wyolum/ClockFOUR/fabricate_bak/ClockFOUR_Chronogram_v2.1/Files to send Seeed/sides_C4_v2.1.pdf

ClockFOUR sides C4_v2.1

TOP = 276 x 20 x 3 mm

BOTTOM = 276 x 20 x 3 mm

LEFT = 270 x 20 x 3 mm

RIGHT = 270 x 20 x 3 mm
