wyolum/ClockFOUR/fabricate_bak/ClockFOUR_Chronogram_v2.1/output/english_upper Helvetica_C4_v2.1.pdf

english_upper Helvetica C4_v2.1 276x276x3mm

BACKWARDS!! DO NOT PRINT!!
