wyolum/ClockFOUR/fabricate_bak/ClockFOUR_Chronogram_v2.1/Files to send Seeed/ClockFOURChronogramInstructions.pdf

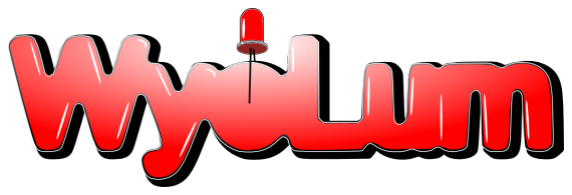
[picture p20: figure]

# ClockFOUR Chronogram Instructions

## Thank you for buying a Chronogram

Chronogram is a clock that tells the time with words. It has a 14x13 RGB pixel matrix that is powered by an external plugin 100-240V AC / 5V 3A power supply.

The clock has two main modes: Time mode and Seconds mode. You can switch between the modes by pressing the MODE button.

You can change the color palette of the clock by pressing the COLOR button. Each press will cycle the clock through the following color palettes:
- All white
- Solid color
- Slow color fade
- Rainbow color fade
- Random colors
- (all white)

Hold the color button to change the solid color. While the color button is held down you will see a circle that slowly changes color. When you see the desired color simply release the button and wait two seconds or tap the mode button.

Adjust the time by holding the MODE button for two seconds
- Adjust the hours slowly by tapping the COLOR button or quickly by holding it down. The hours will loop between 0 and 23 hours.
- When the correct hour is shown press the MODE button.
- Adjust the minutes slowly by tapping the COLOR button or quickly by holding the COLOR button down. The minutes will look between 0 and 59 minutes.
- When the correct minute is shown press the MODE button. The clock will return to time mode and also synchronize (zero) the seconds.

Pressing the RESET button will reboot the clock.

Caution:
Chronogram is designed to be enjoyed indoors only. It is not waterproof. Using a different power supply could damage the clock
