wyolum/ClockFOUR/fabricate/ClockFOUR_v1/output/baffles_v1_C4_v1.pdf

H baffle: 218x16x2mm; 14 per clock

V baffle: 216x14x2mm; 15 per clock

Localizer: Rout=4mm, Rin=1.5mm; 12 per clock

ClockFOUR_v1 Baffles 2mm BLACK Acrylic
