wyolum/ClockFOUR/fabricate/ClockFOUR_v1/output/english_C4_v1_lower Helvetica_C4_v1.pdf

english_C4_v1_lower Helvetica C4_v1

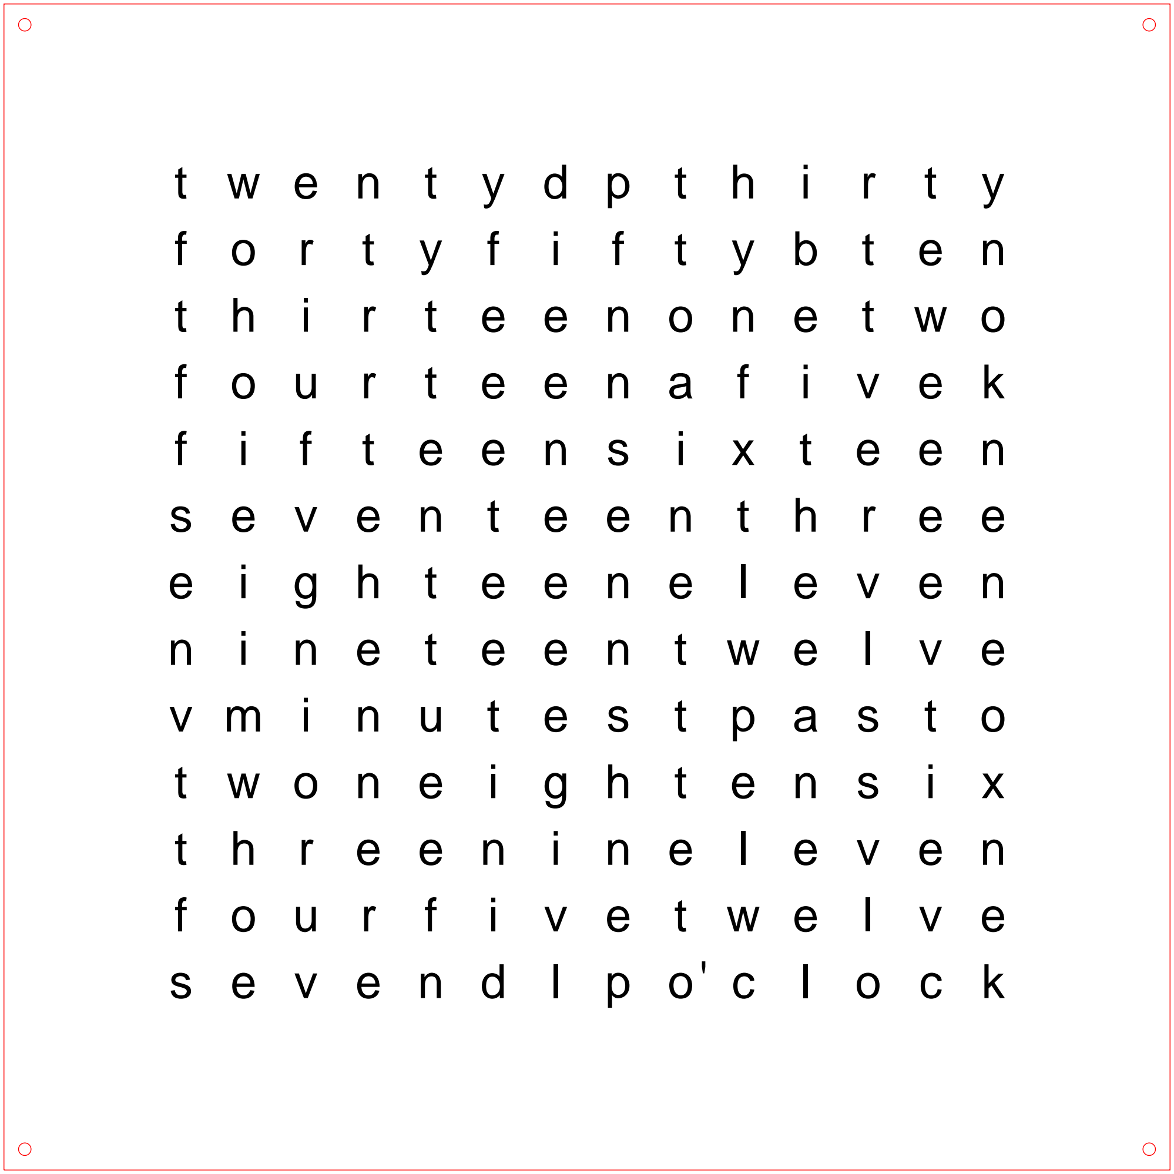
[picture p21: figure]

BACKWARDS!! DO NOT PRINT!!
