wyolum/ClockFOUR/fabricate/30x30 size/output/baffles_jr_30_1.0.pdf

H baffle: 15 per clock

V baffle: 14 per clock

Clock30_v1 Baffles 2mm BLACK Acrylic
