wyolum/ClockFOUR/fabricate/Vertical A4 10x10/output/baffles_VA4_30_1.0.pdf

H baffle: 11 per clock

V baffle: 11 per clock

ClockFOUR_VA4 Baffles 2mm BLACK Acrylic
