wyolum/ClockFOUR/fabricate/Vertical A4 10x10/output/Vertical A4.pdf

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
‘ | k

•

•

•

•
