wyolum/ClockFOUR/fabricate/30x30 size/output/english_30_UPPER Codystar-Regular_30_1.0.pdf

english_30_UPPER Codystar-Regular 30_1.0

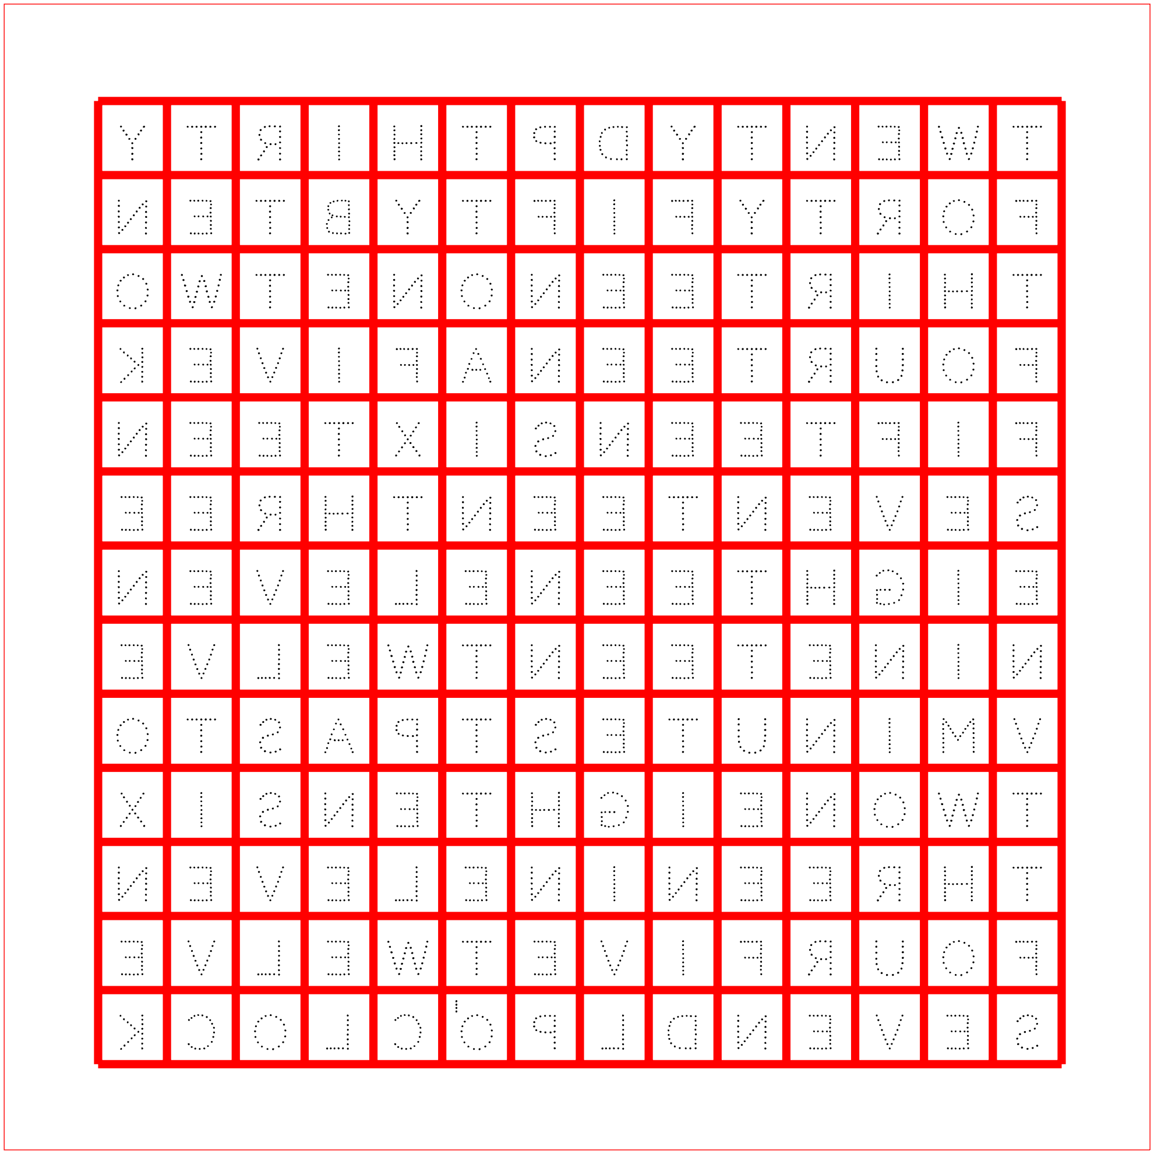
[picture p28: figure]
