wyolum/ClockFOUR/fabricate/A4 size/output/baffles_jr_TiM_1.0.pdf

H baffle: 9 per clock

V baffle: 17 per clock

localizer: 0 per clock

ClockTiM_v1 Baffles 0.06" BLACK Acrylic
