wyolum/ClockFOUR/fabricate/A4 size/output/english_TiM_lower Helvetica_TiM_1.0.pdf

english_TiM_lower Helvetica TiM_1.0

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

'
