wyolum/ClockFOUR/fabricate/Power_Socket_Bracket/C4_bracket_03.png

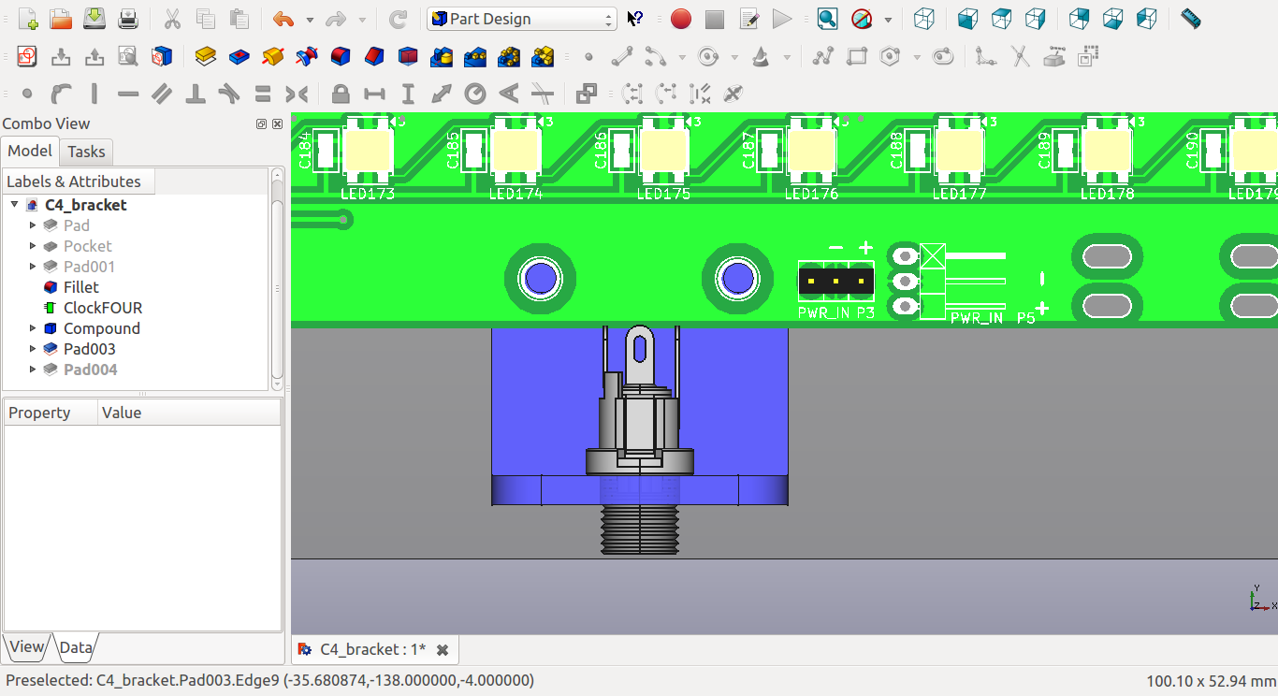
fabricate/Power_Socket_Bracket/C4_bracket_03.png
