wyolum/ClockFOUR/fabricate_bak/ClockFOUR_Chronogram_v2.1/C4 sides diagram.png

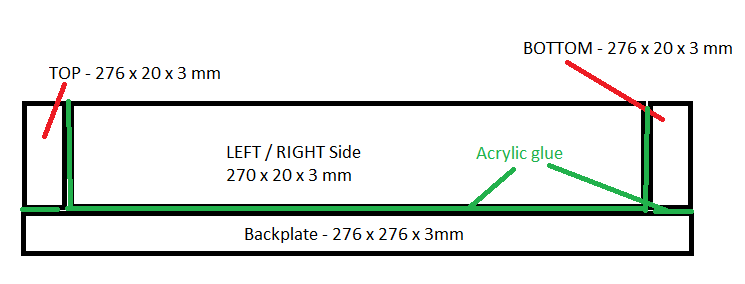
fabricate_bak/ClockFOUR_Chronogram_v2.1/C4 sides diagram.png
