wyolum/ClockFOUR/fabricate_bak/ClockFOUR_Chronogram_v2.1/Files to send Seeed/C4_v2 PCB (Same as v2.1)/ClockFOUR-B_SilkS.pdf

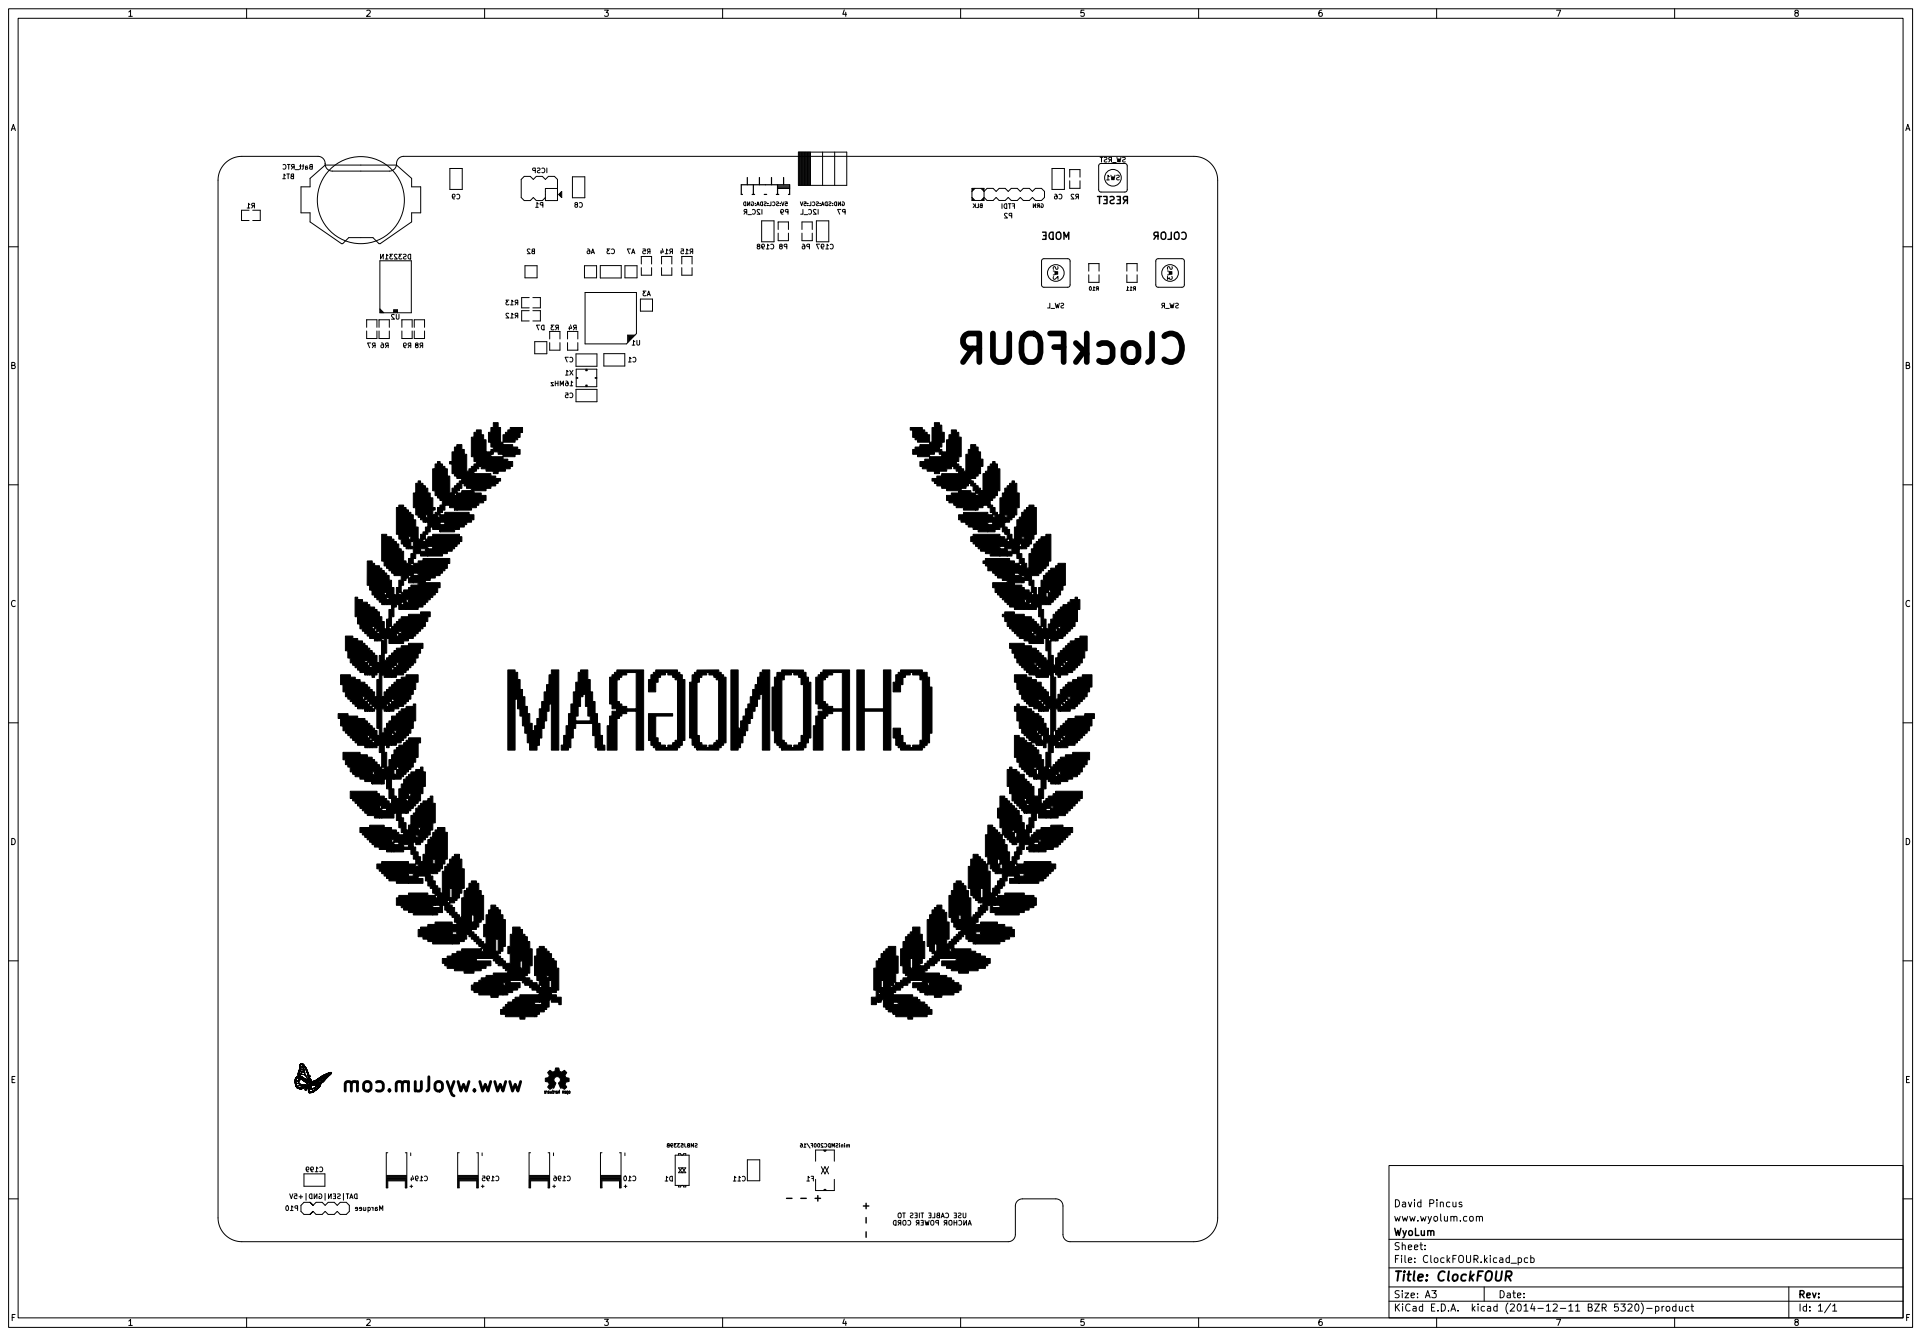
[picture p40: page 1]

David Pincus
www.wyolum.com
File: ClockFOUR.kicad_pcb Sheet: WyoLum
