wyolum/ClockFOUR/fabricate_bak/ClockFOUR_Chronogram_v2.1/Files to send Seeed/C4_v2 PCB (Same as v2.1)/ClockFOUR.pdf

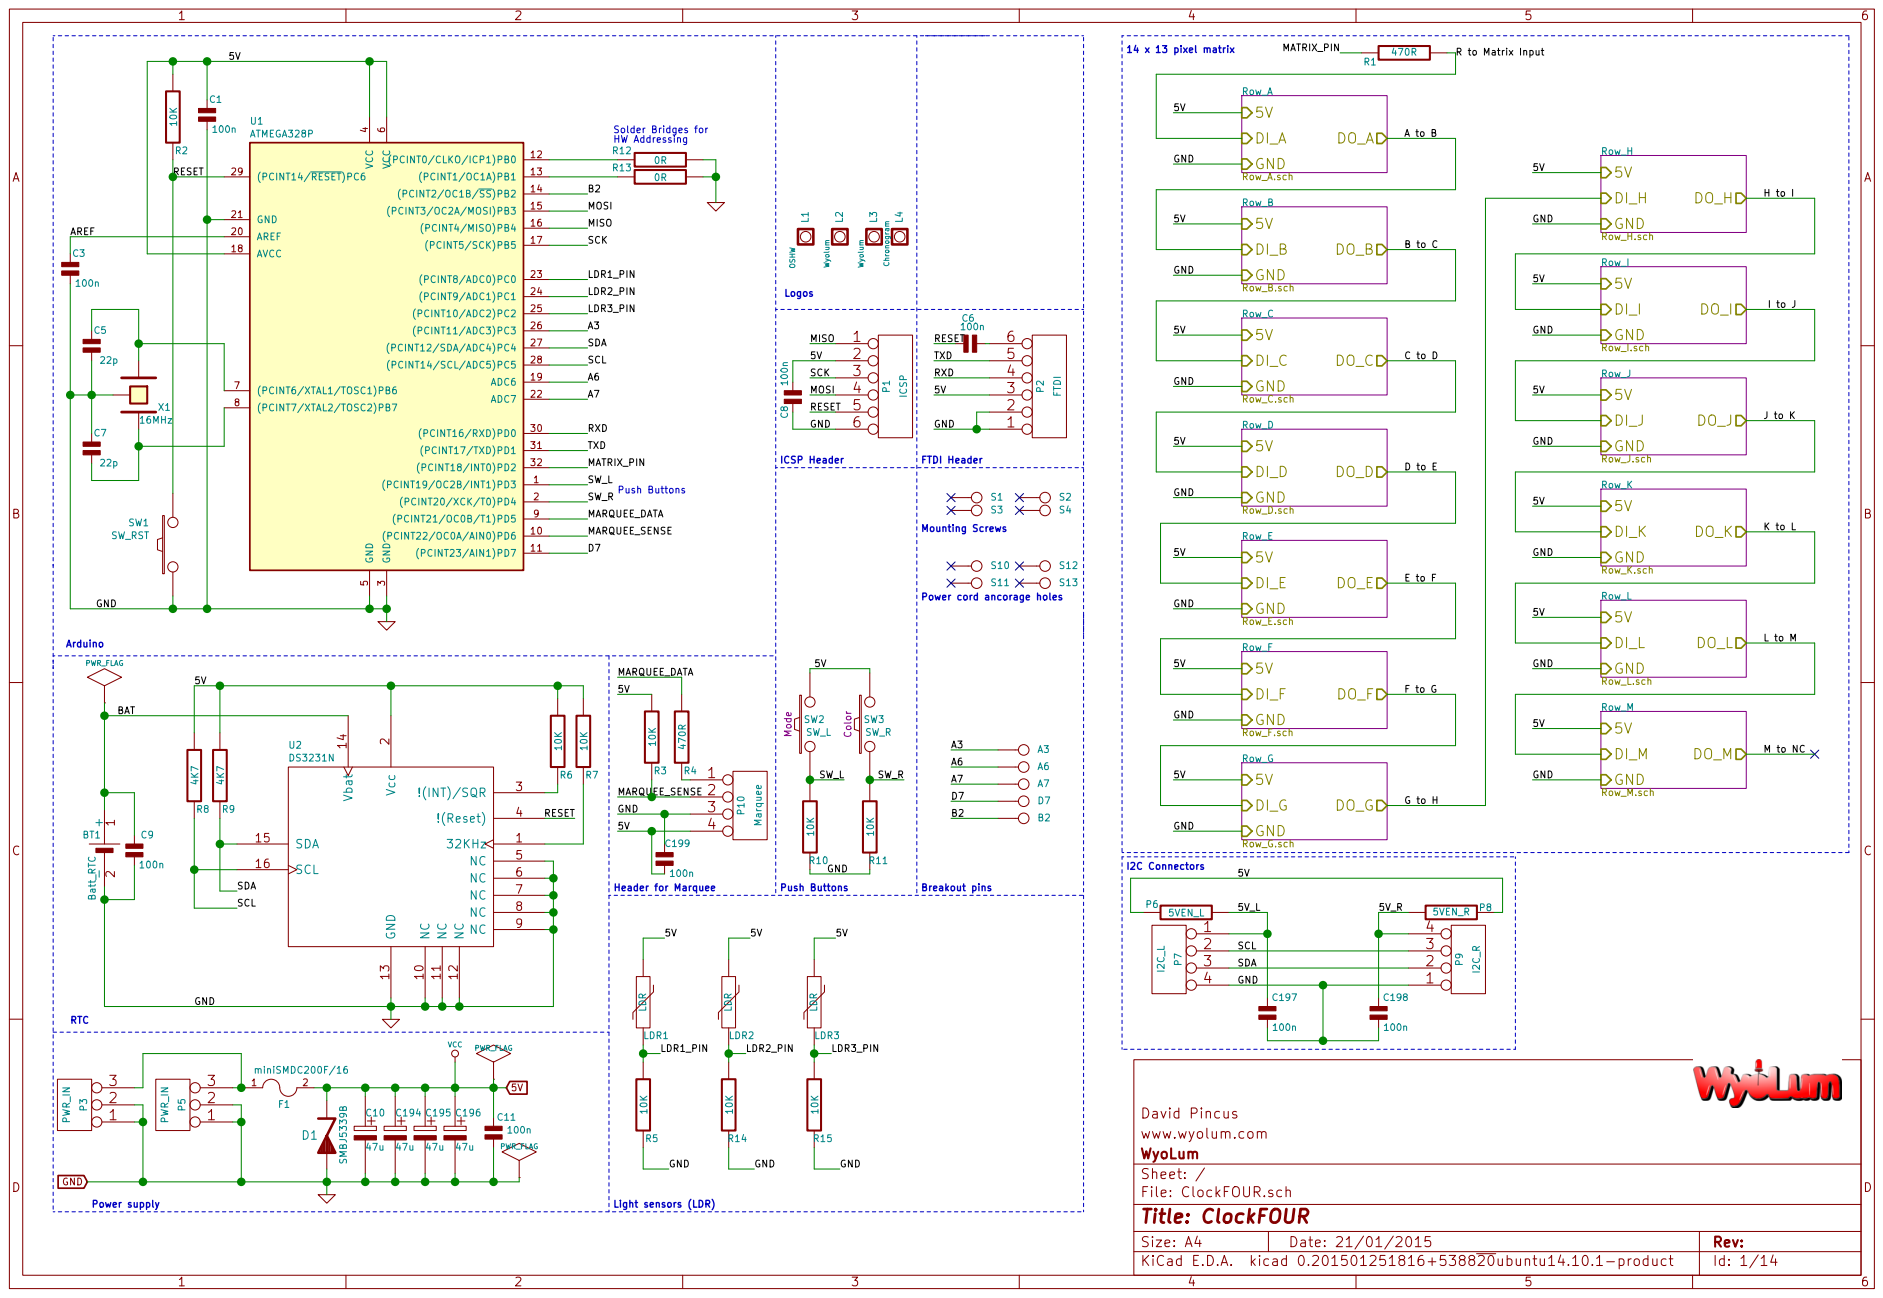
[picture p44: page 1]

100n RESET

5V Row_C.sch DI_C GND | DO_C

(PCINT6/XTAL1/TOSC1)PB6 7

5V GND

www.wyolum.com
File: ClockFOUR.sch Sheet: / WyoLum

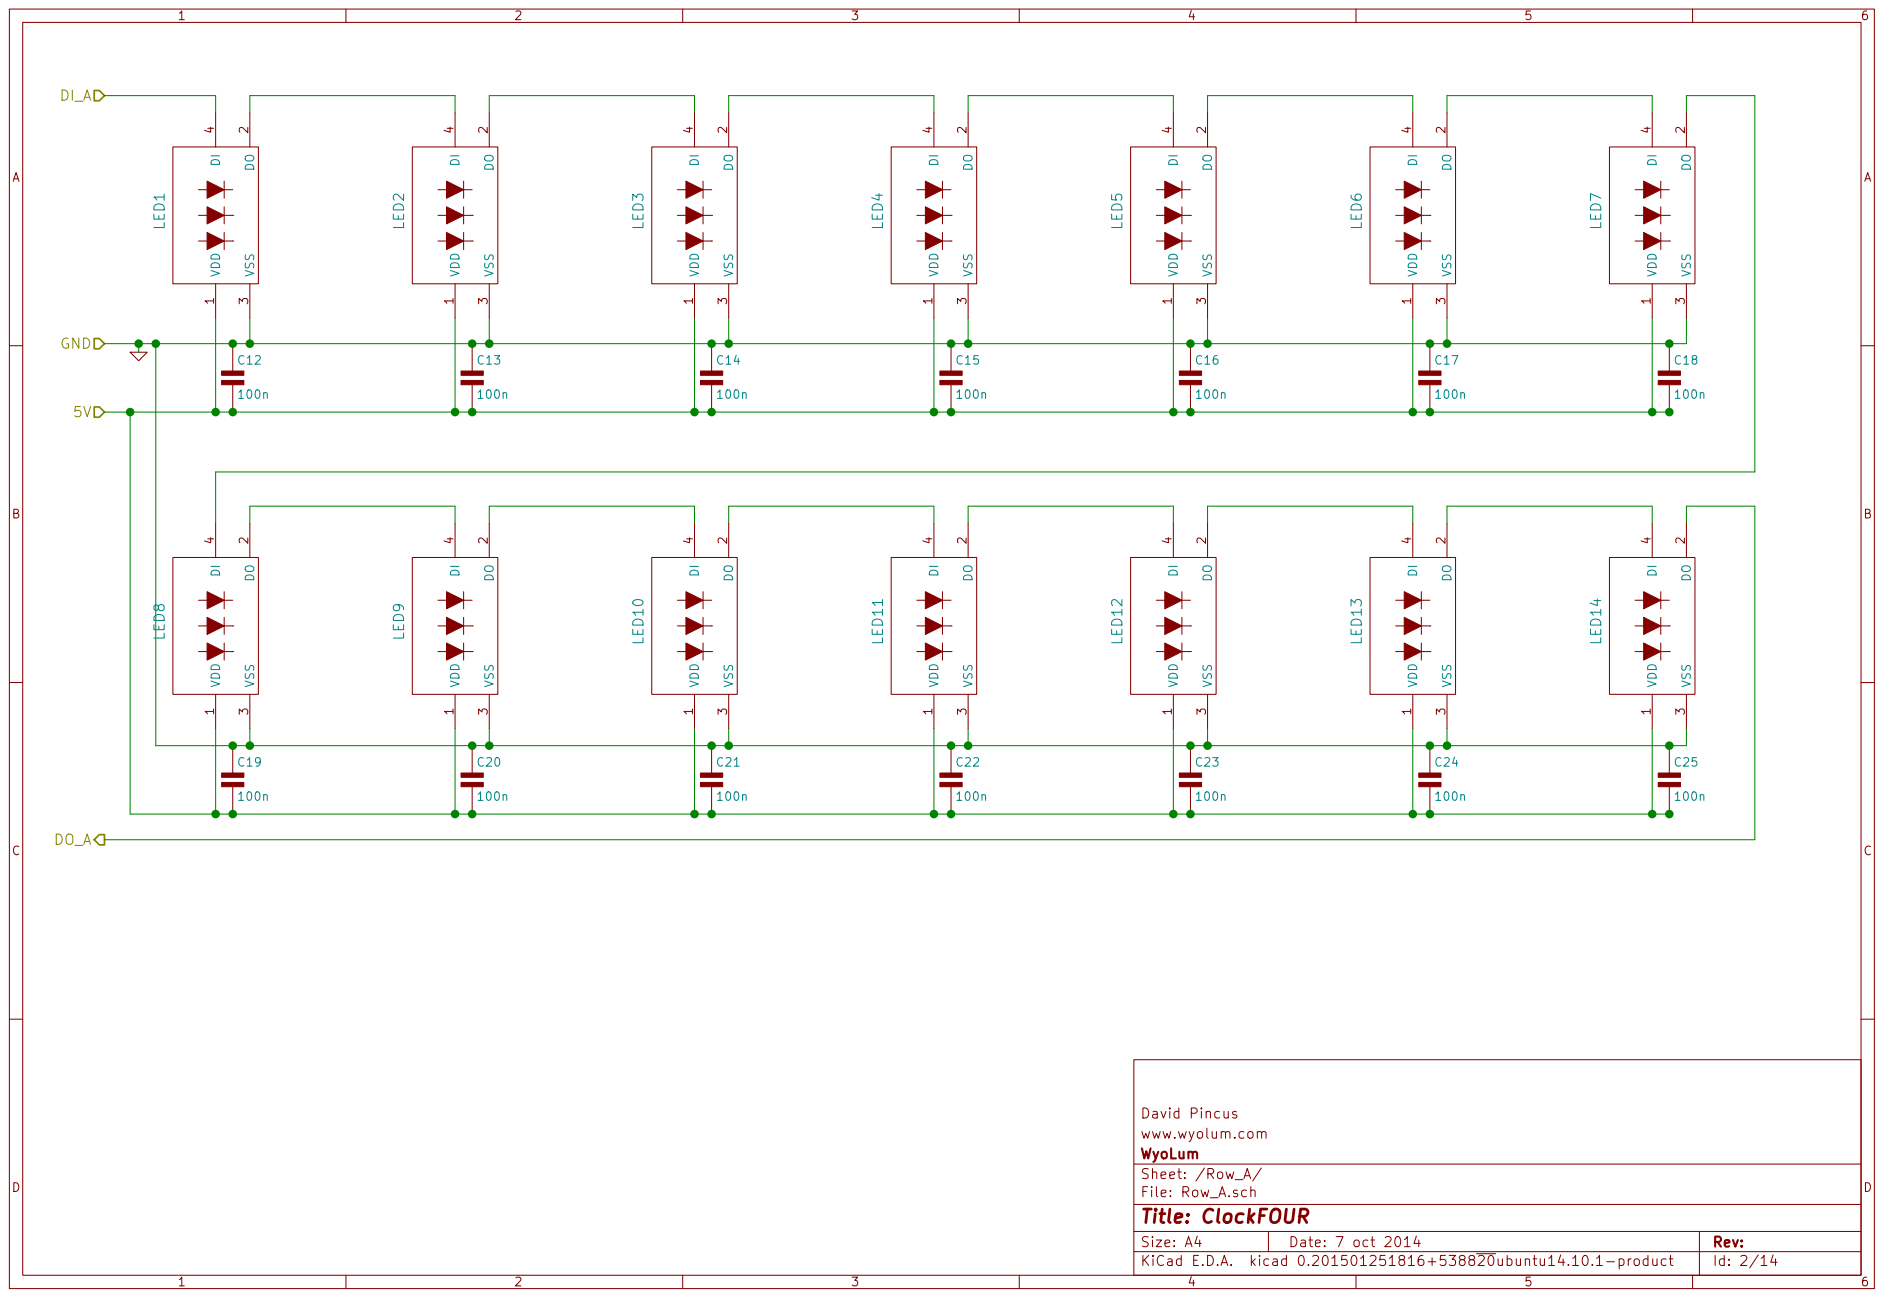
[picture p45: page 2]

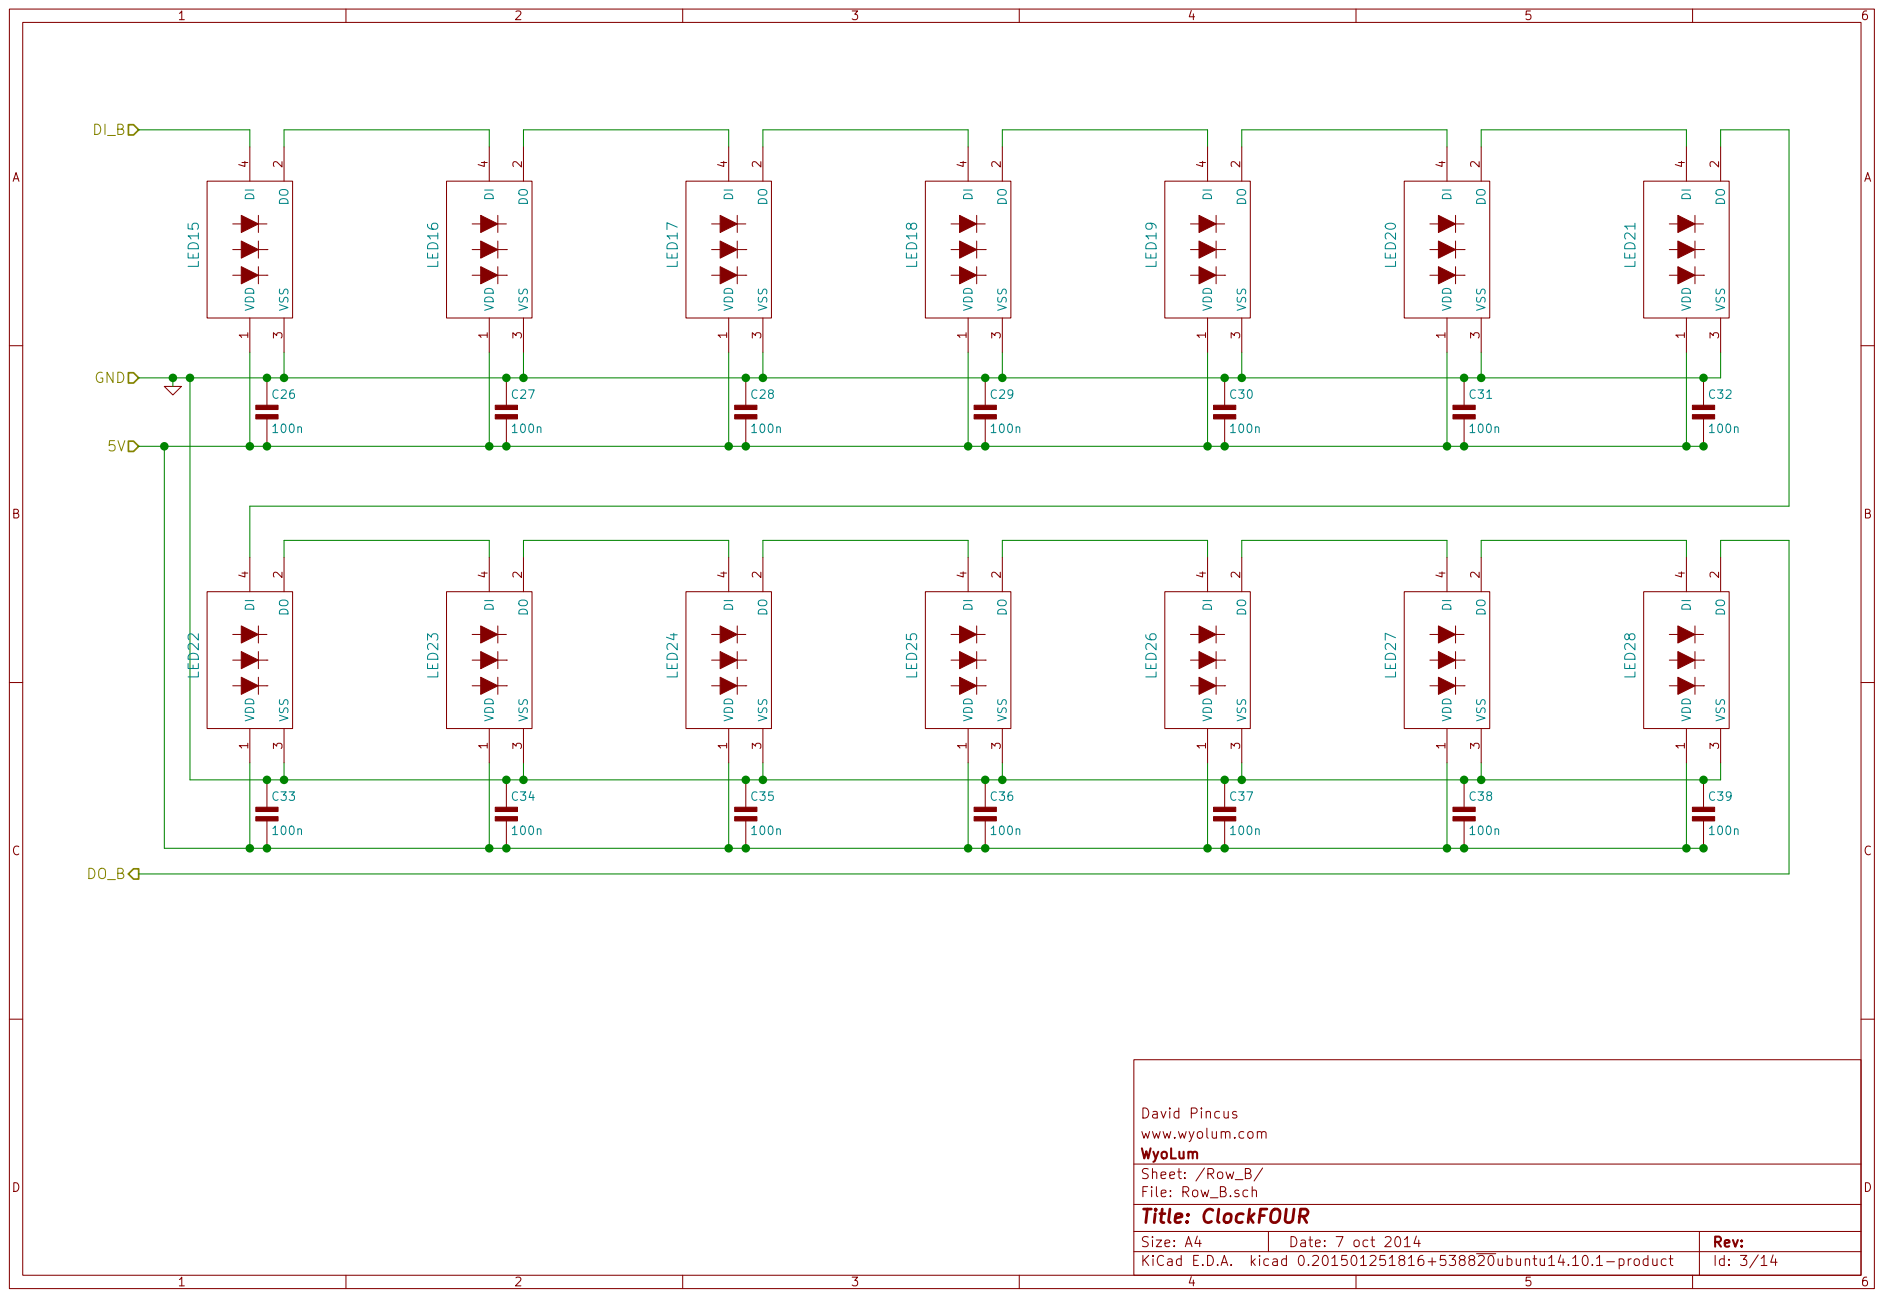
[picture p46: page 3]

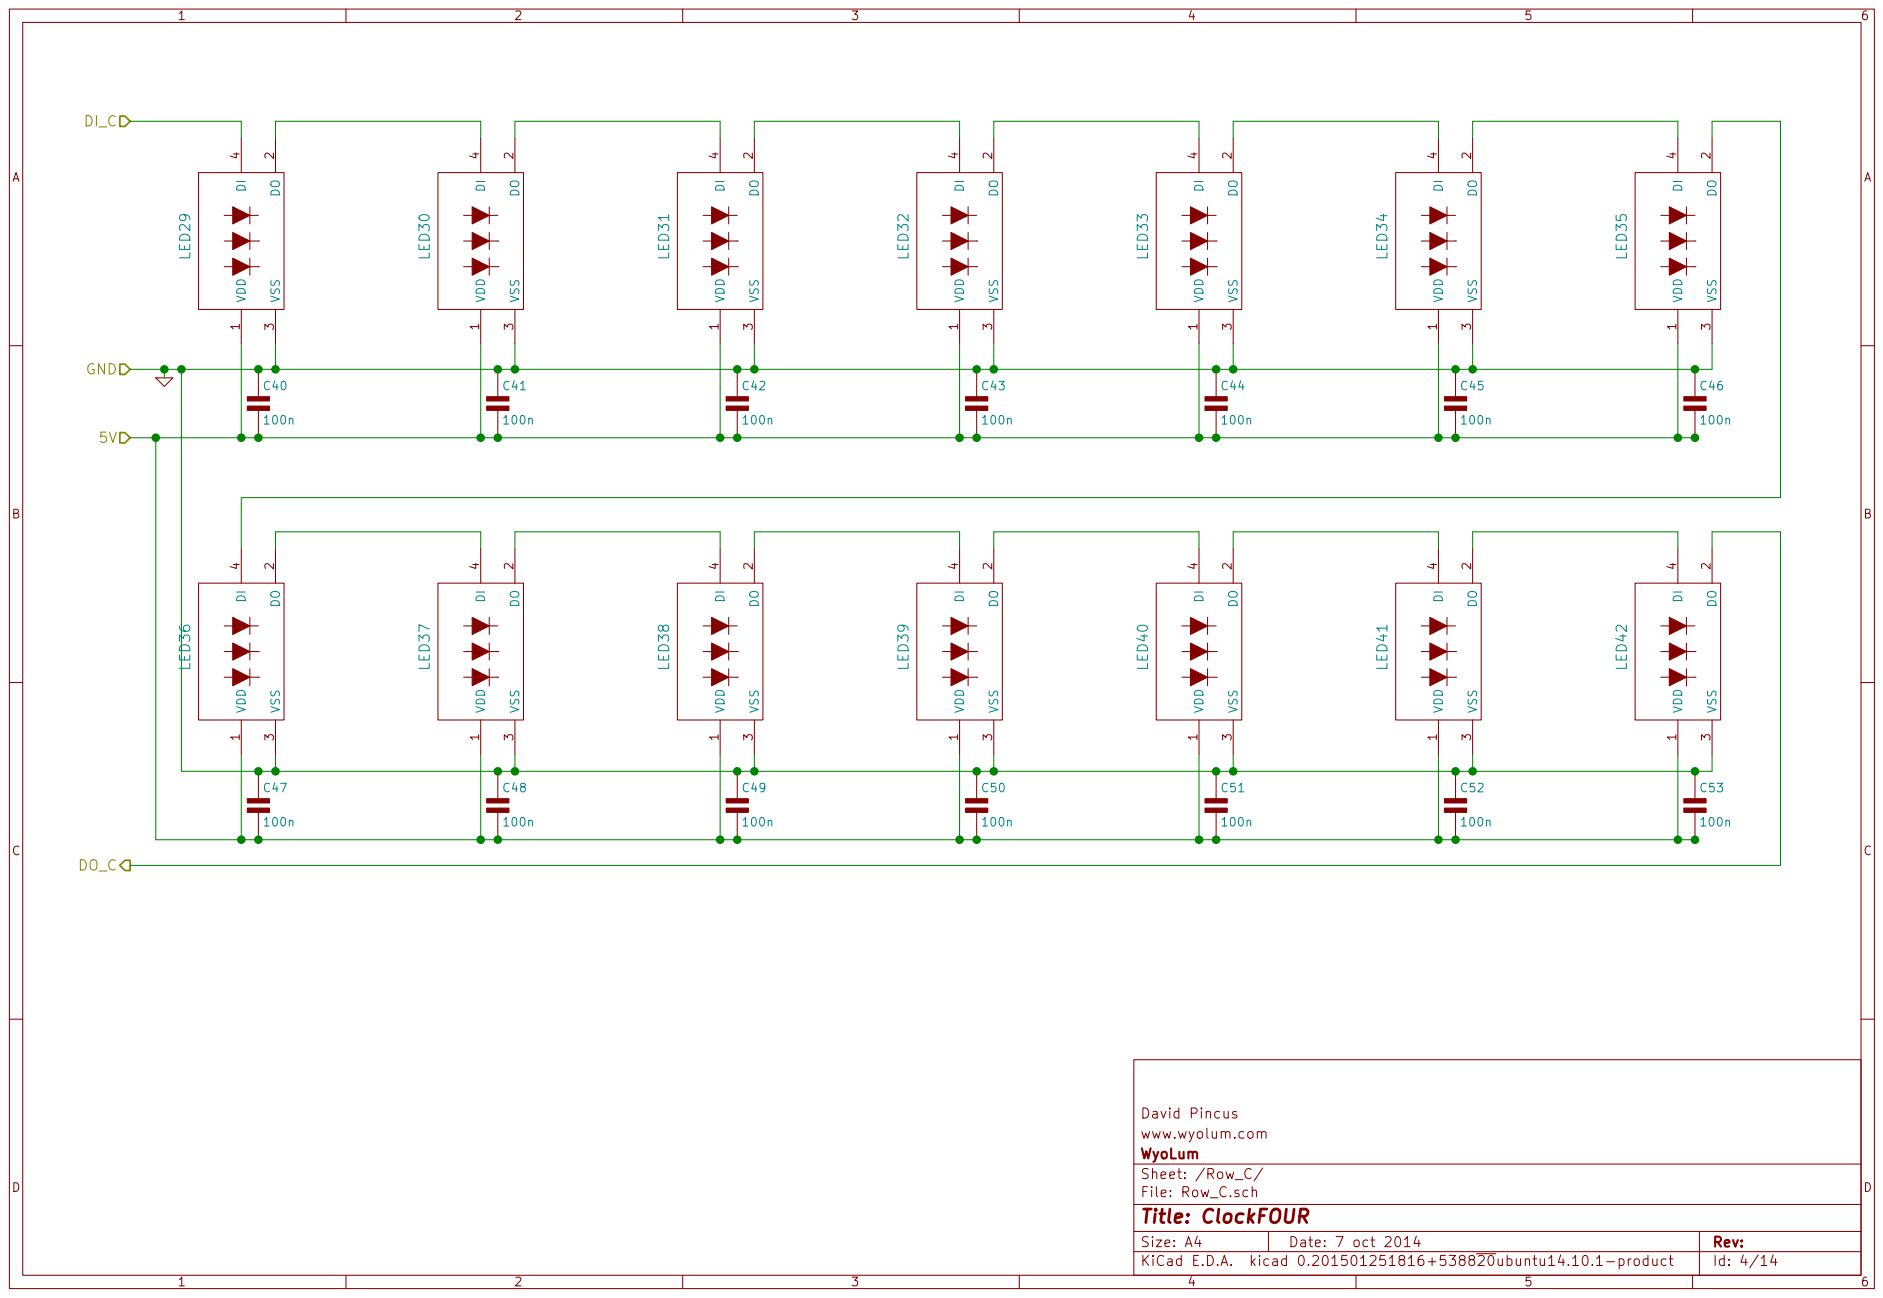
[picture p47: page 4]

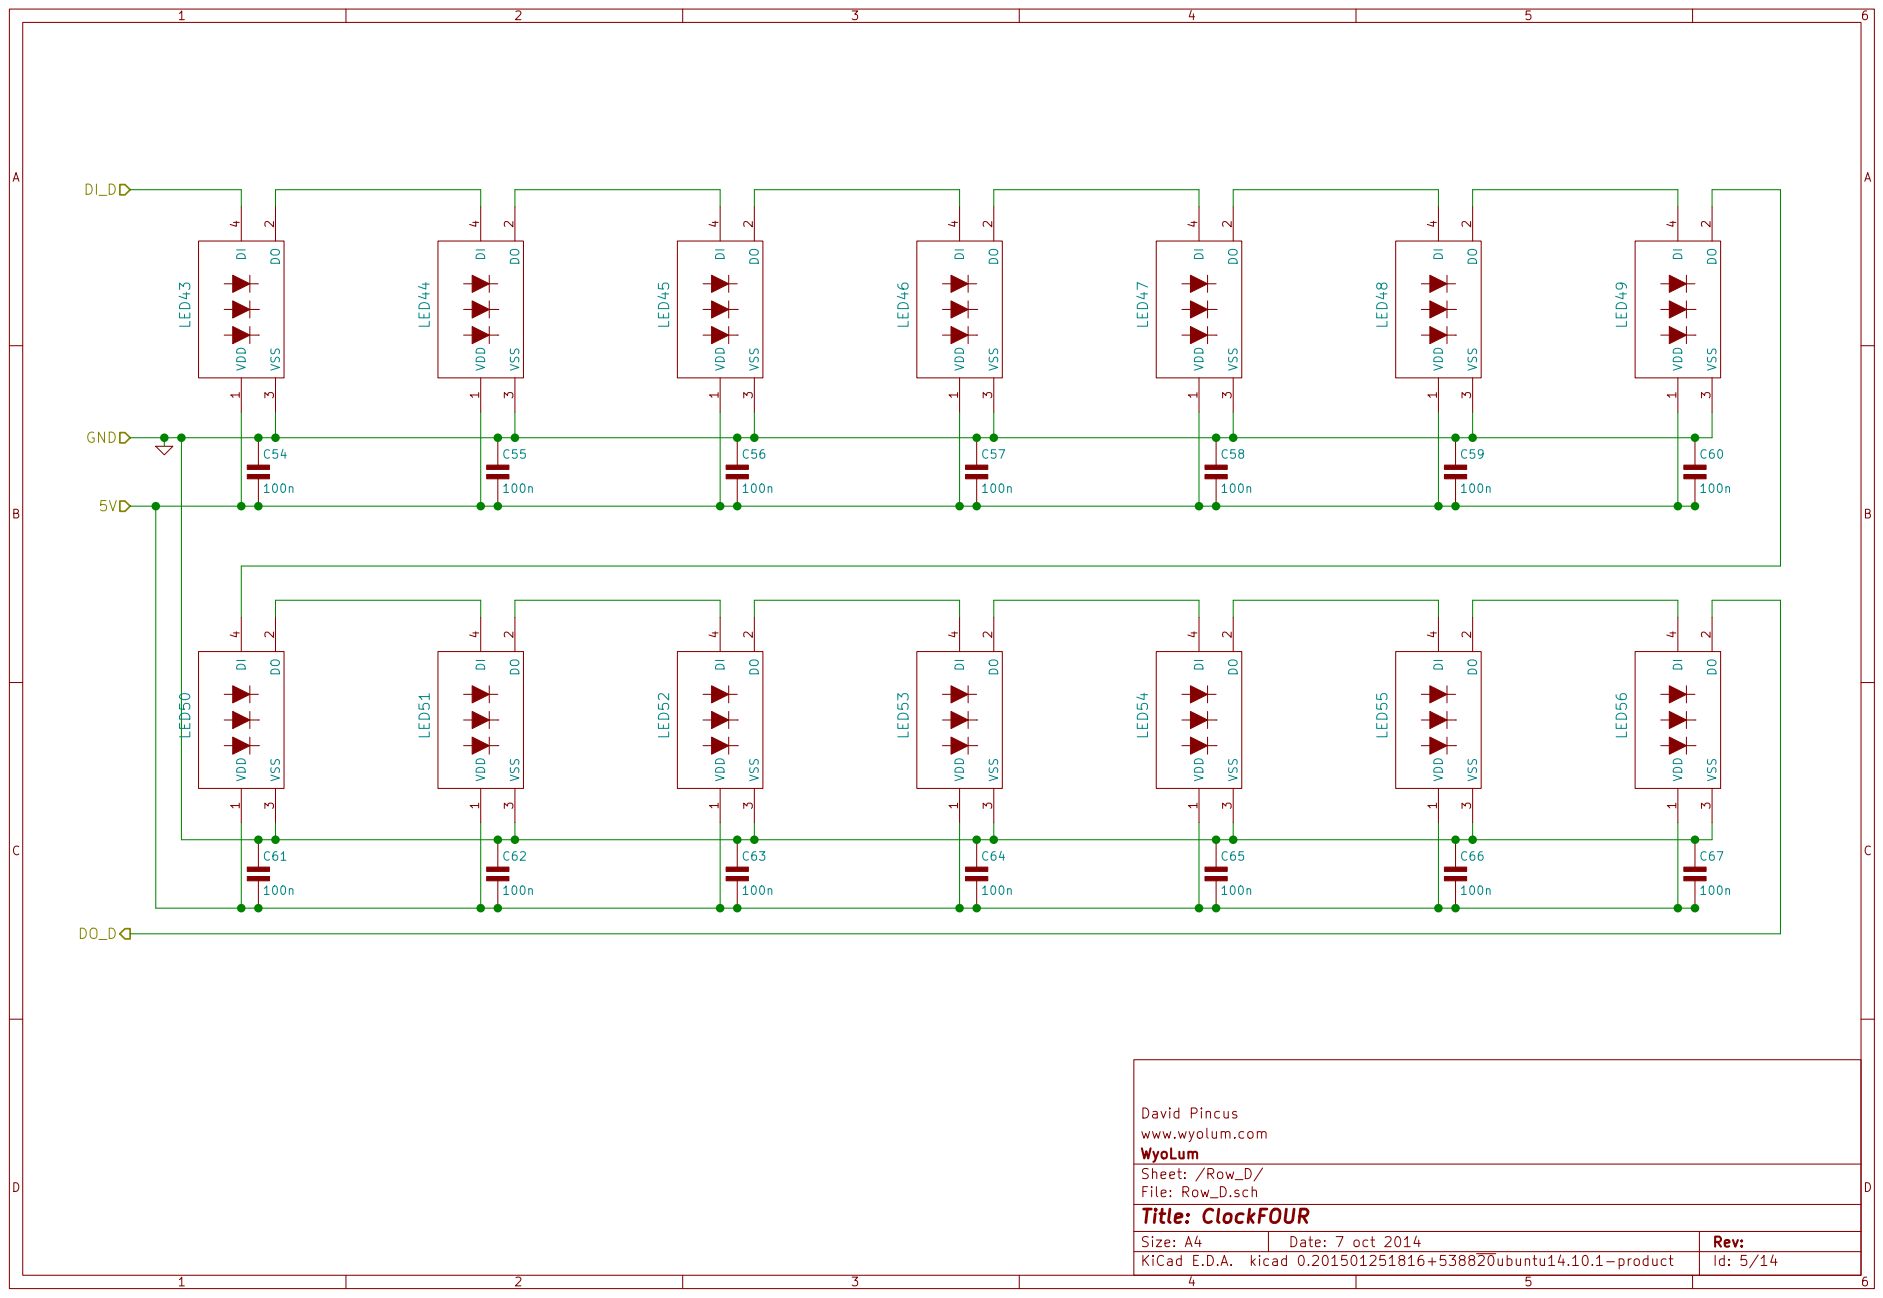
[picture p48: page 5]

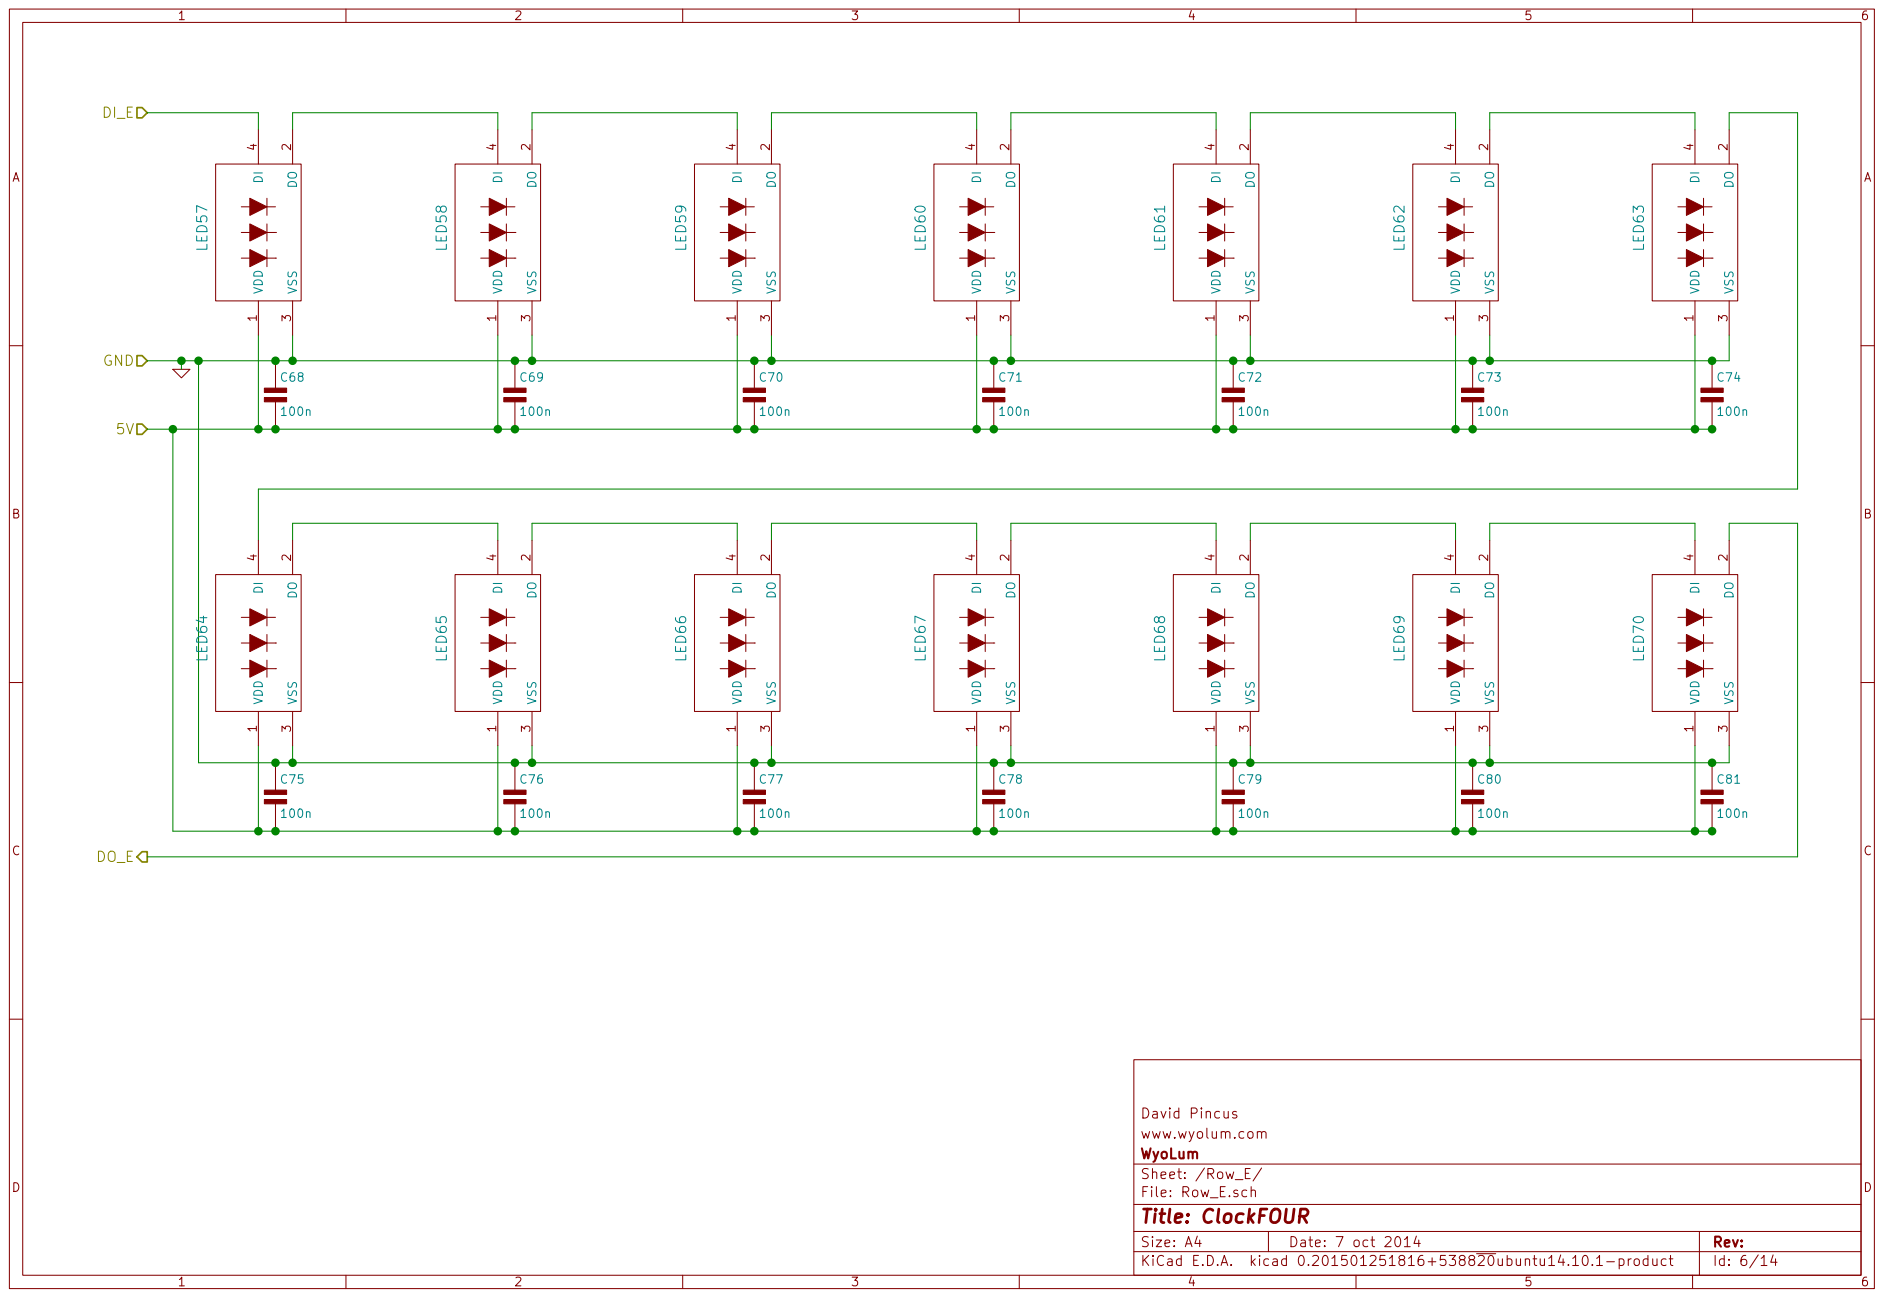
[picture p49: page 6]

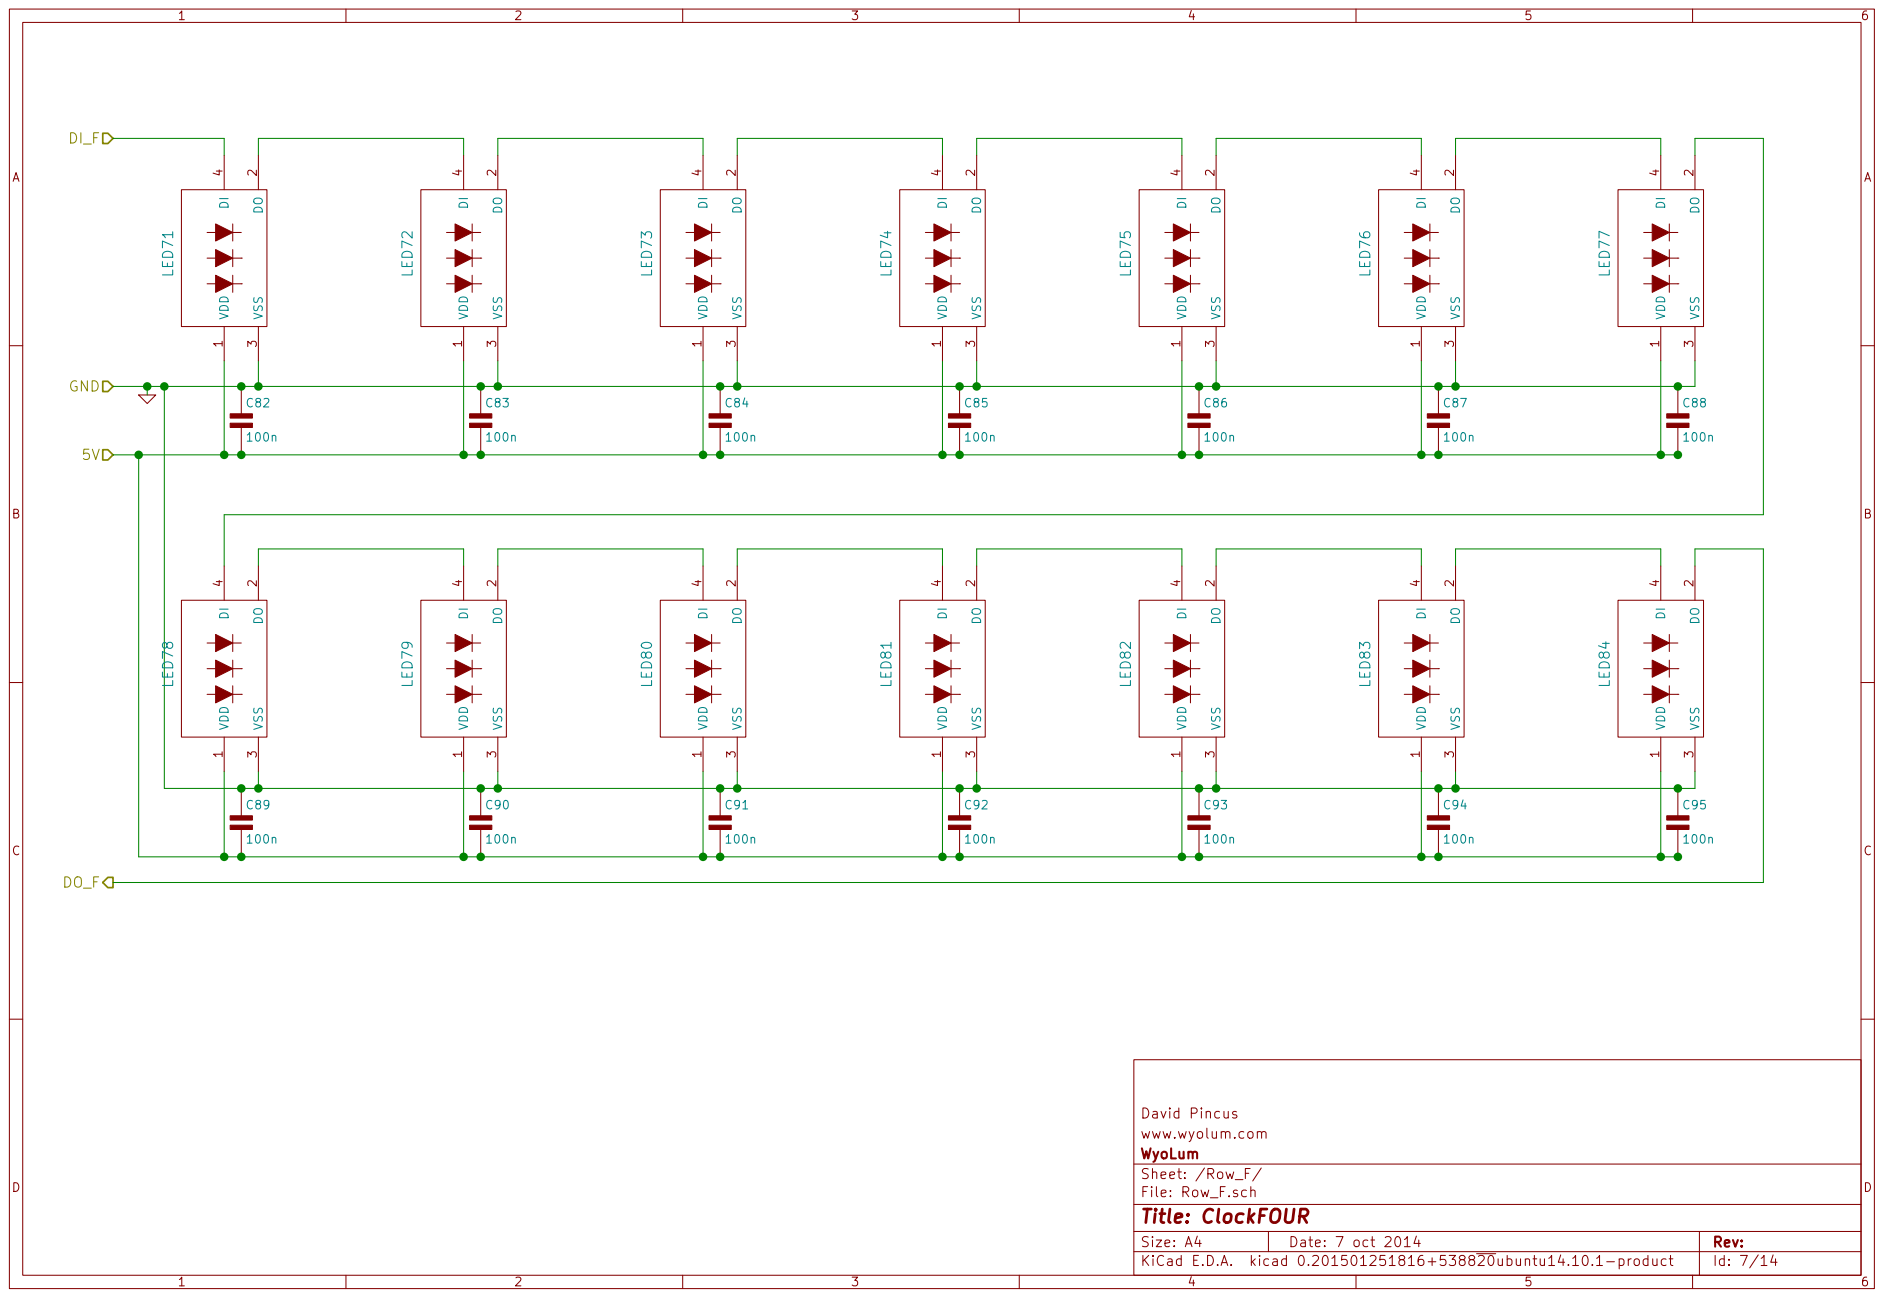
[picture p50: page 7]

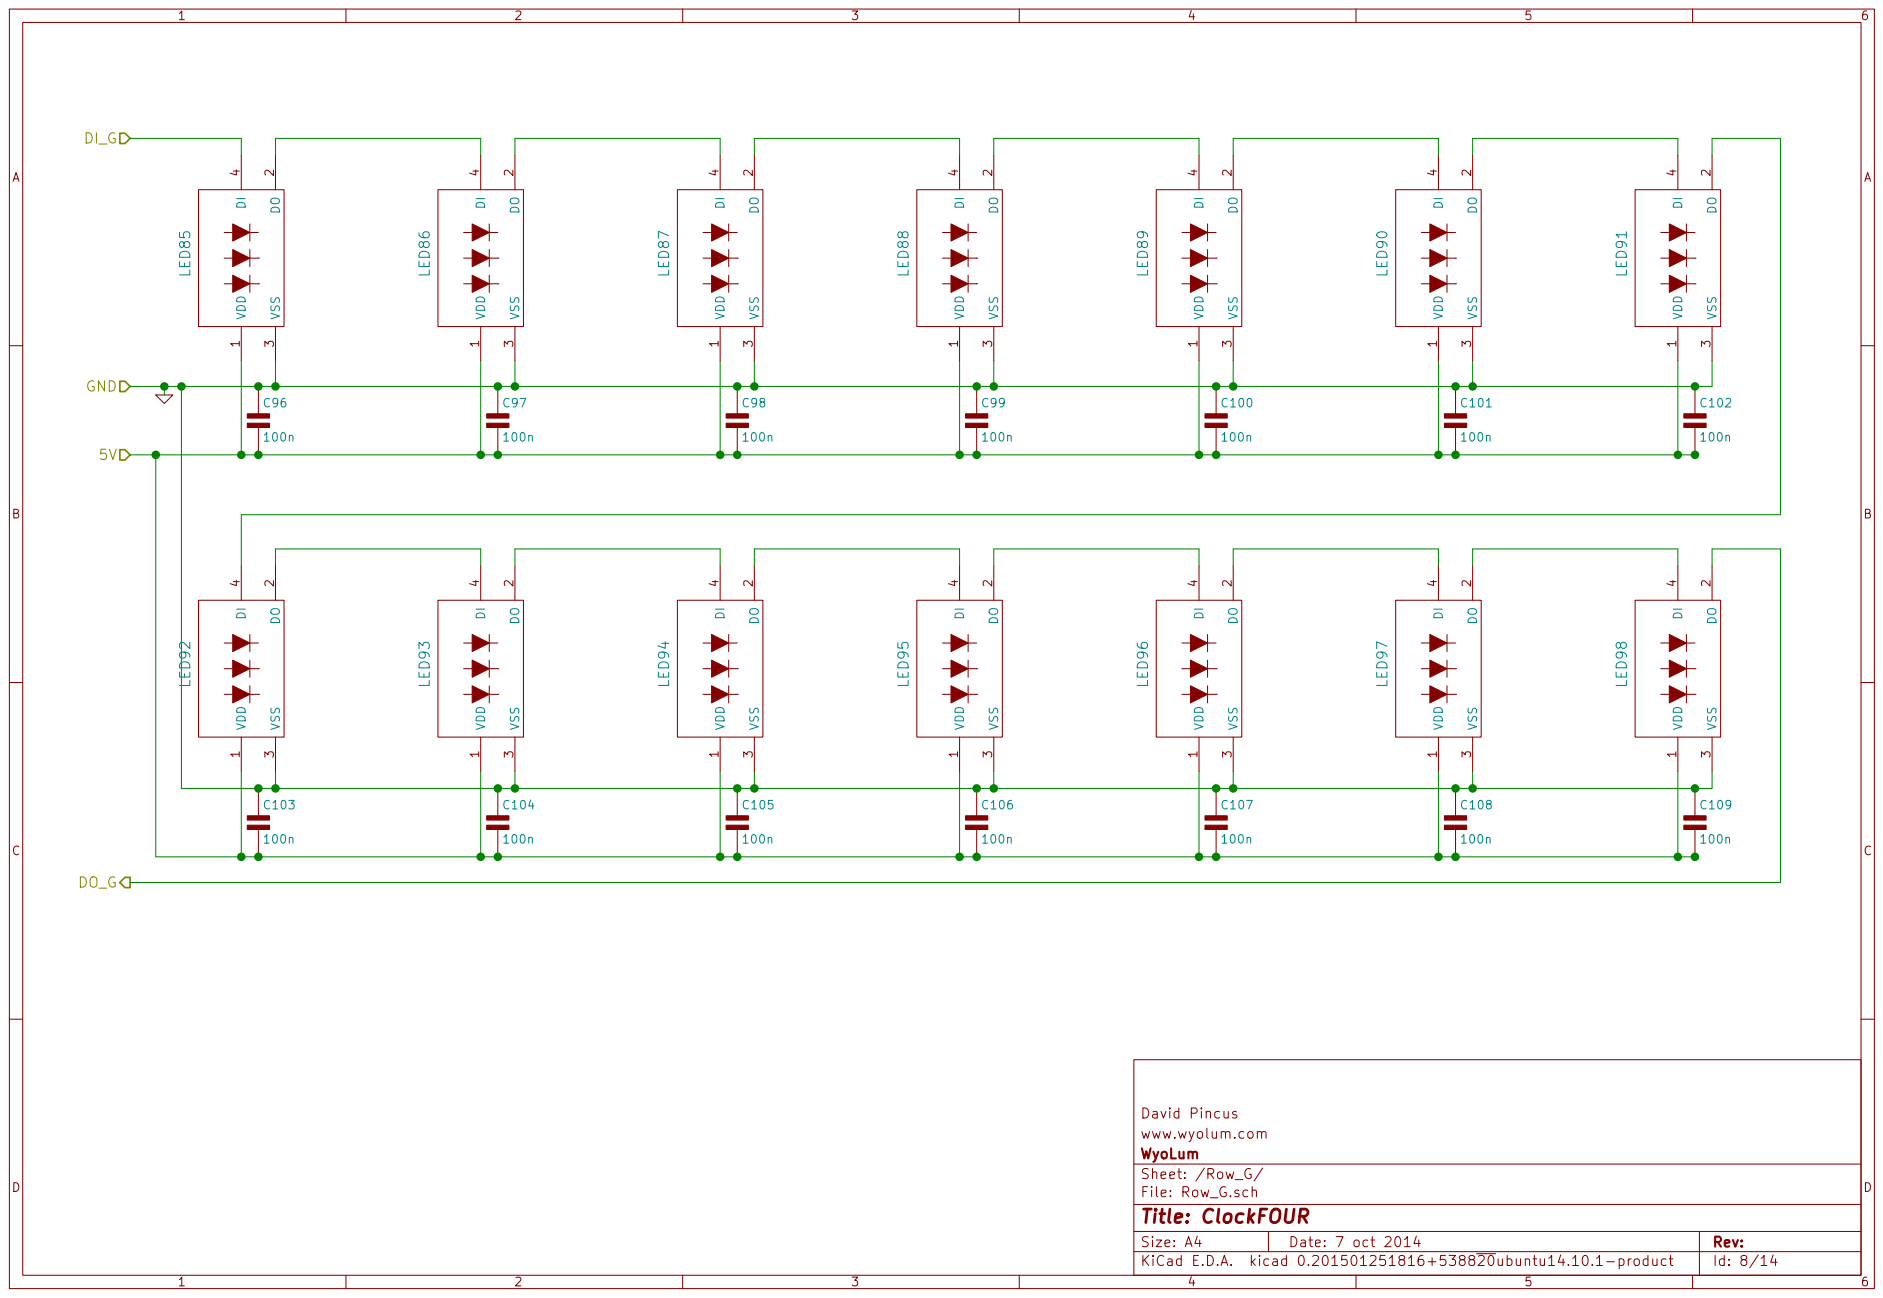
[picture p51: page 8]

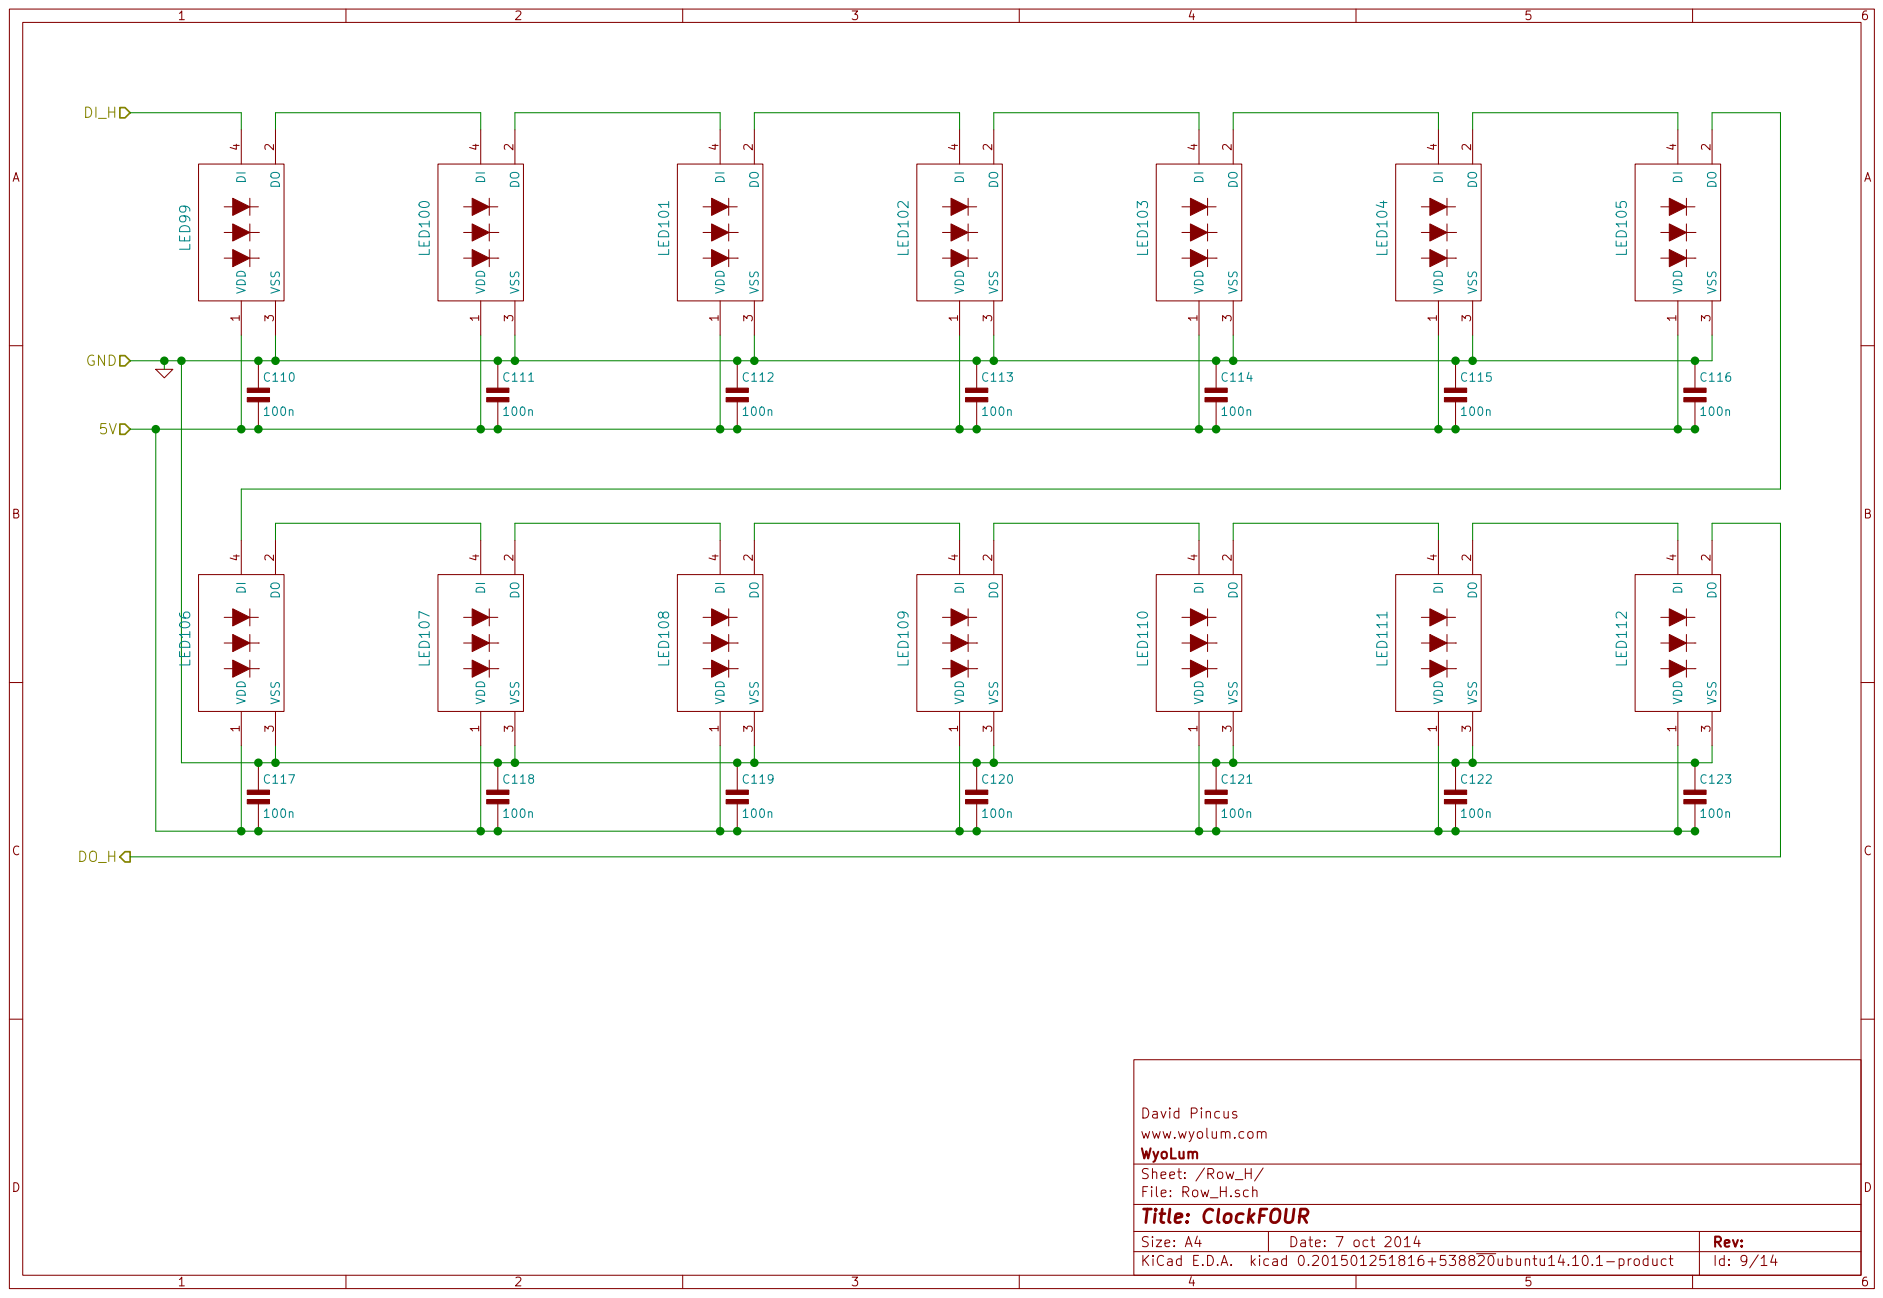
[picture p52: page 9]

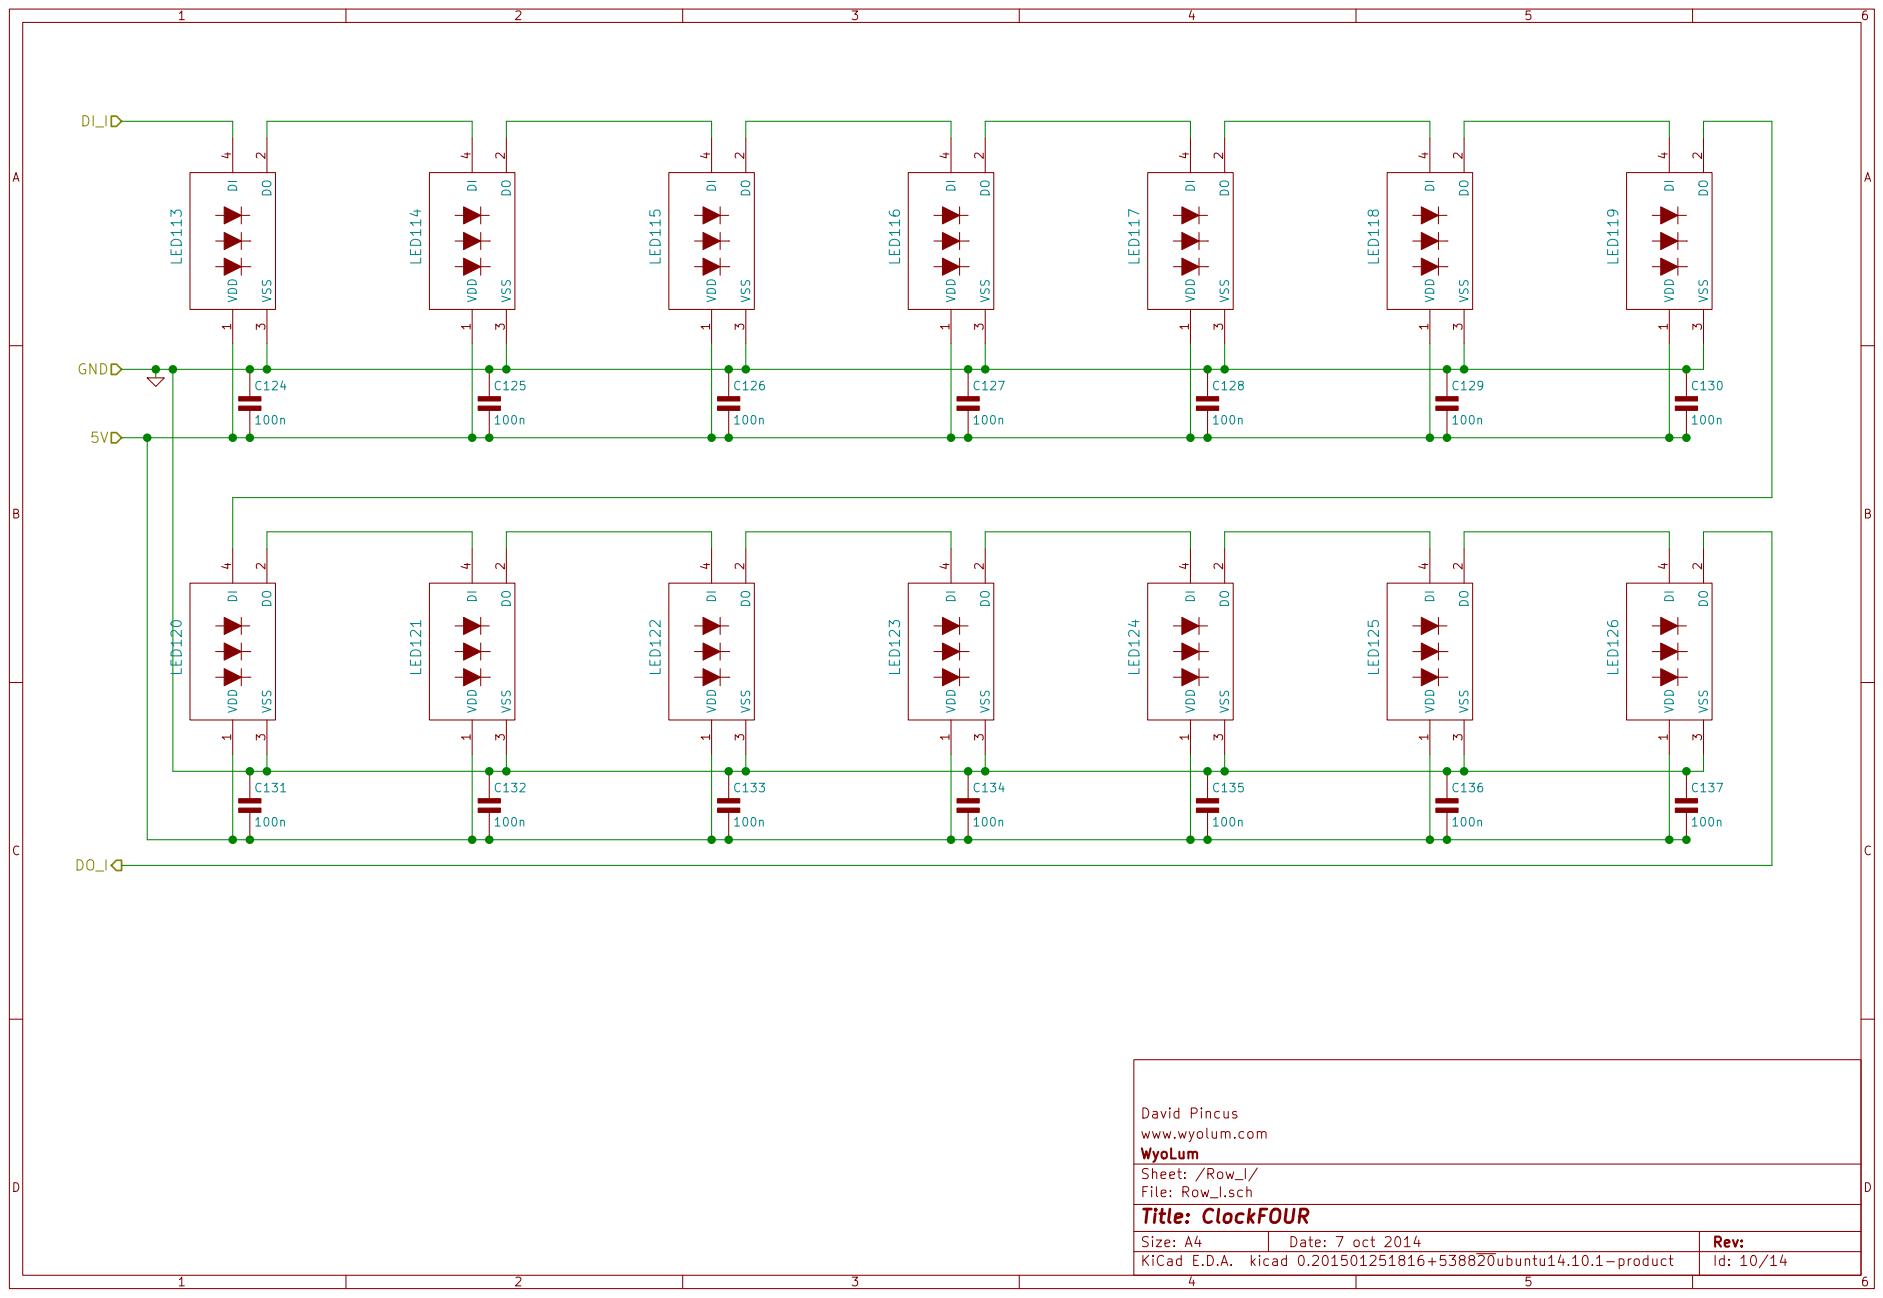
[picture p53: page 10]

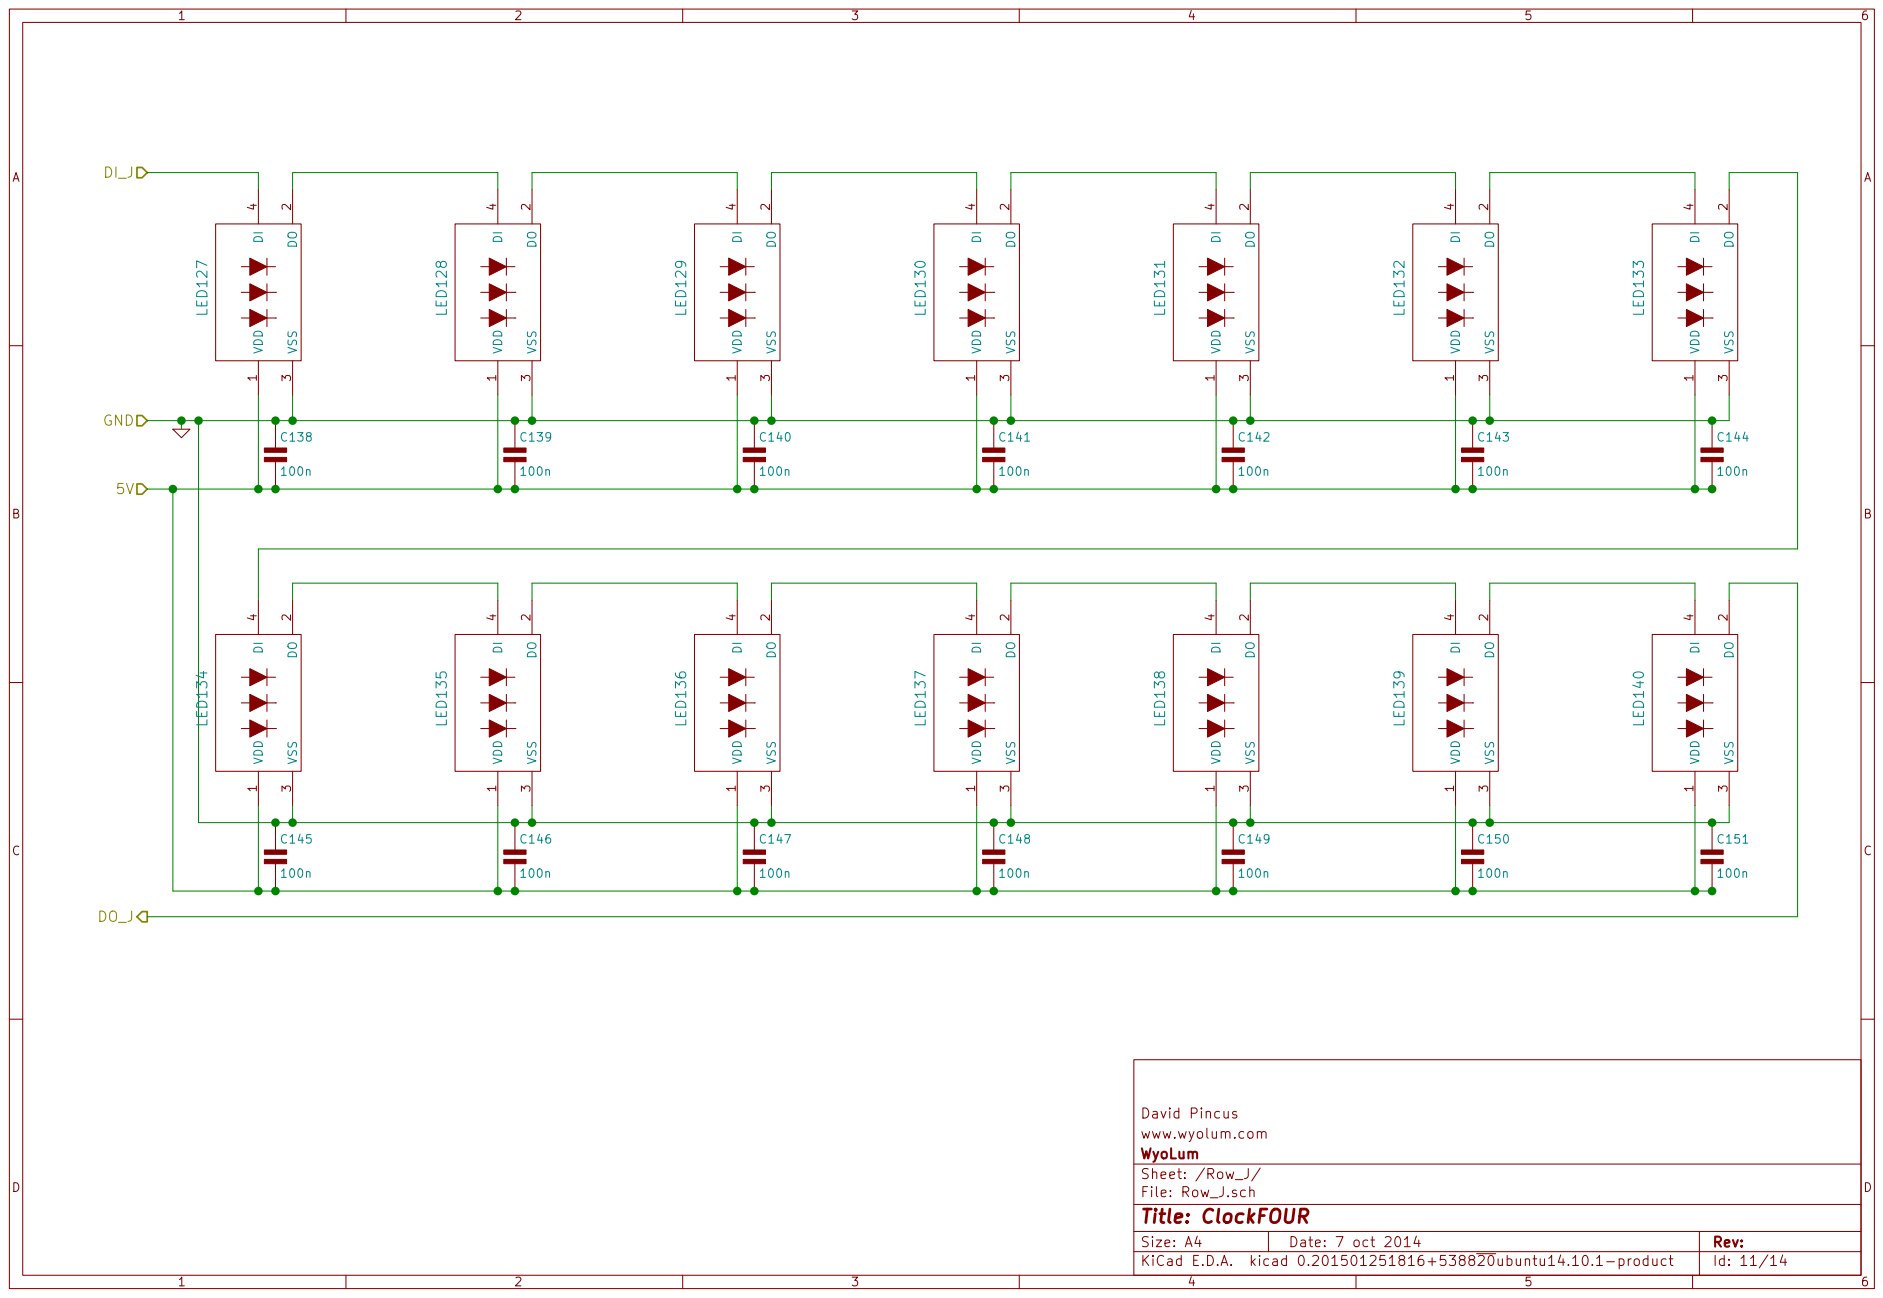
[picture p54: page 11]

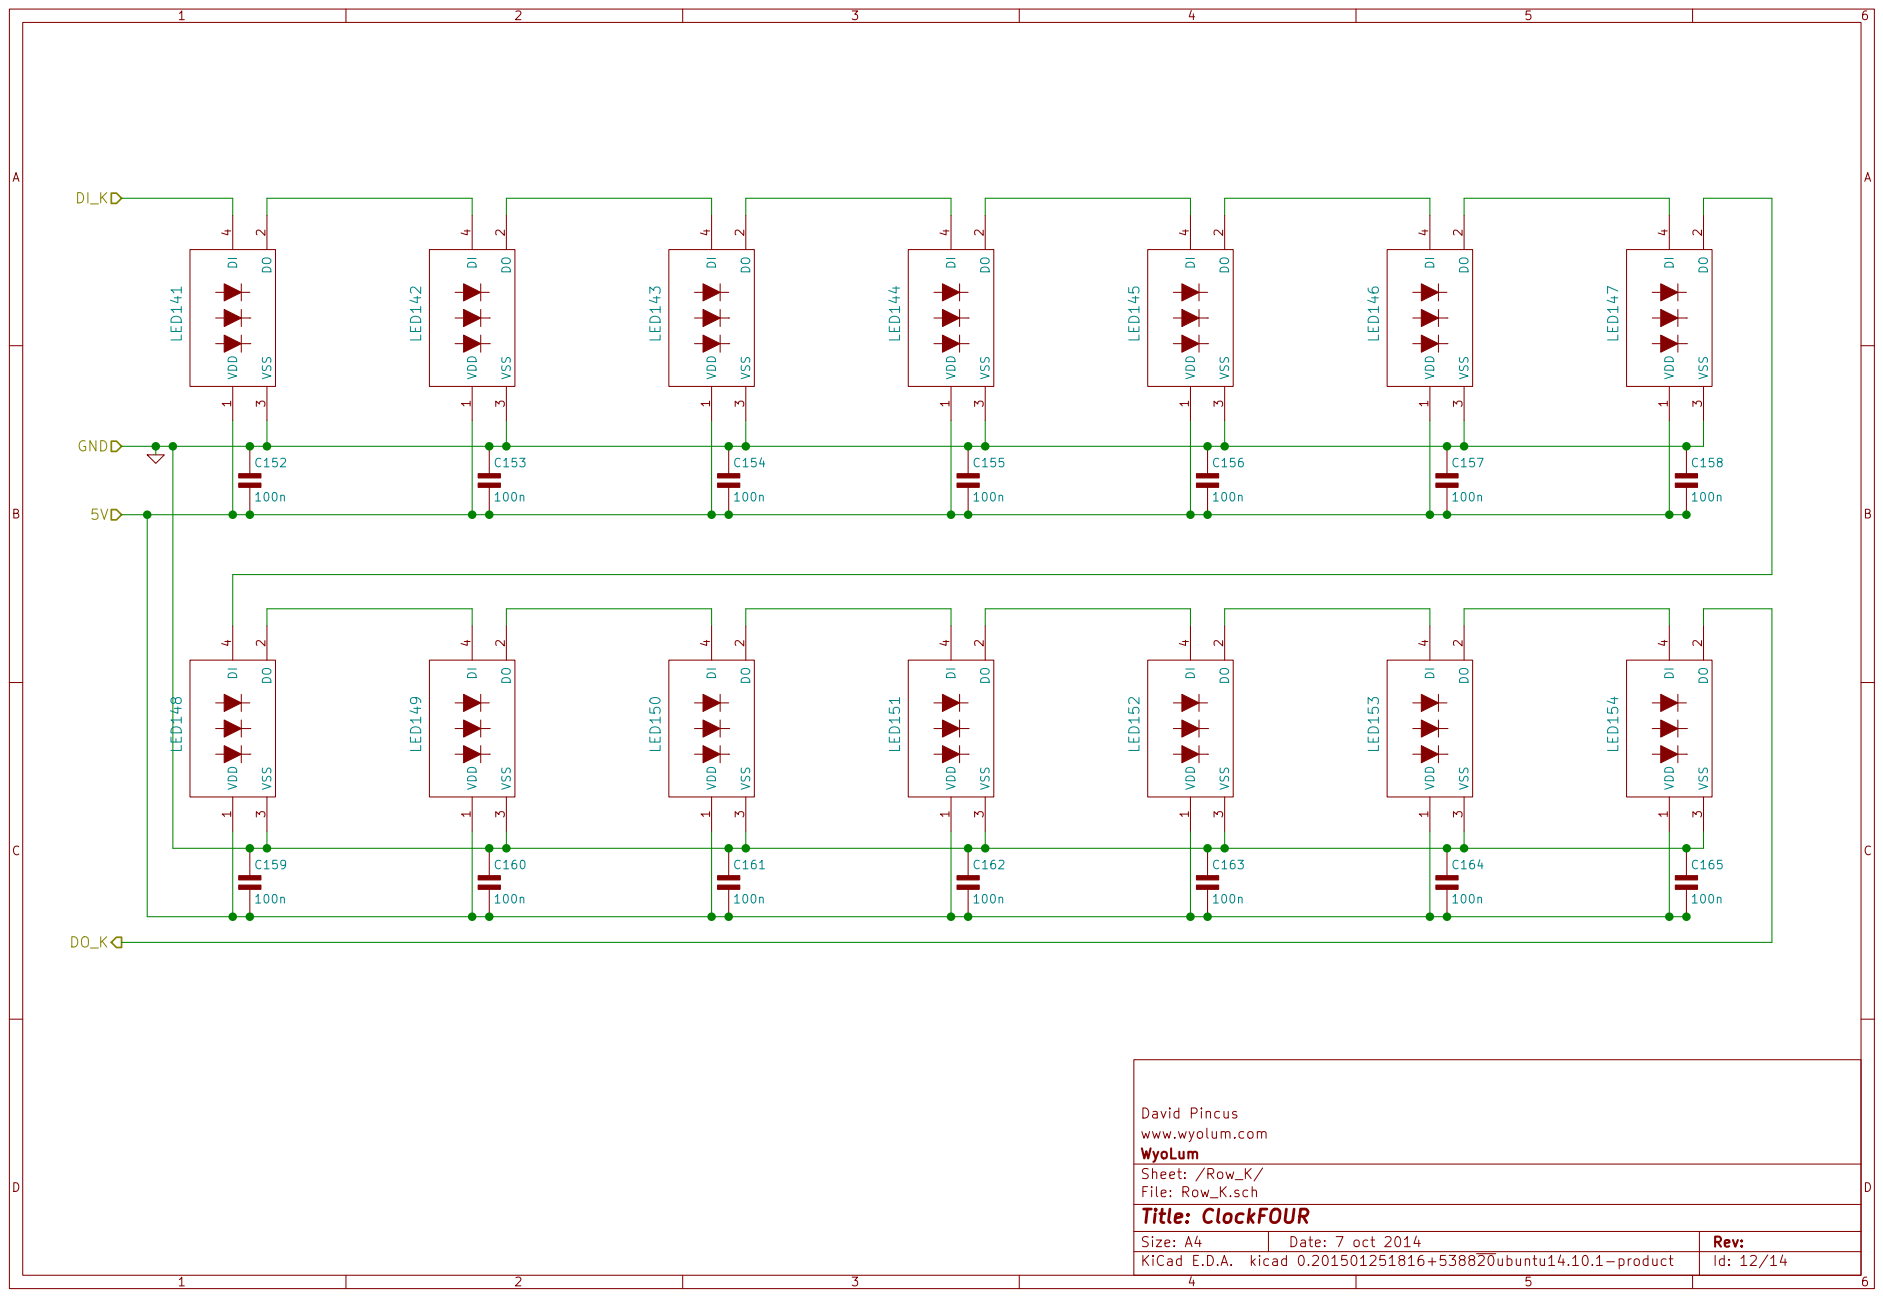
[picture p55: page 12]

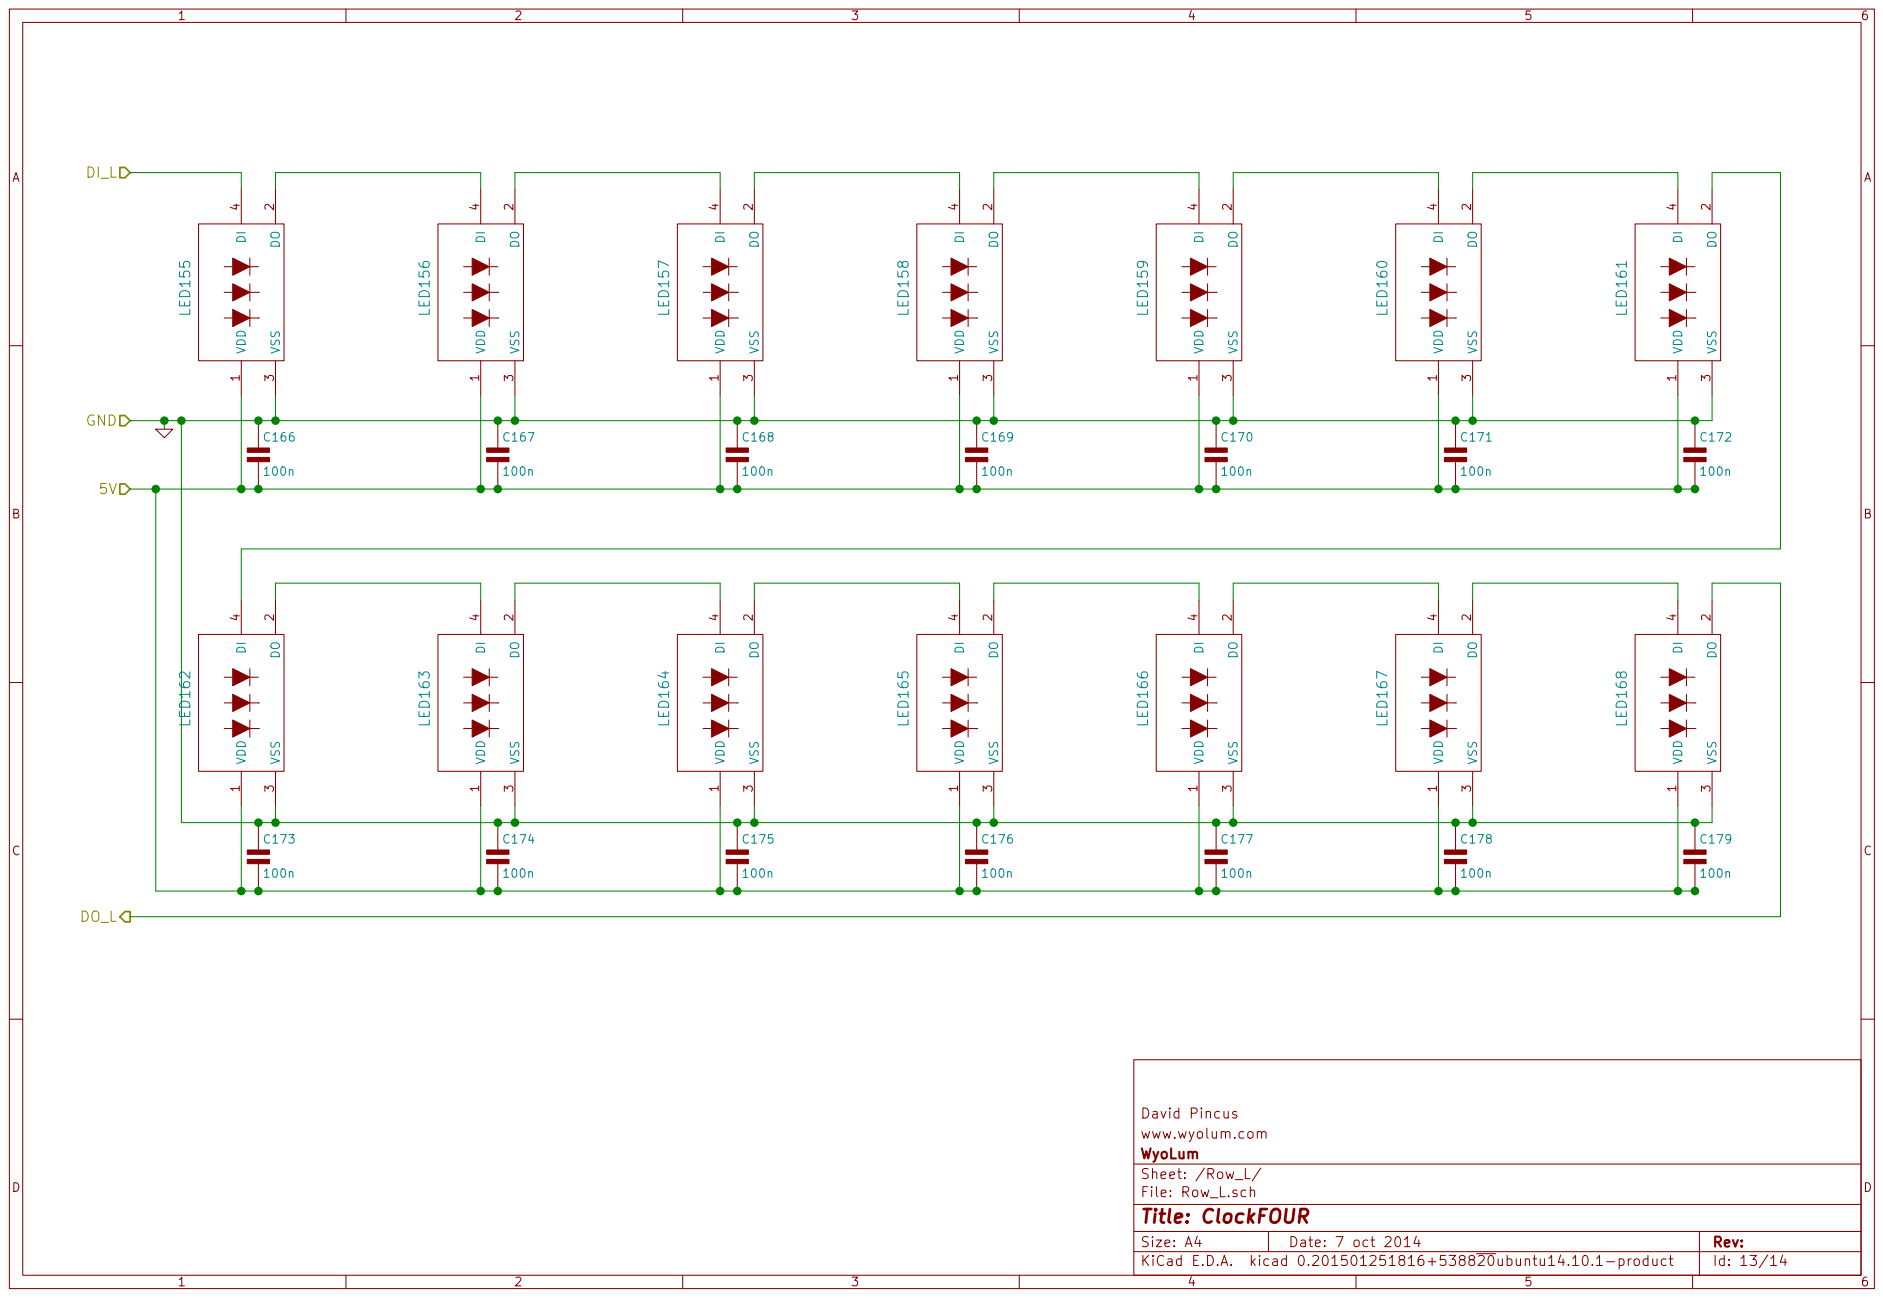
[picture p56: page 13]

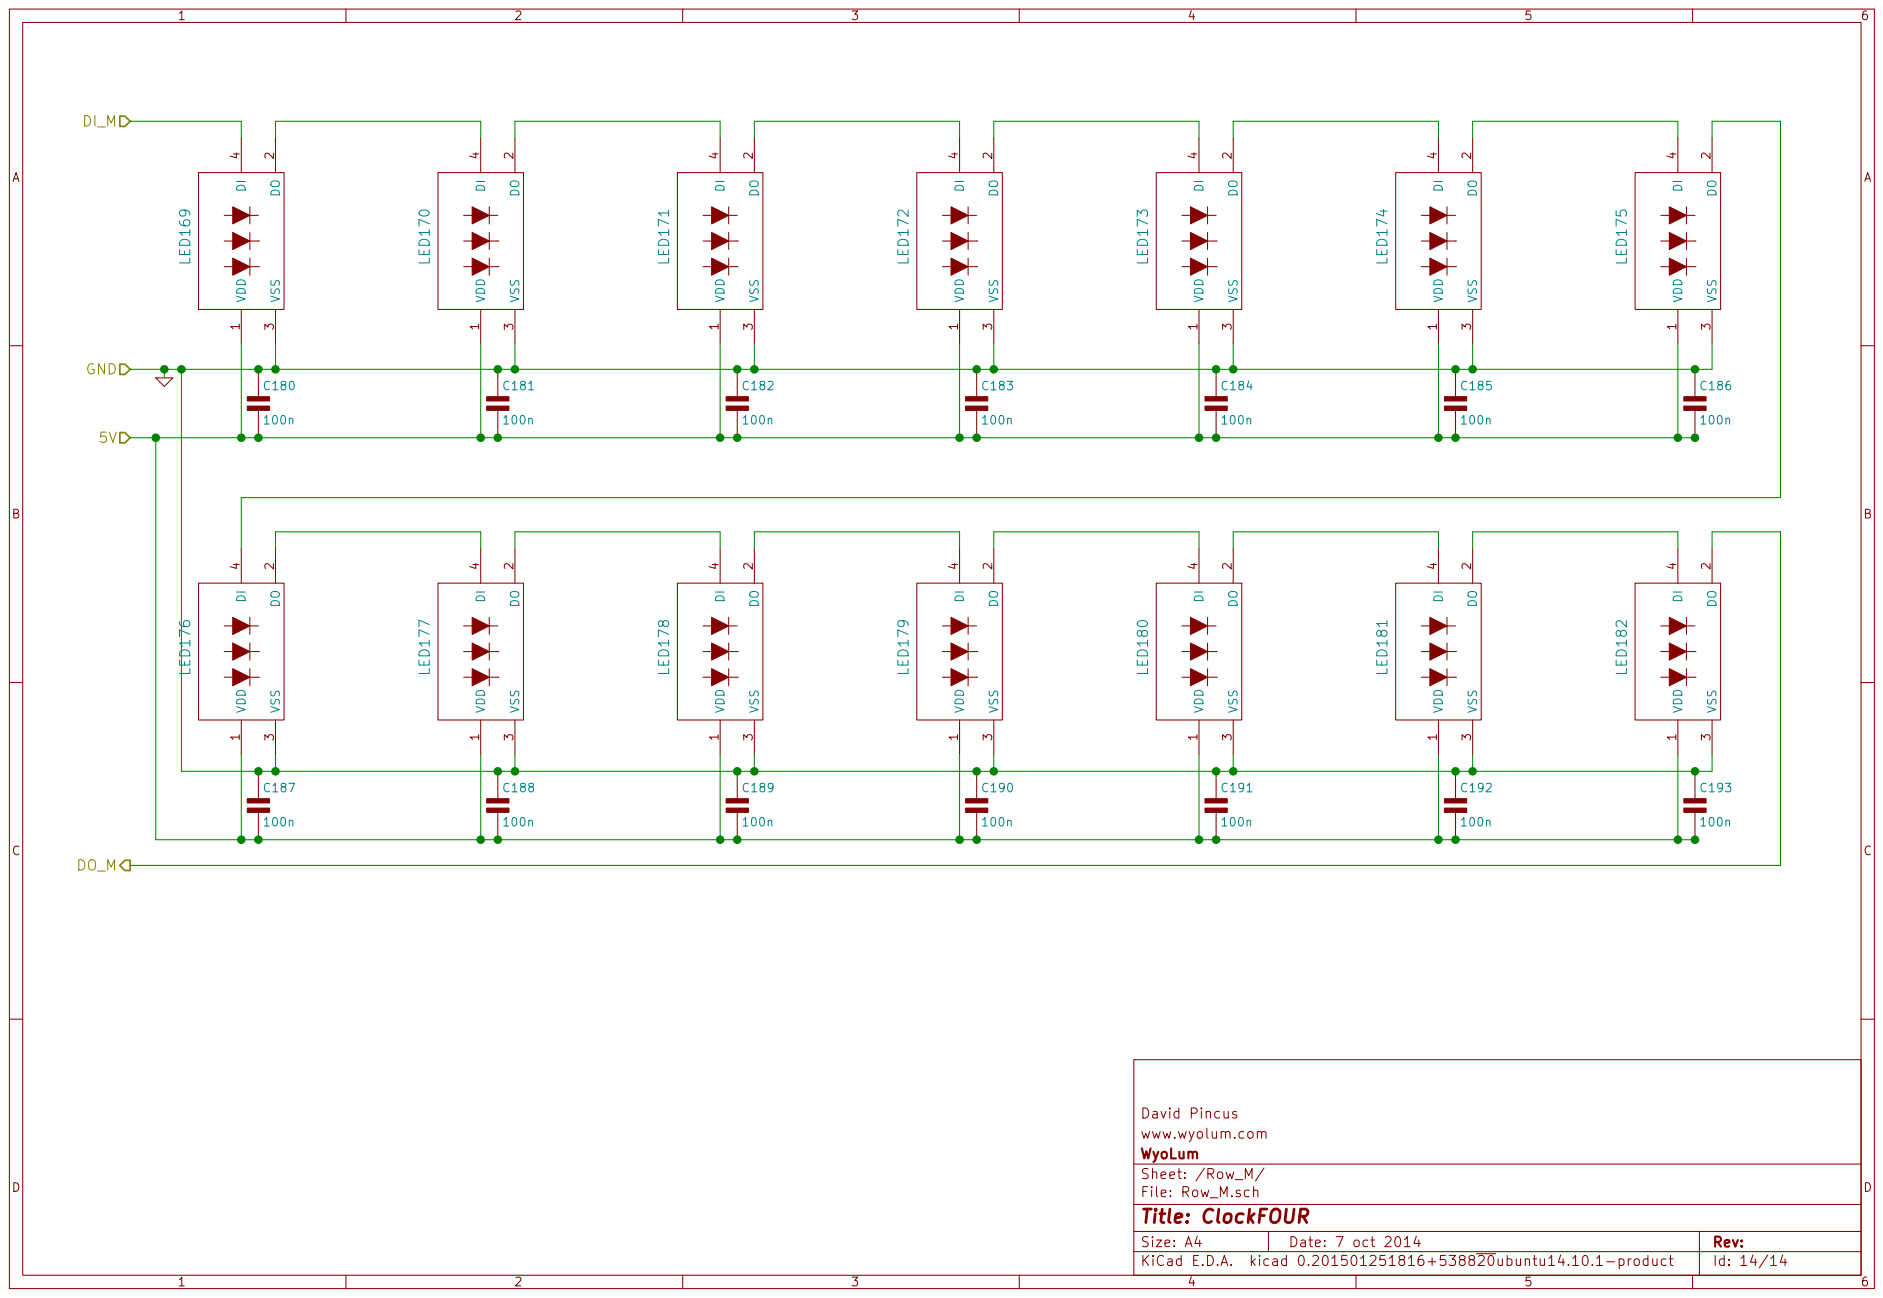
[picture p57: page 14]
