wyolum/ClockFOUR/ClockFOUR Firmware Quick Reference.pdf

# ClockTiM Firmware 1.0 Quick Reference

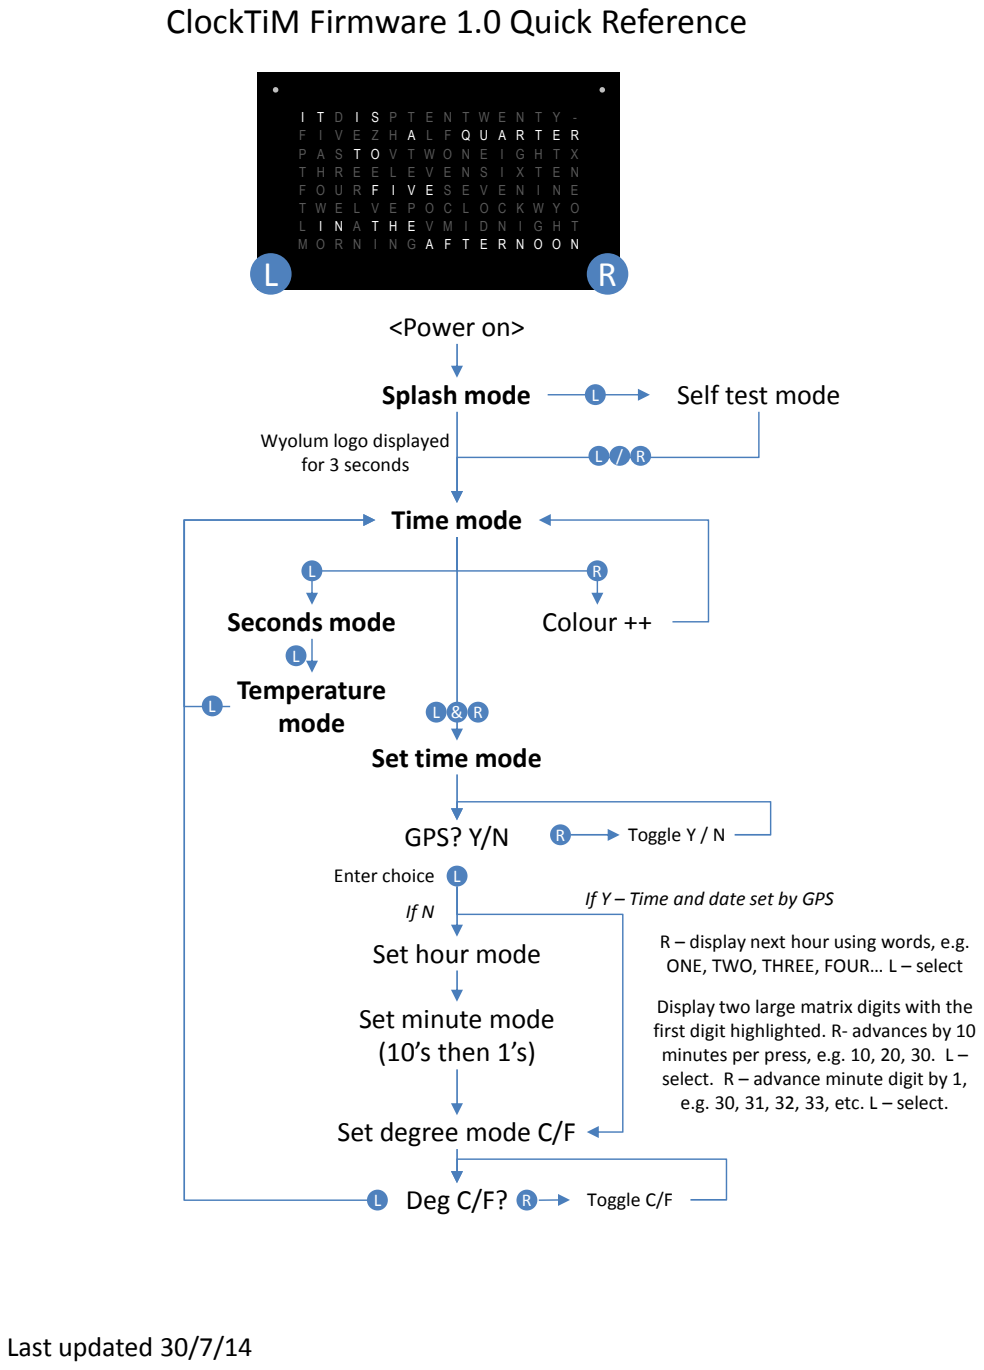
[picture p58: page 1]
<Power on>; Splash mode; Time mode; Seconds mode; Temperature mode; Colour ++; Deg C/F?; Toggle C/F; GPS? Y/N; Toggle Y / N; Enter choice; Last updated 30/7/14

Self test mode

Wyolum logo displayed
for 3 seconds

Set time mode

If Y – Time and date set by GPS

Set hour mode

R – display next hour using words, e.g.
ONE, TWO, THREE, FOUR… L – select

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

Set minute mode
(10’s then 1’s)

Set degree mode C/F
