wyolum/ClockFOUR/KiCad_bak/pdf/ClockFOUR-B_SilkS.pdf

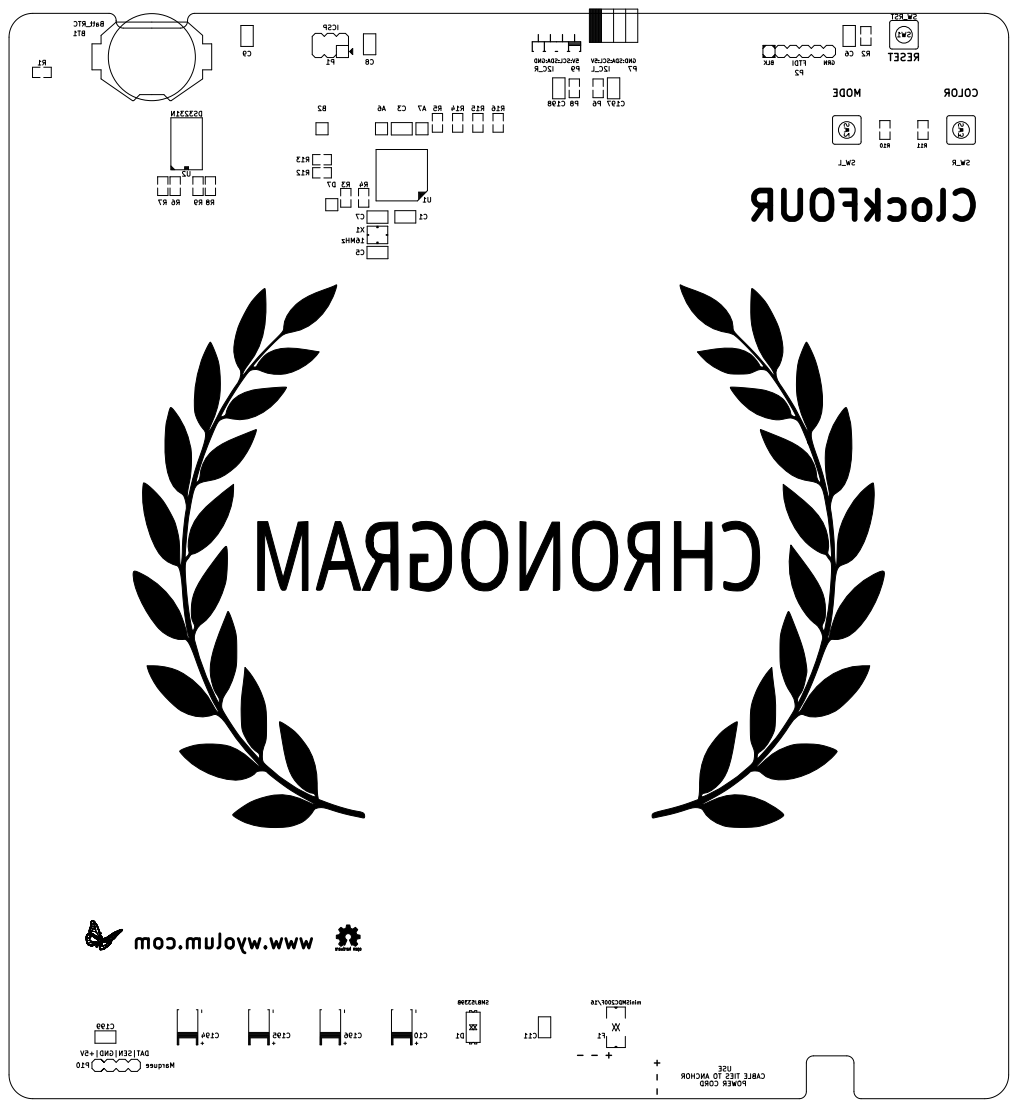
[picture p59: page 1]

5V:SCL:SDA:GND GND:SDA:SCL:5V ClockFOUR

USE CABLE TIES TO ANCHOR
