wyolum/ClockFOUR/KiCad_bak/pdf/ClockFOUR.pdf

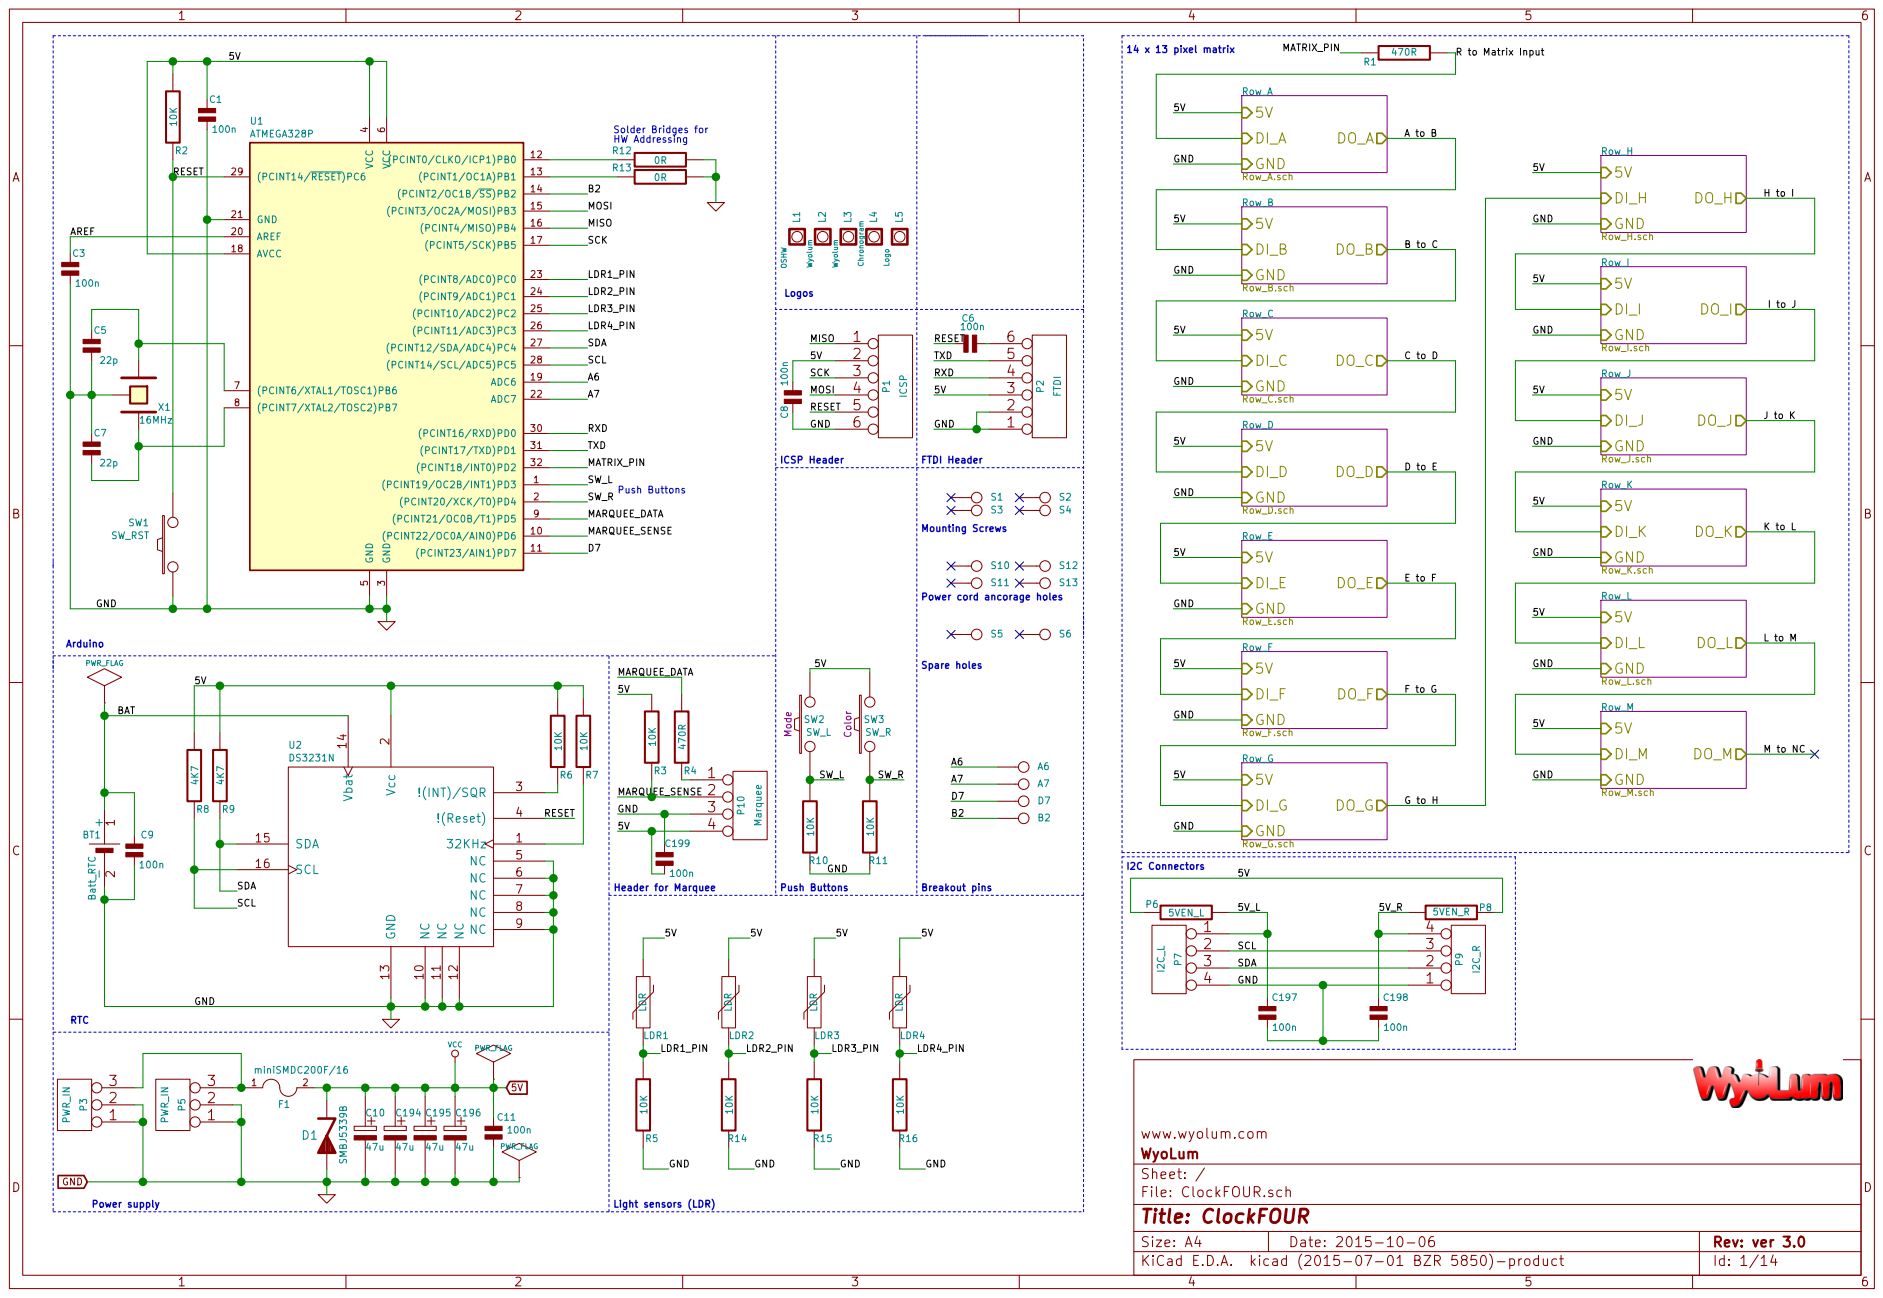
[picture p60: page 1]

100n RESET

5V Row_C.sch DI_C GND | DO_C

(PCINT6/XTAL1/TOSC1)PB6 7

5V GND

File: ClockFOUR.sch Sheet: / WyoLum

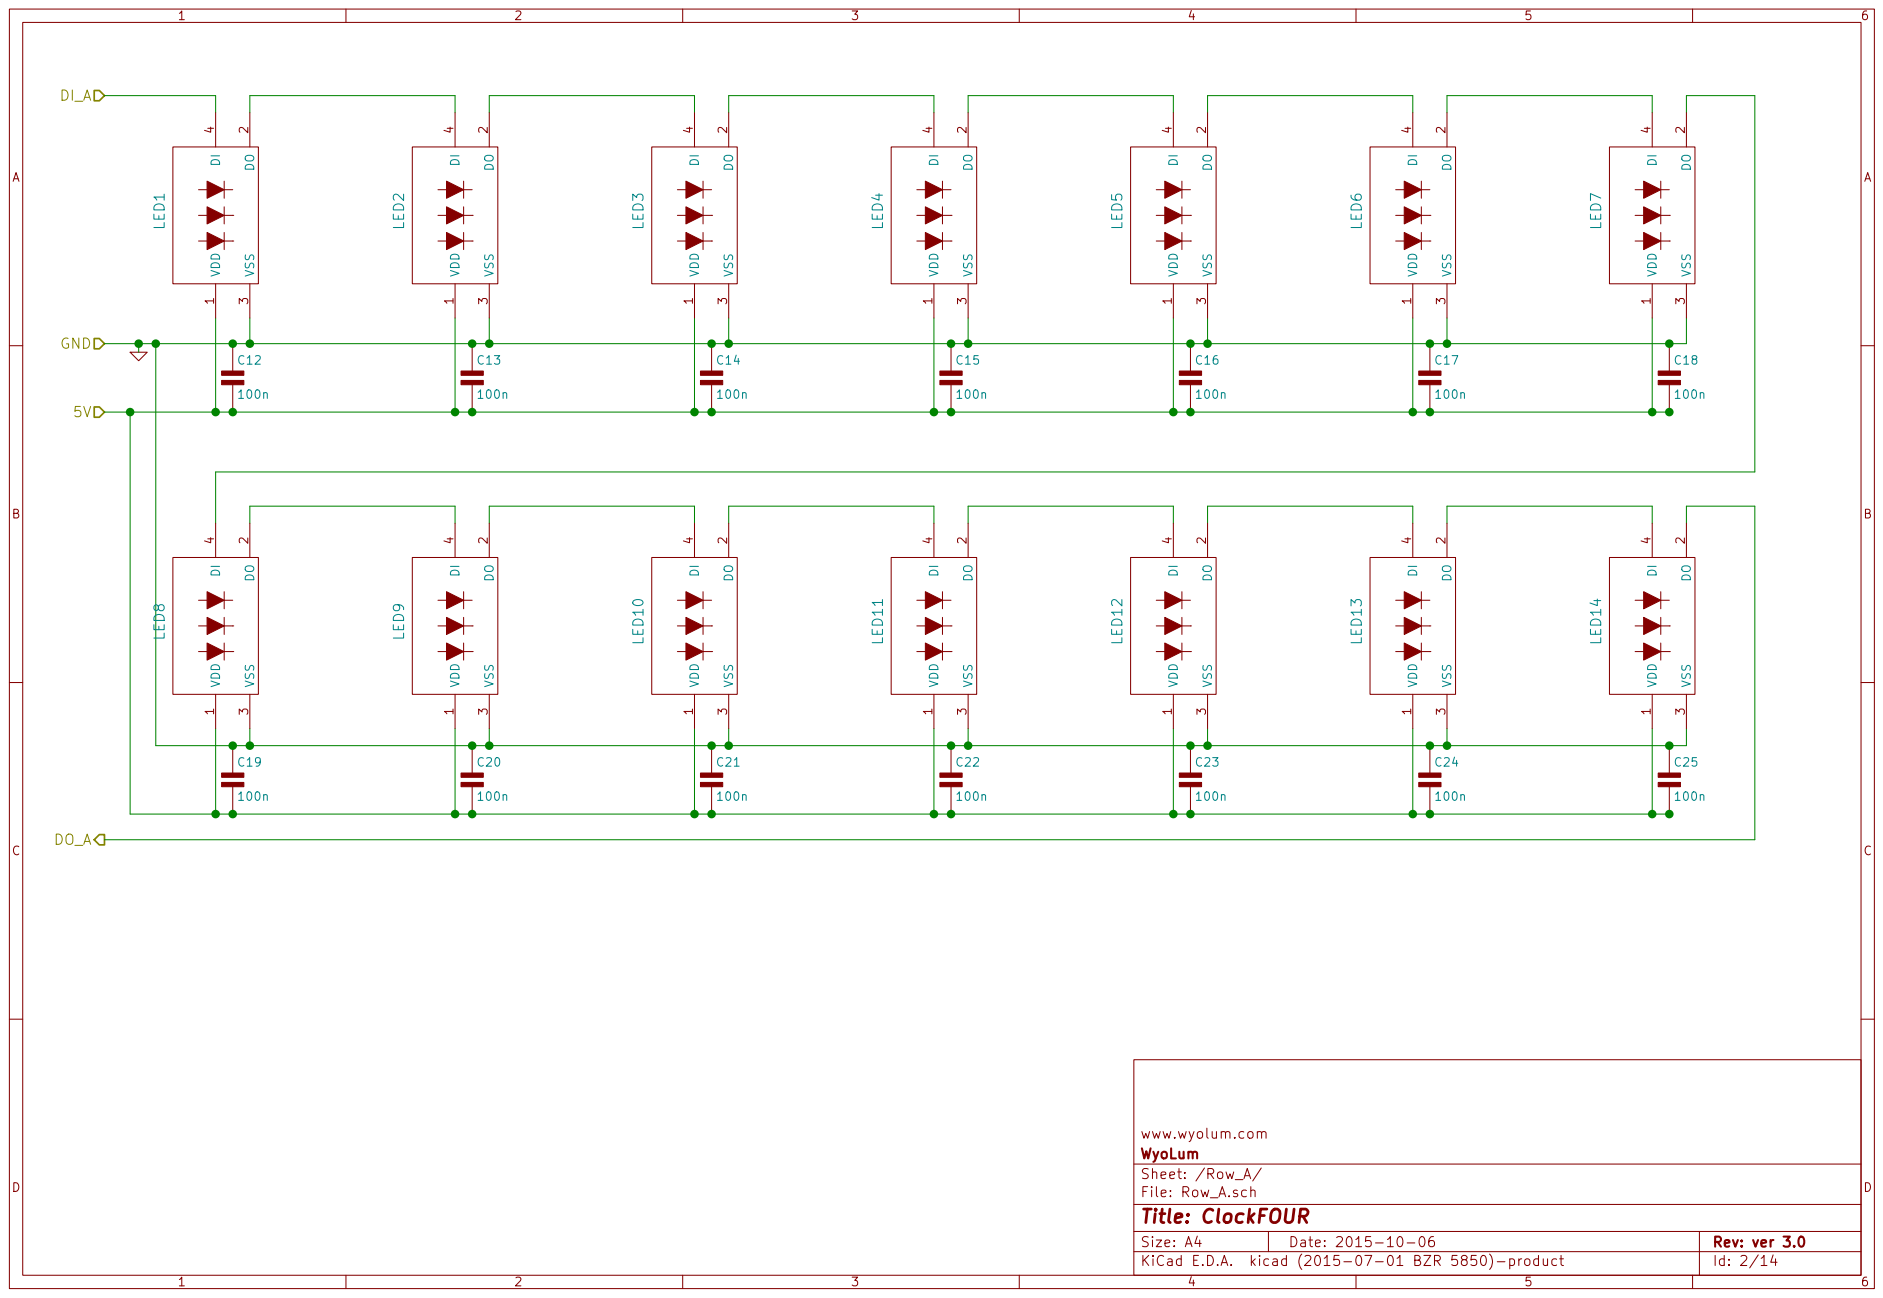
[picture p61: page 2]

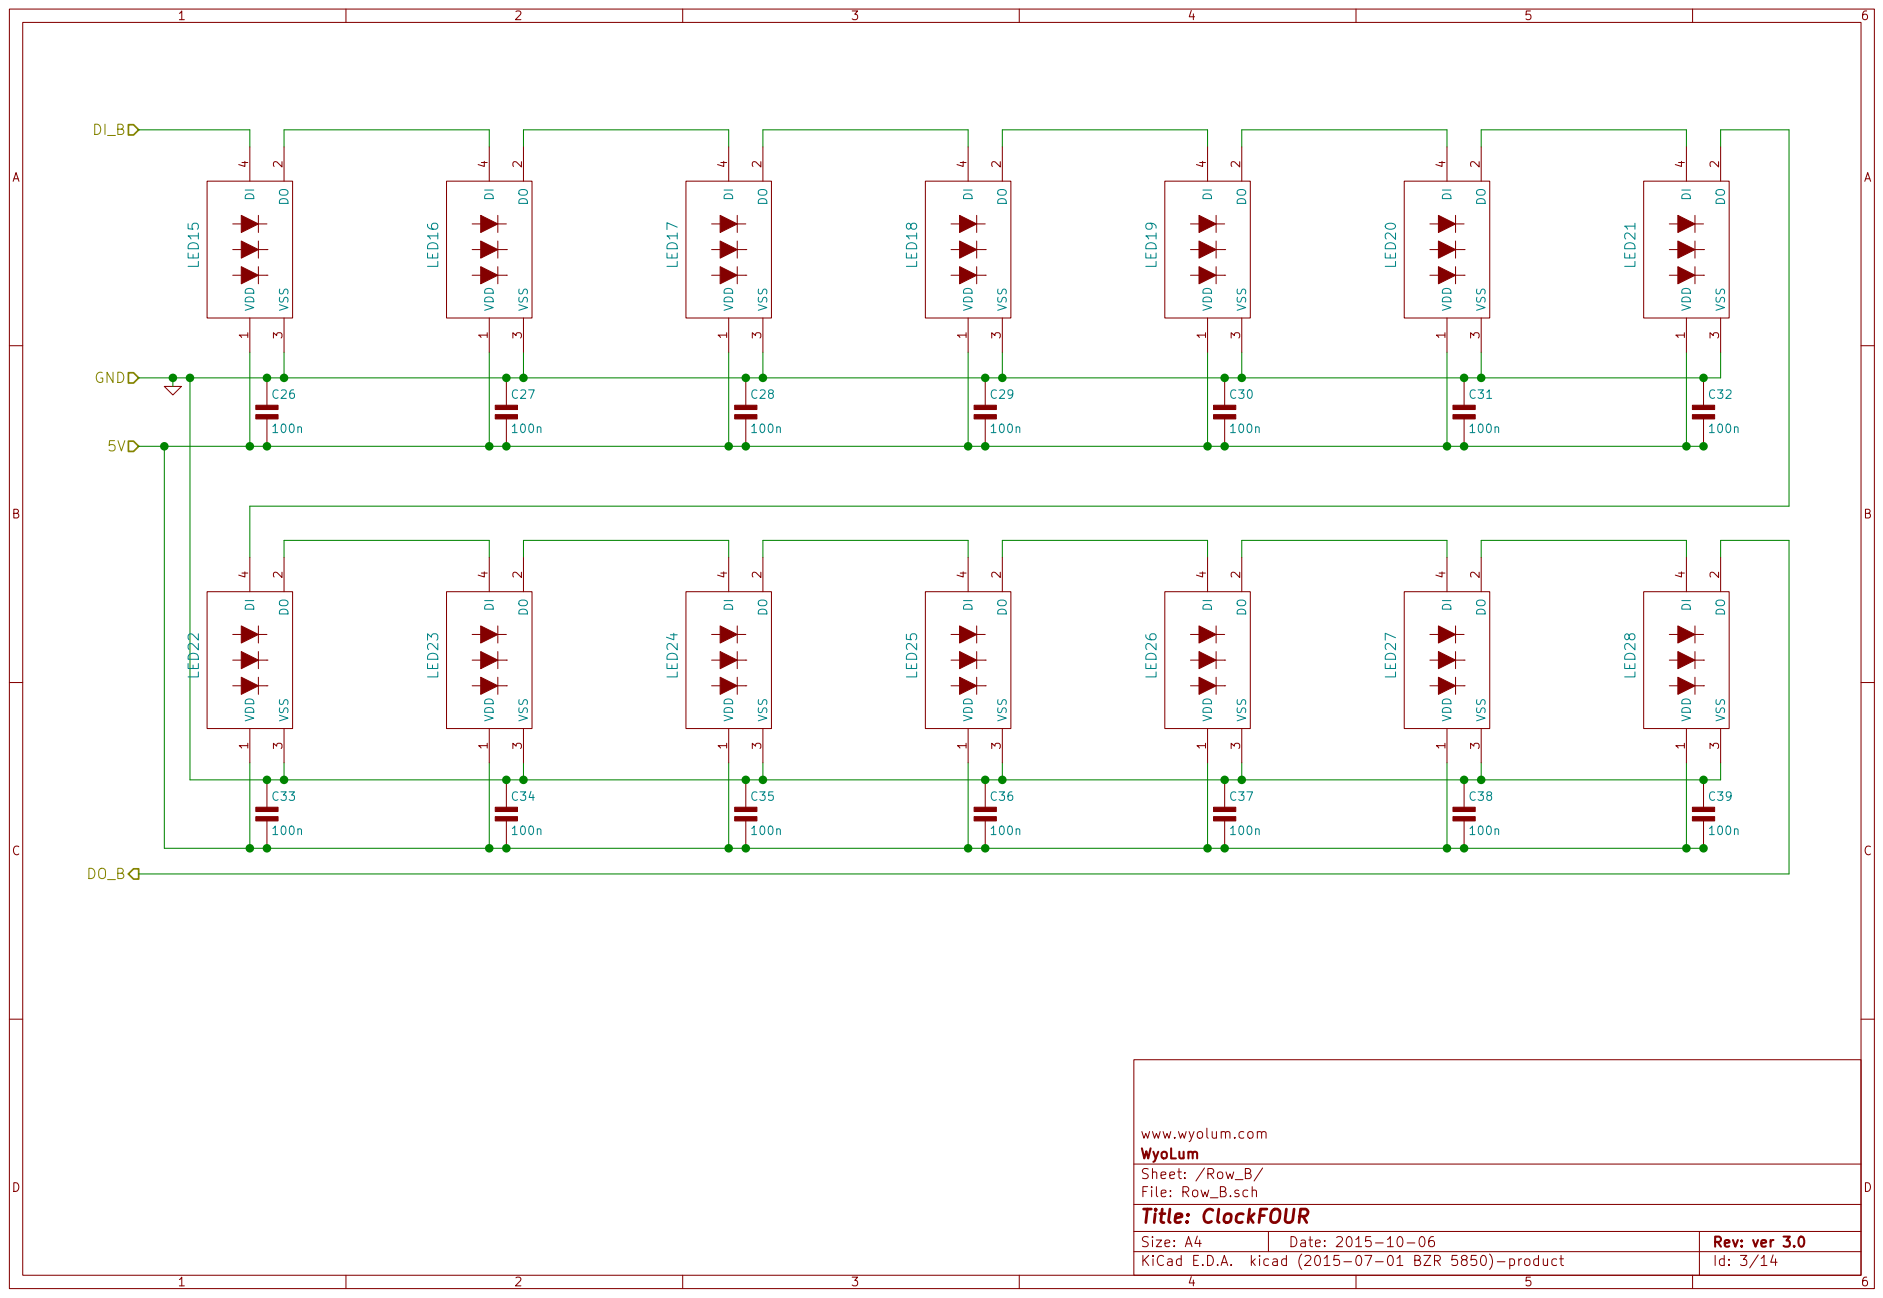
[picture p62: page 3]

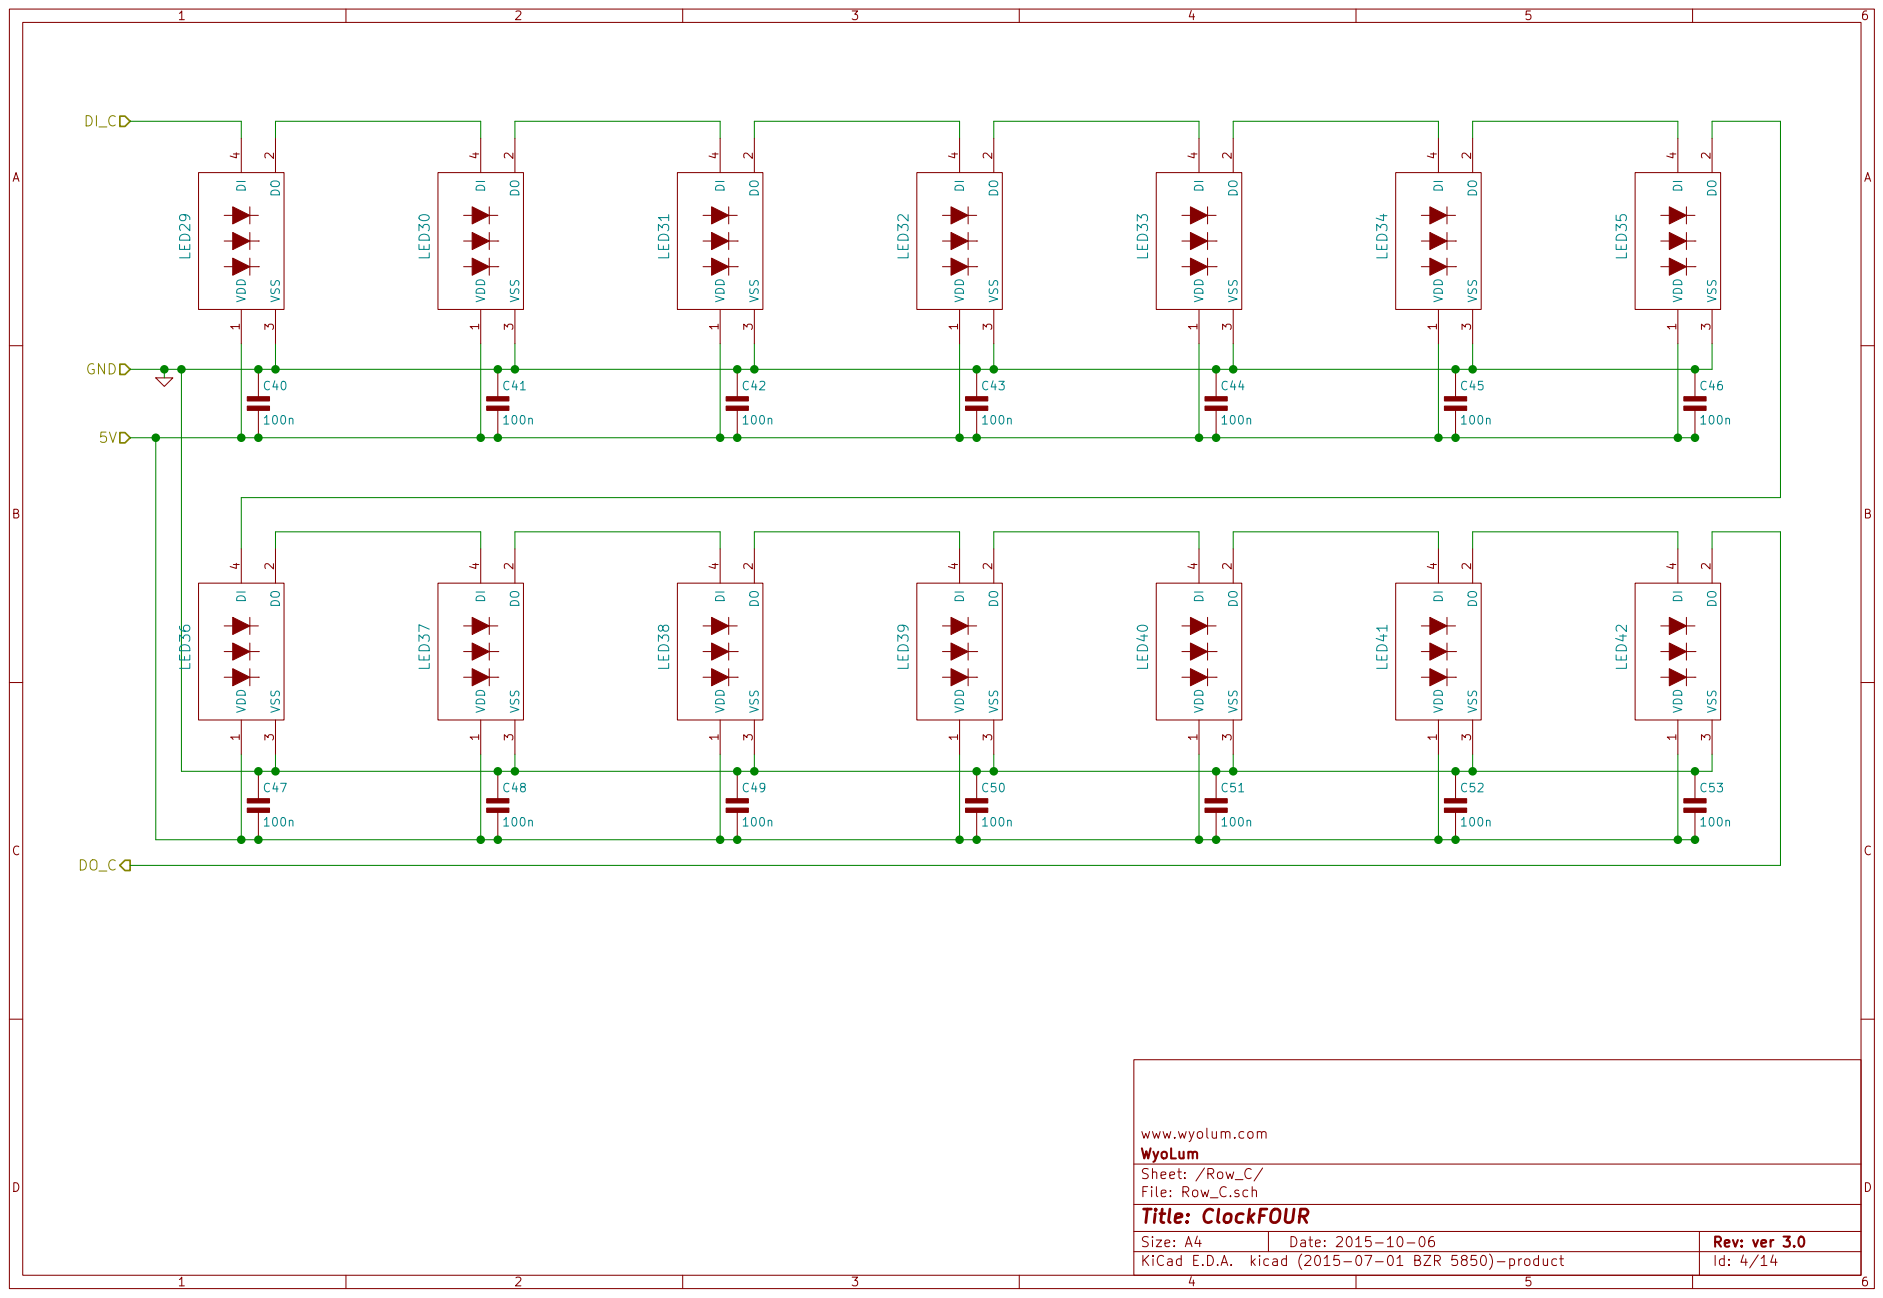
[picture p63: page 4]

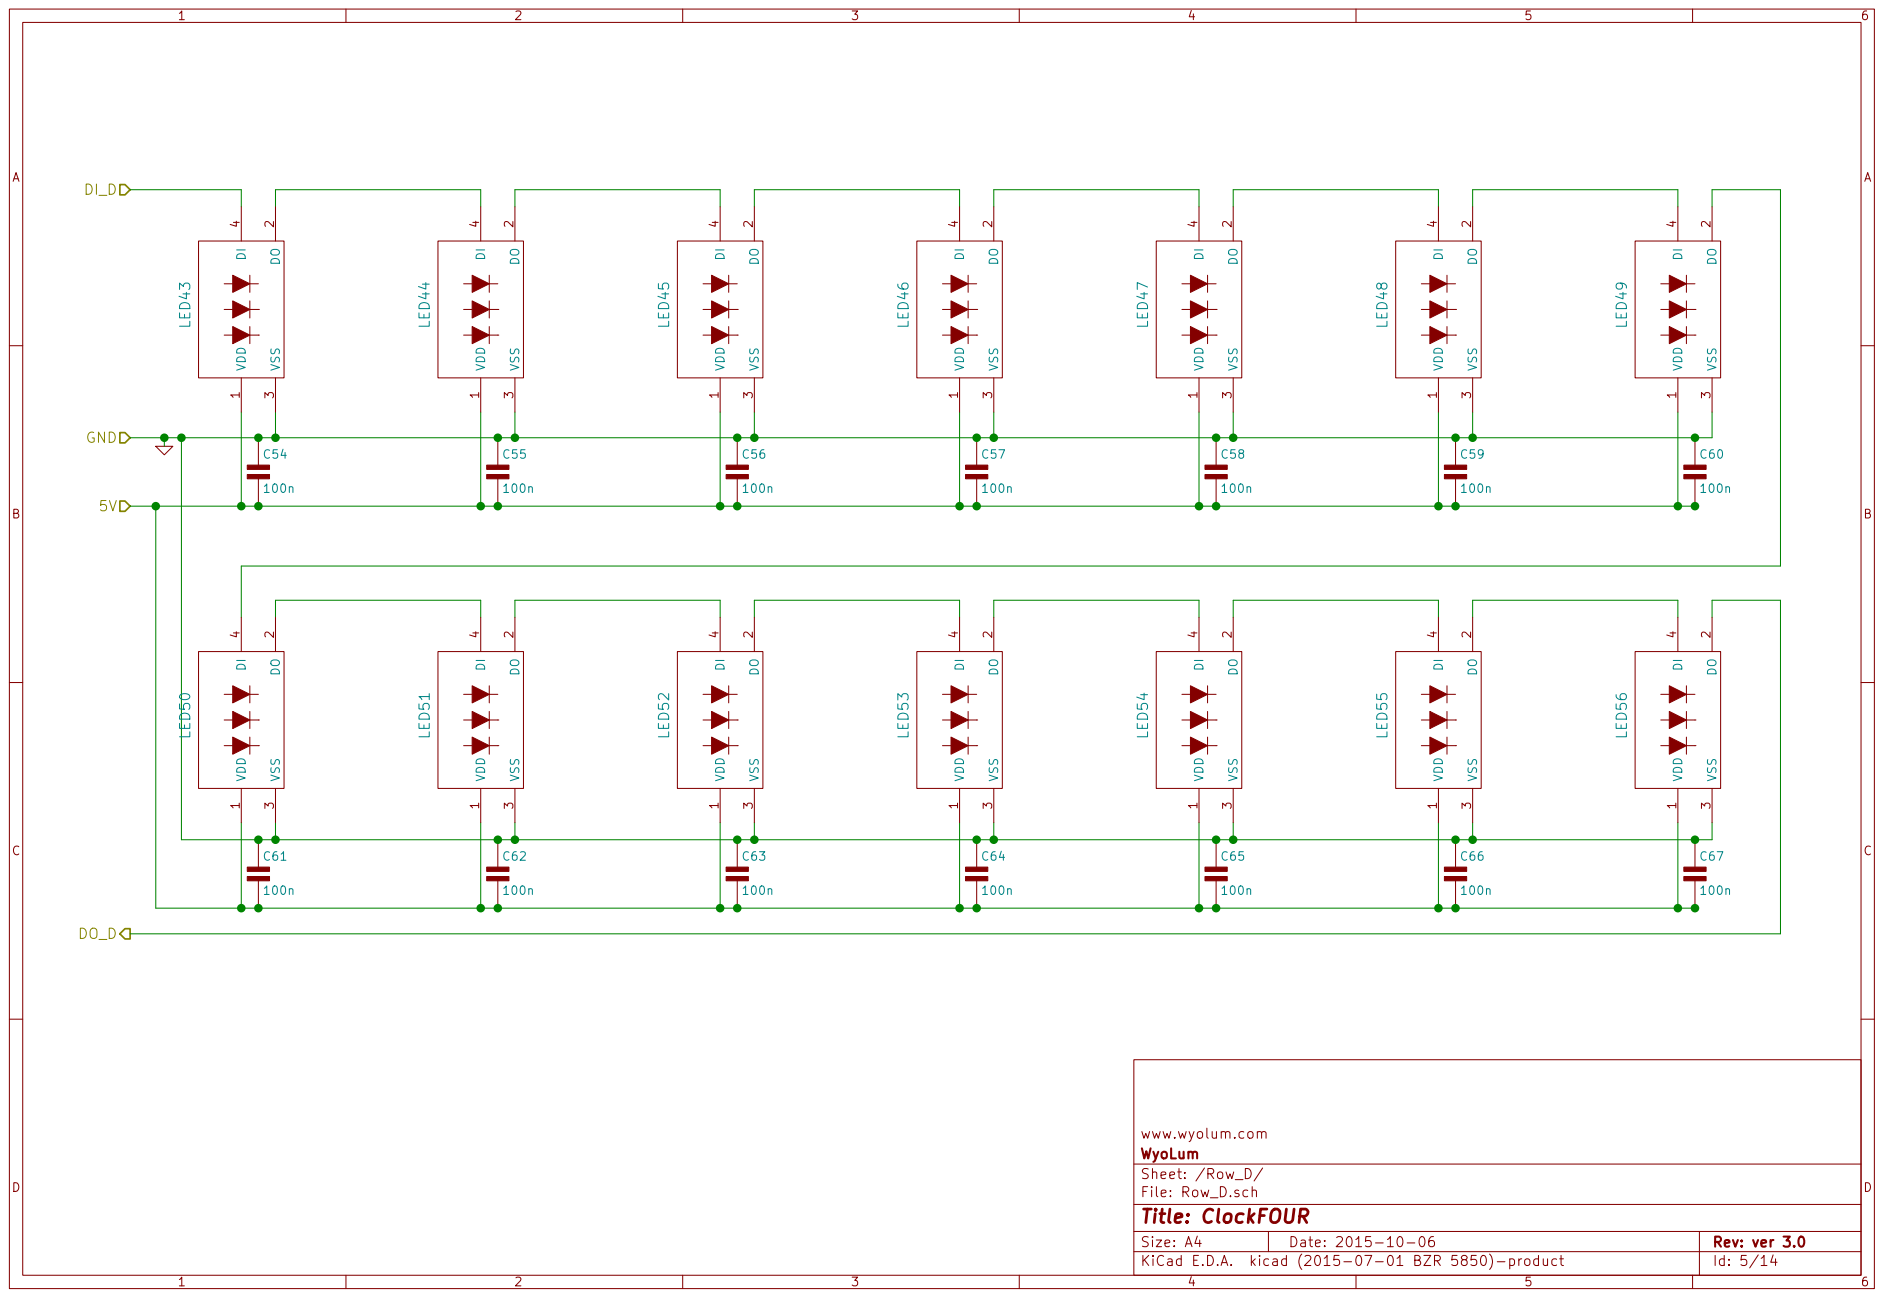
[picture p64: page 5]

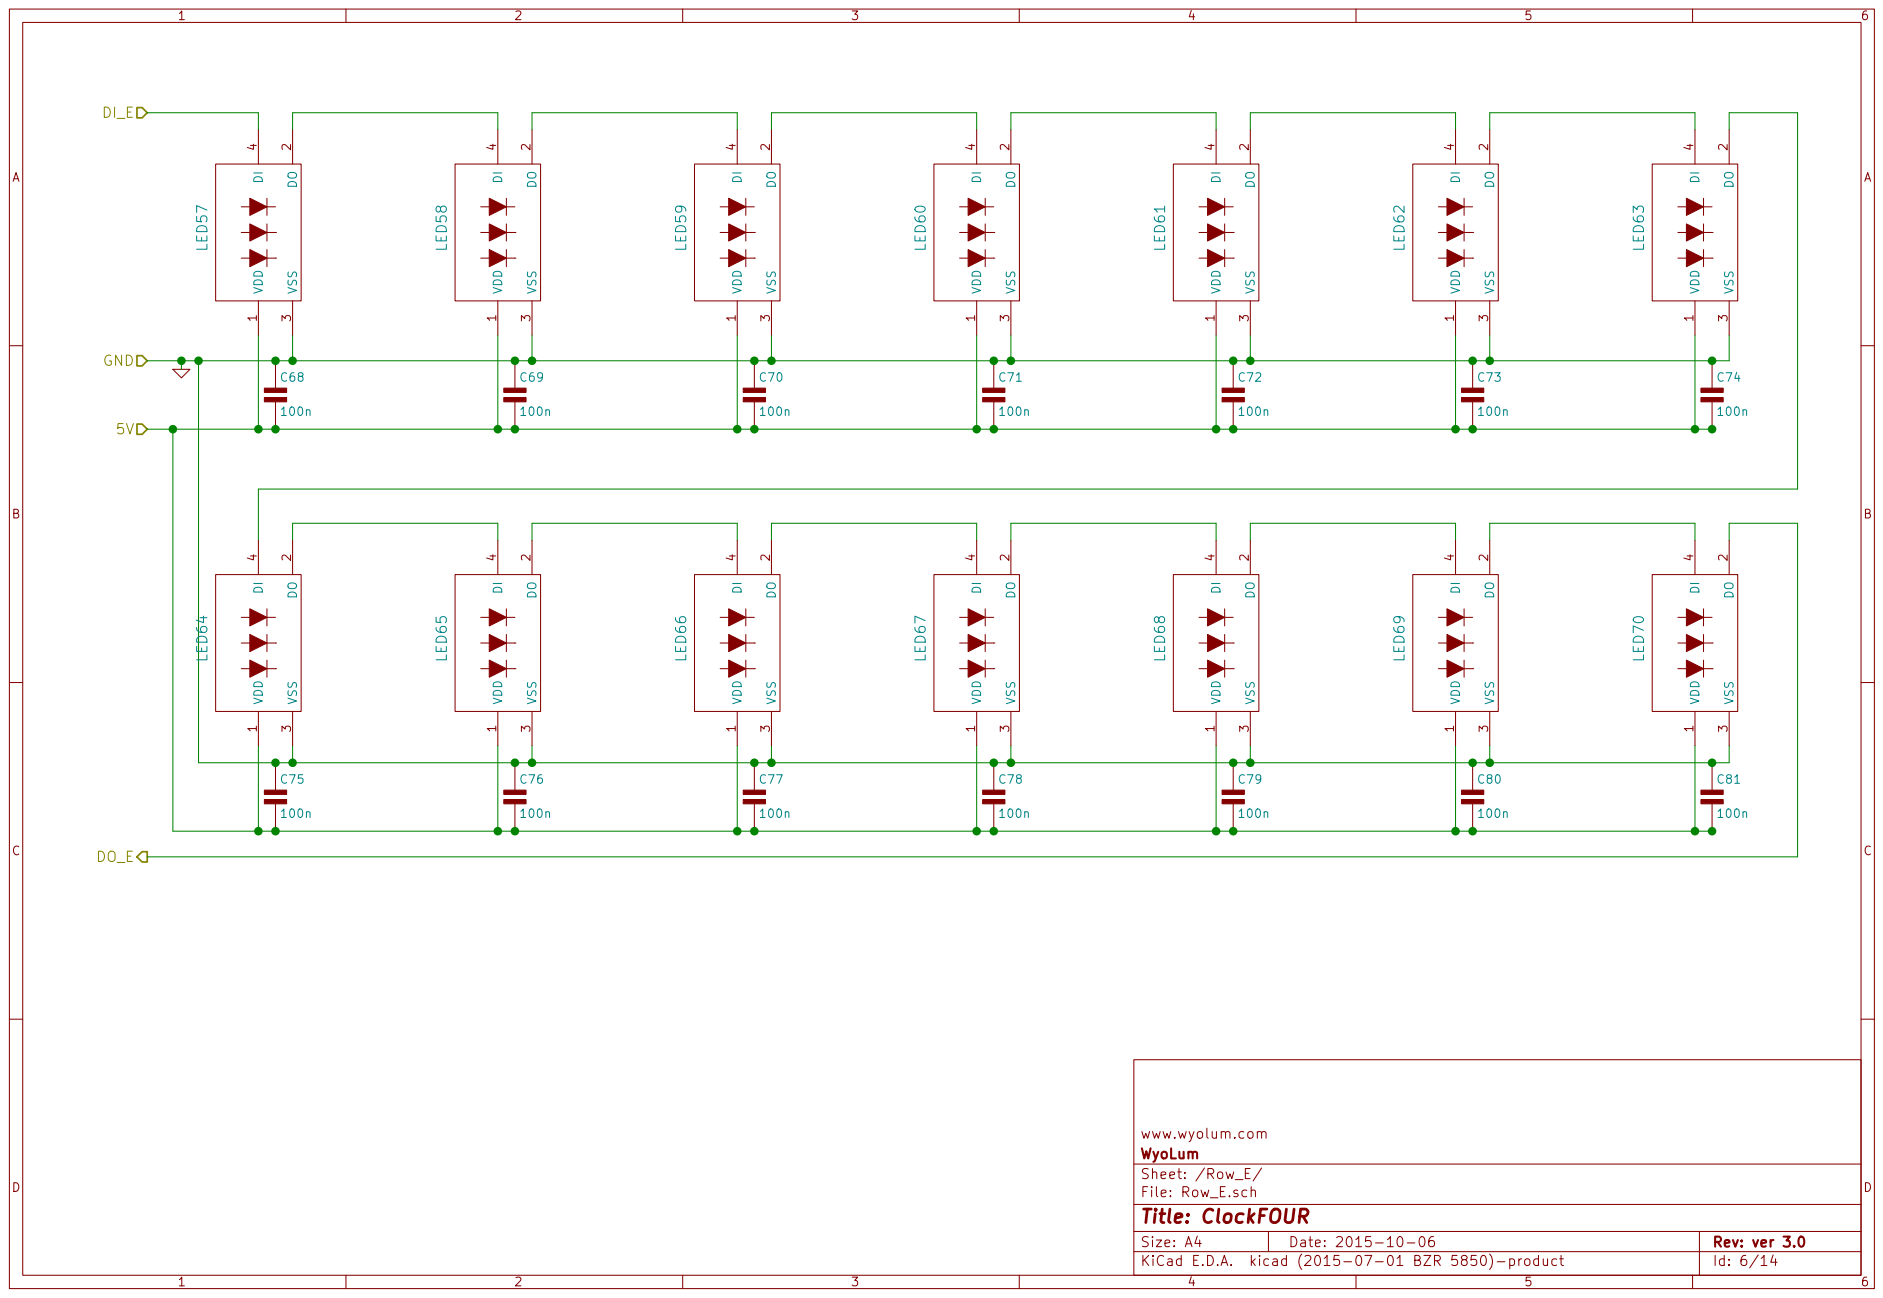
[picture p65: page 6]

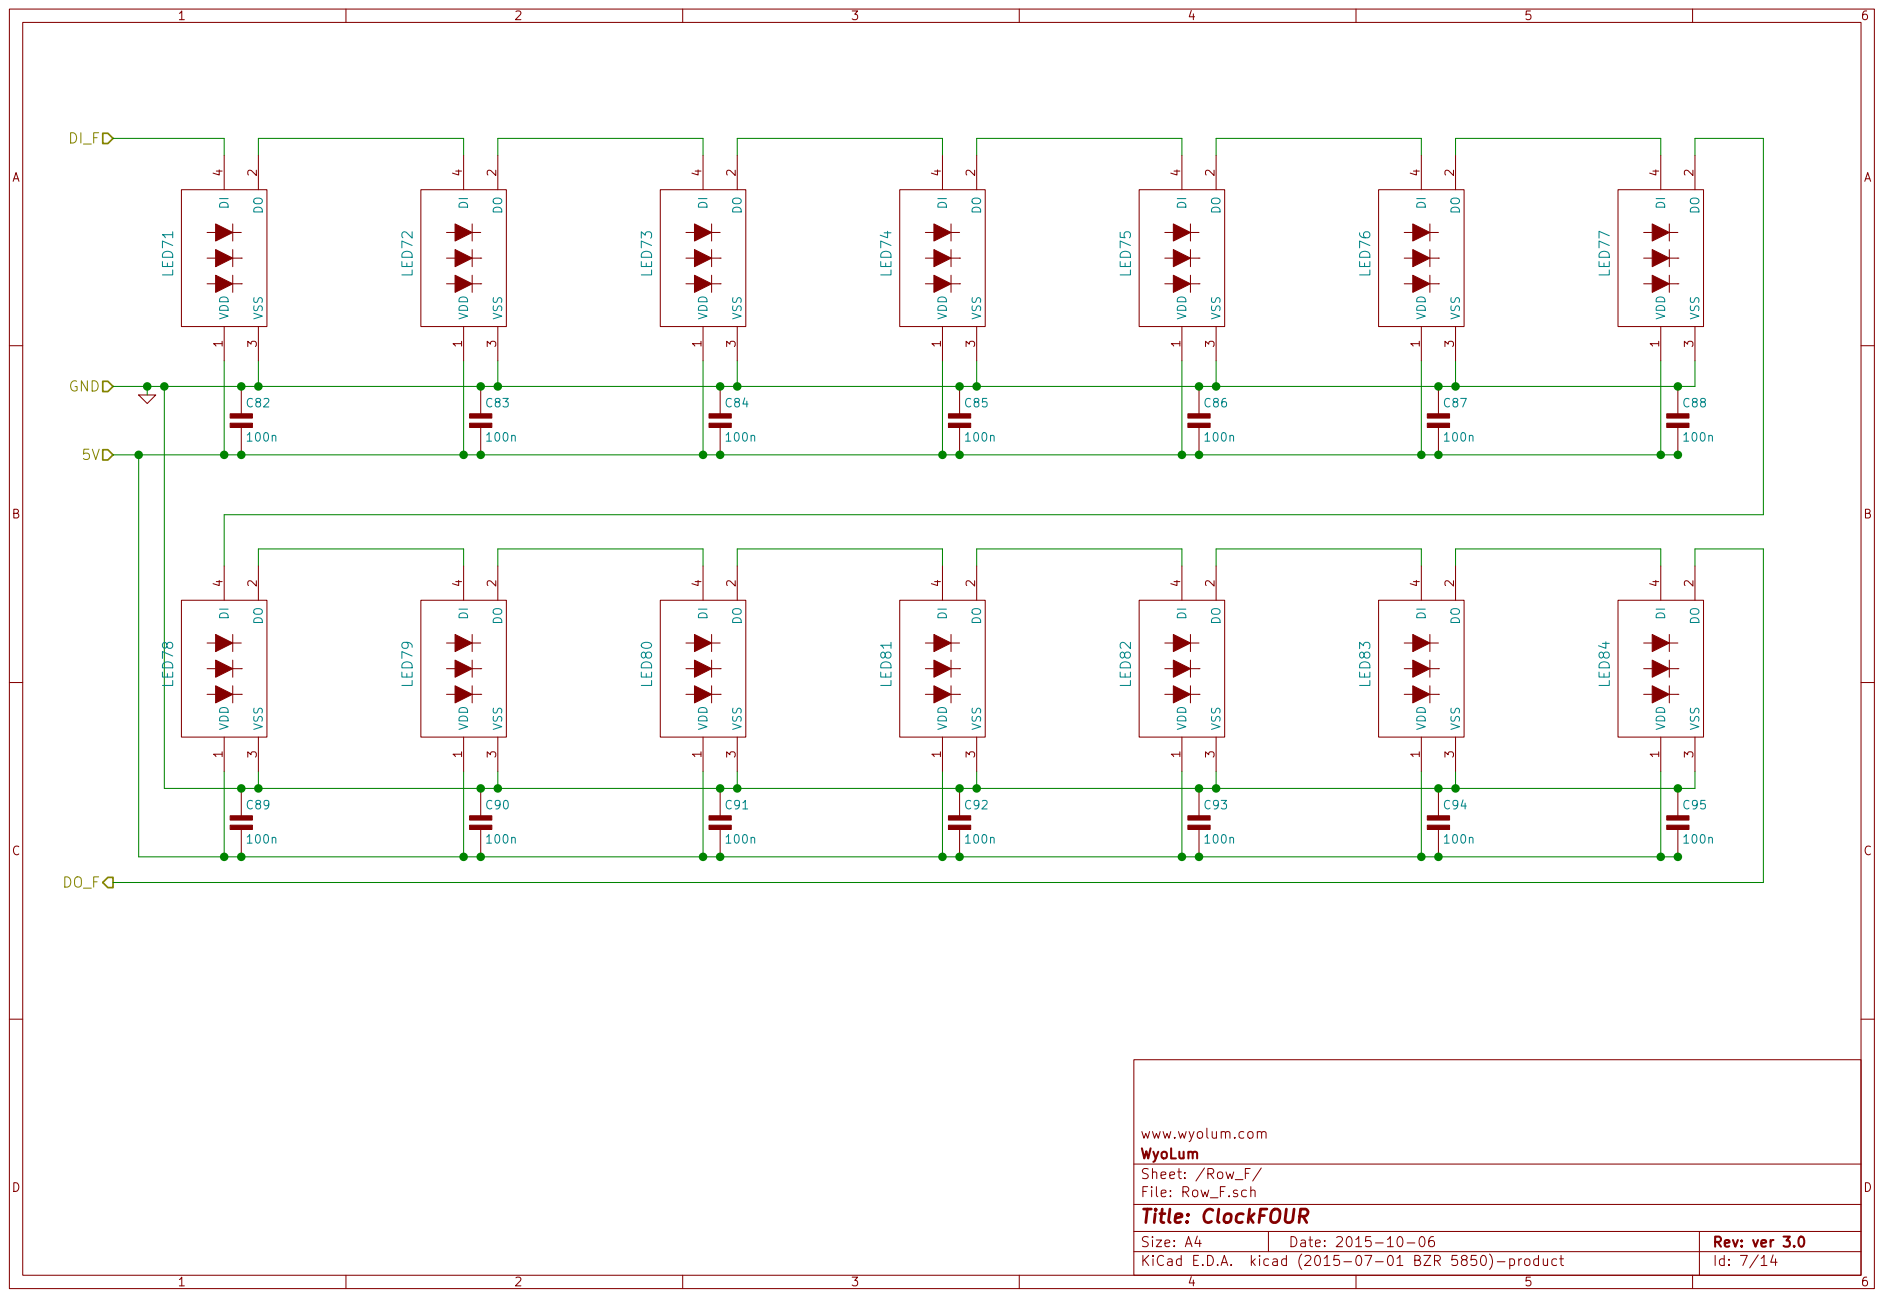
[picture p66: page 7]

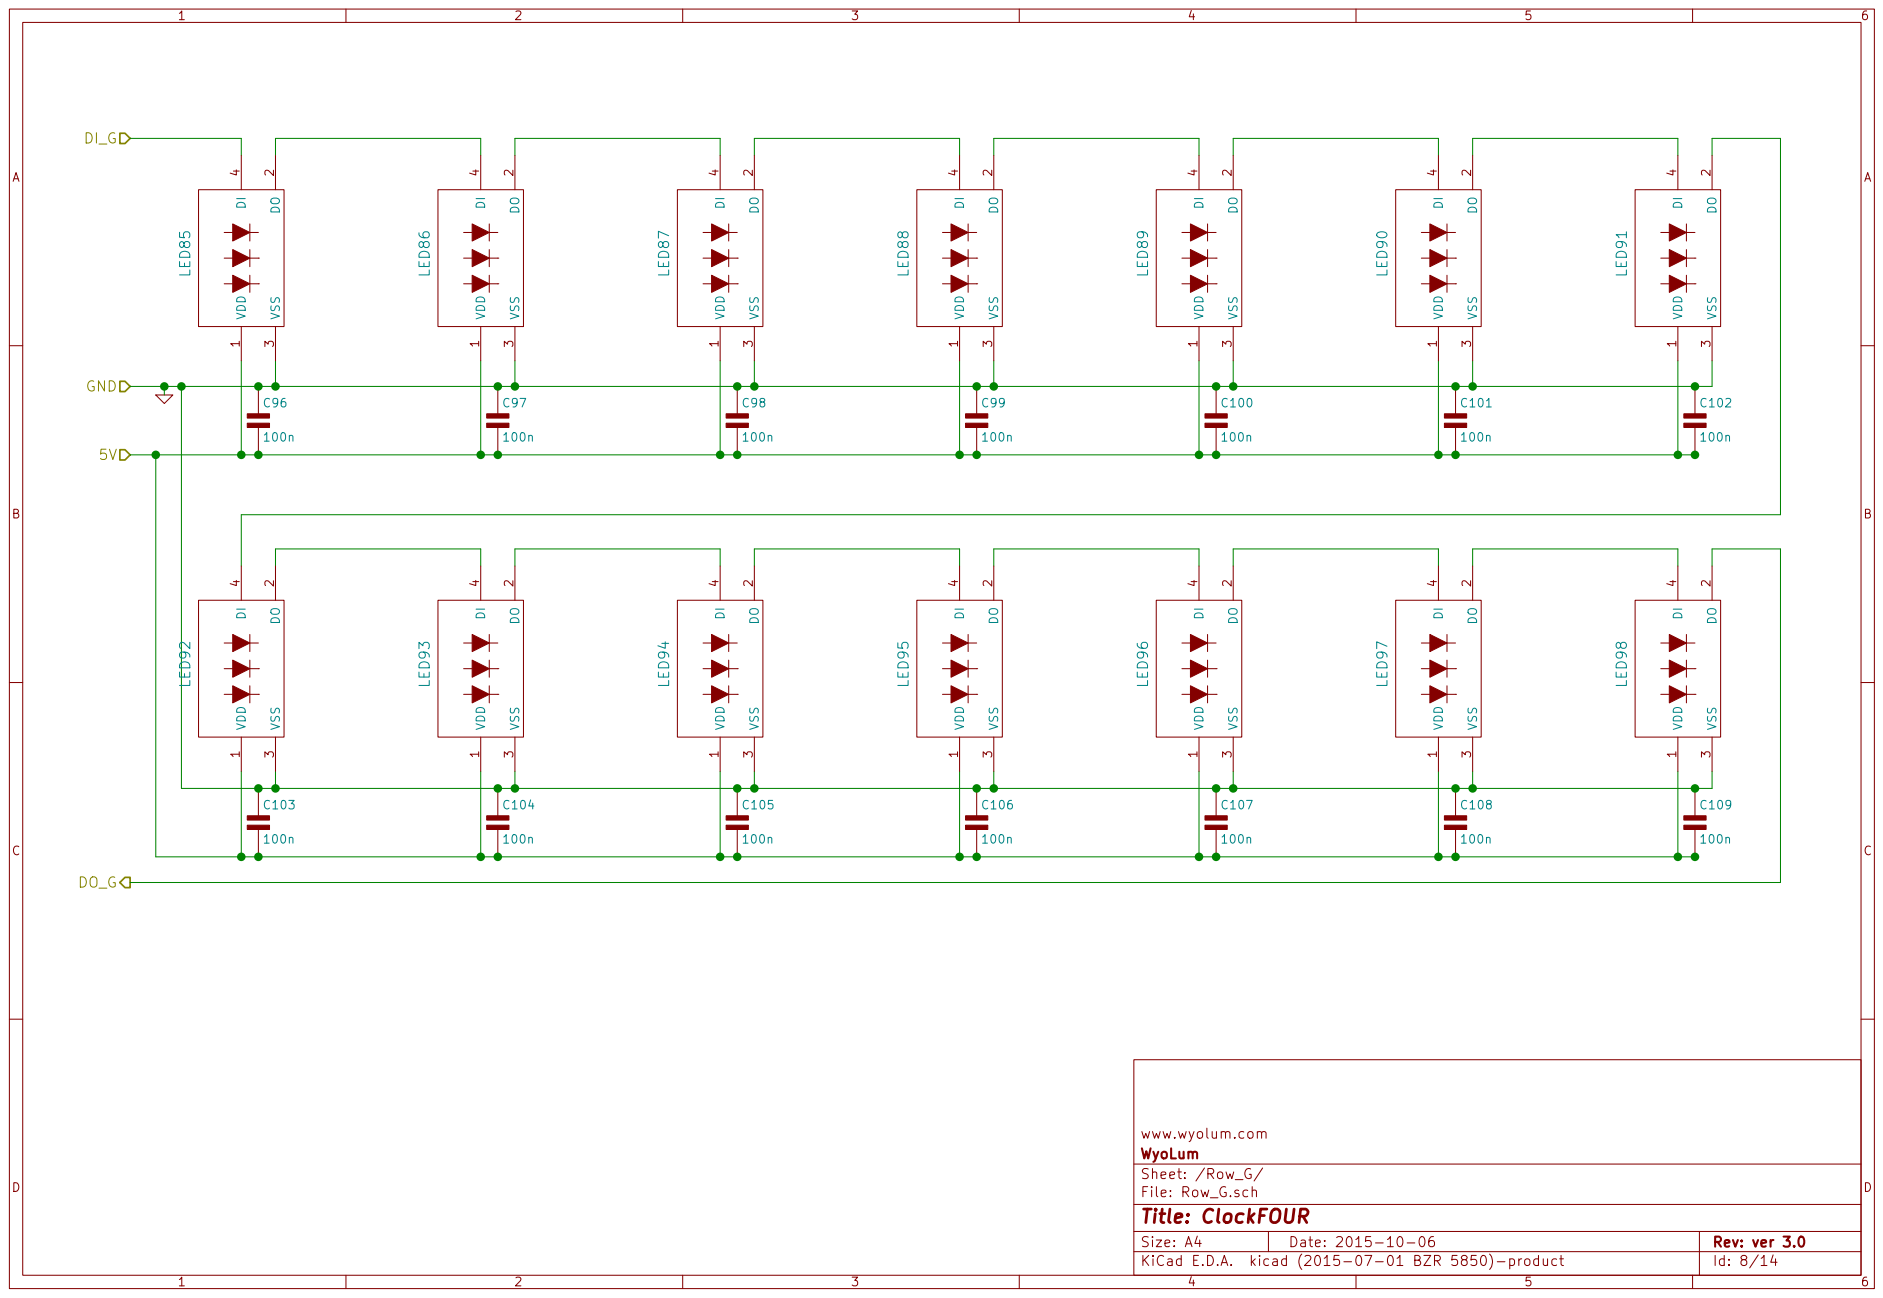
[picture p67: page 8]

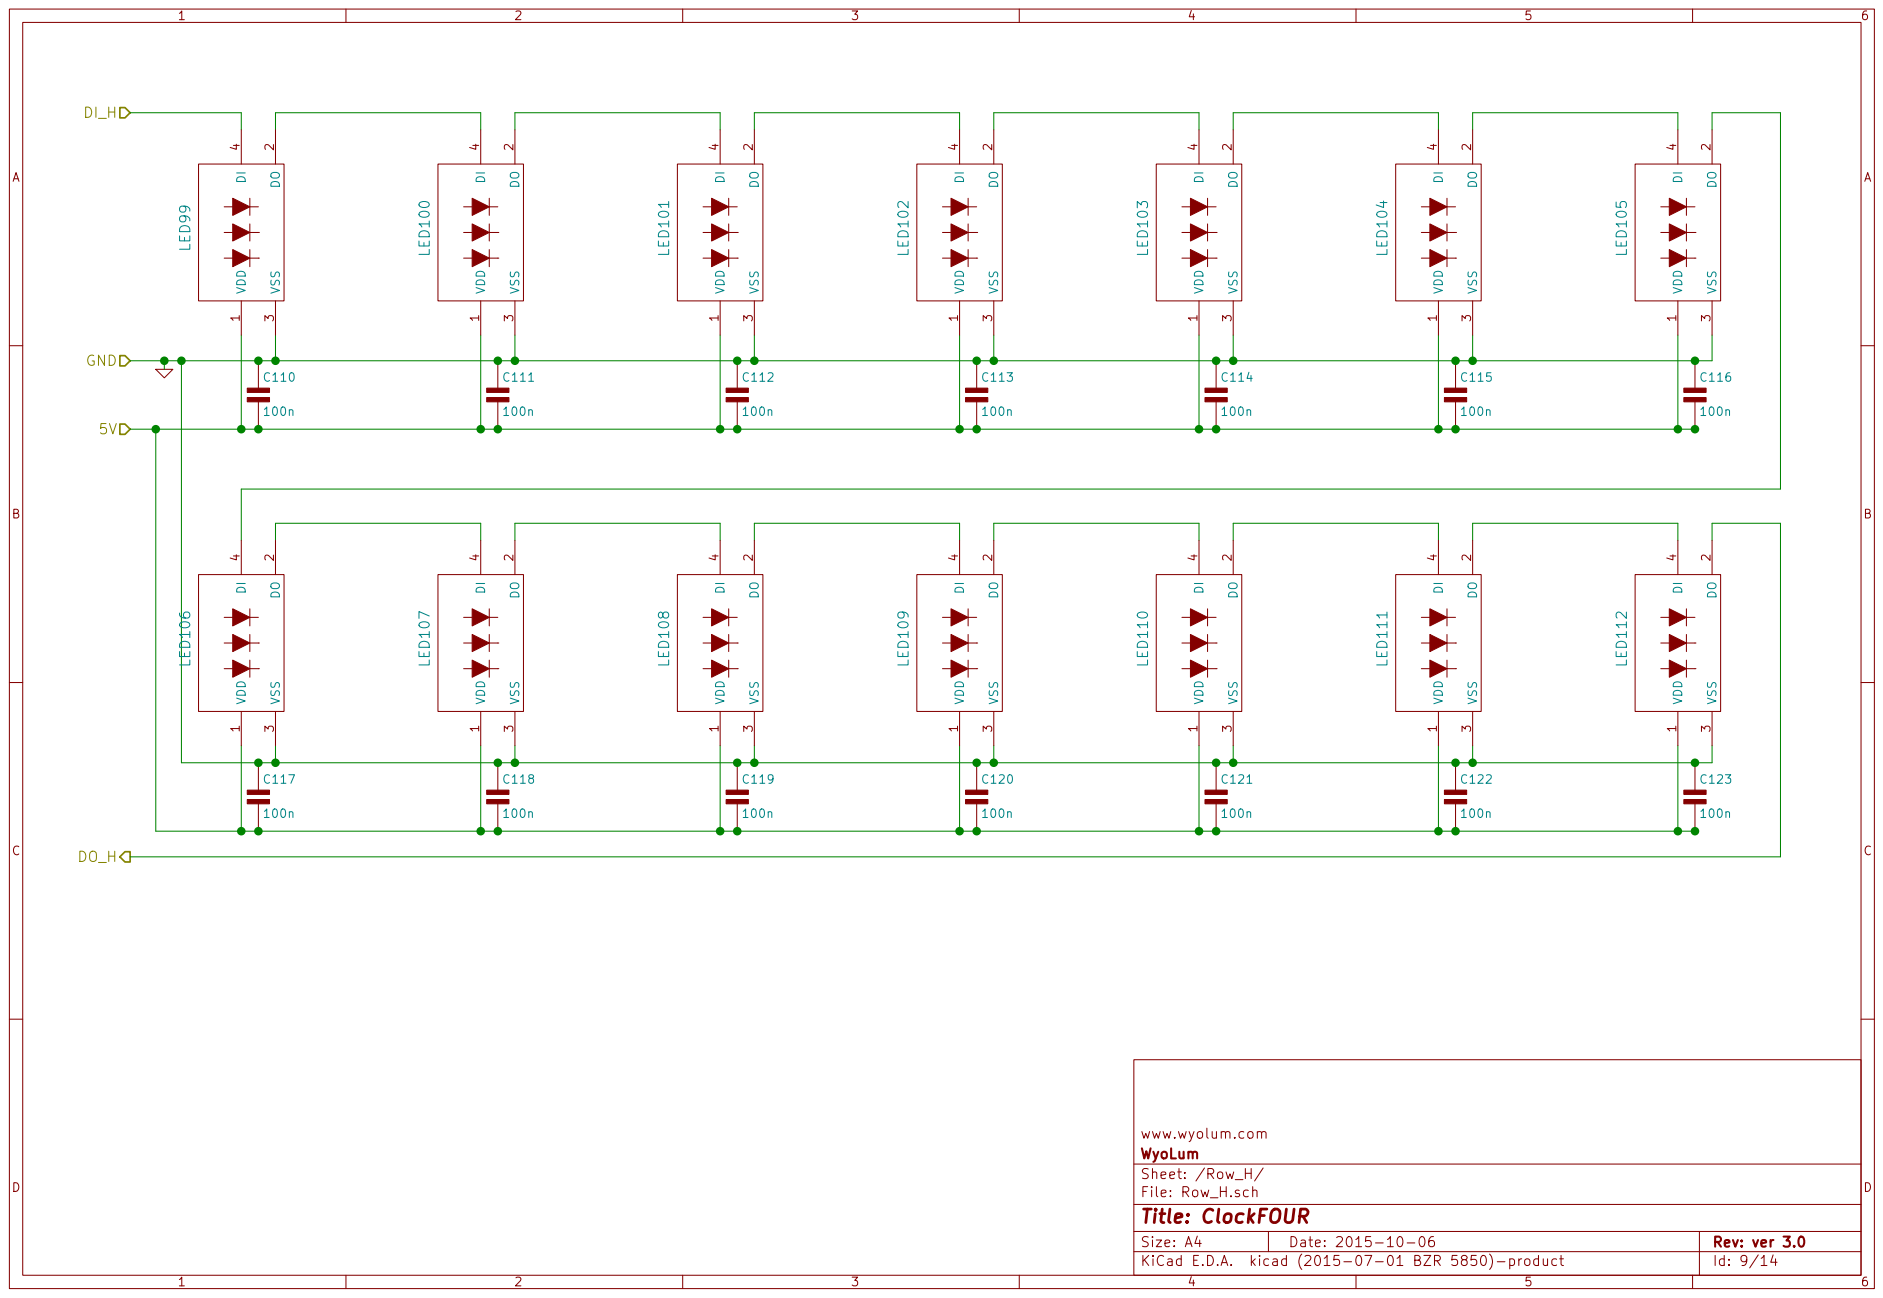
[picture p68: page 9]

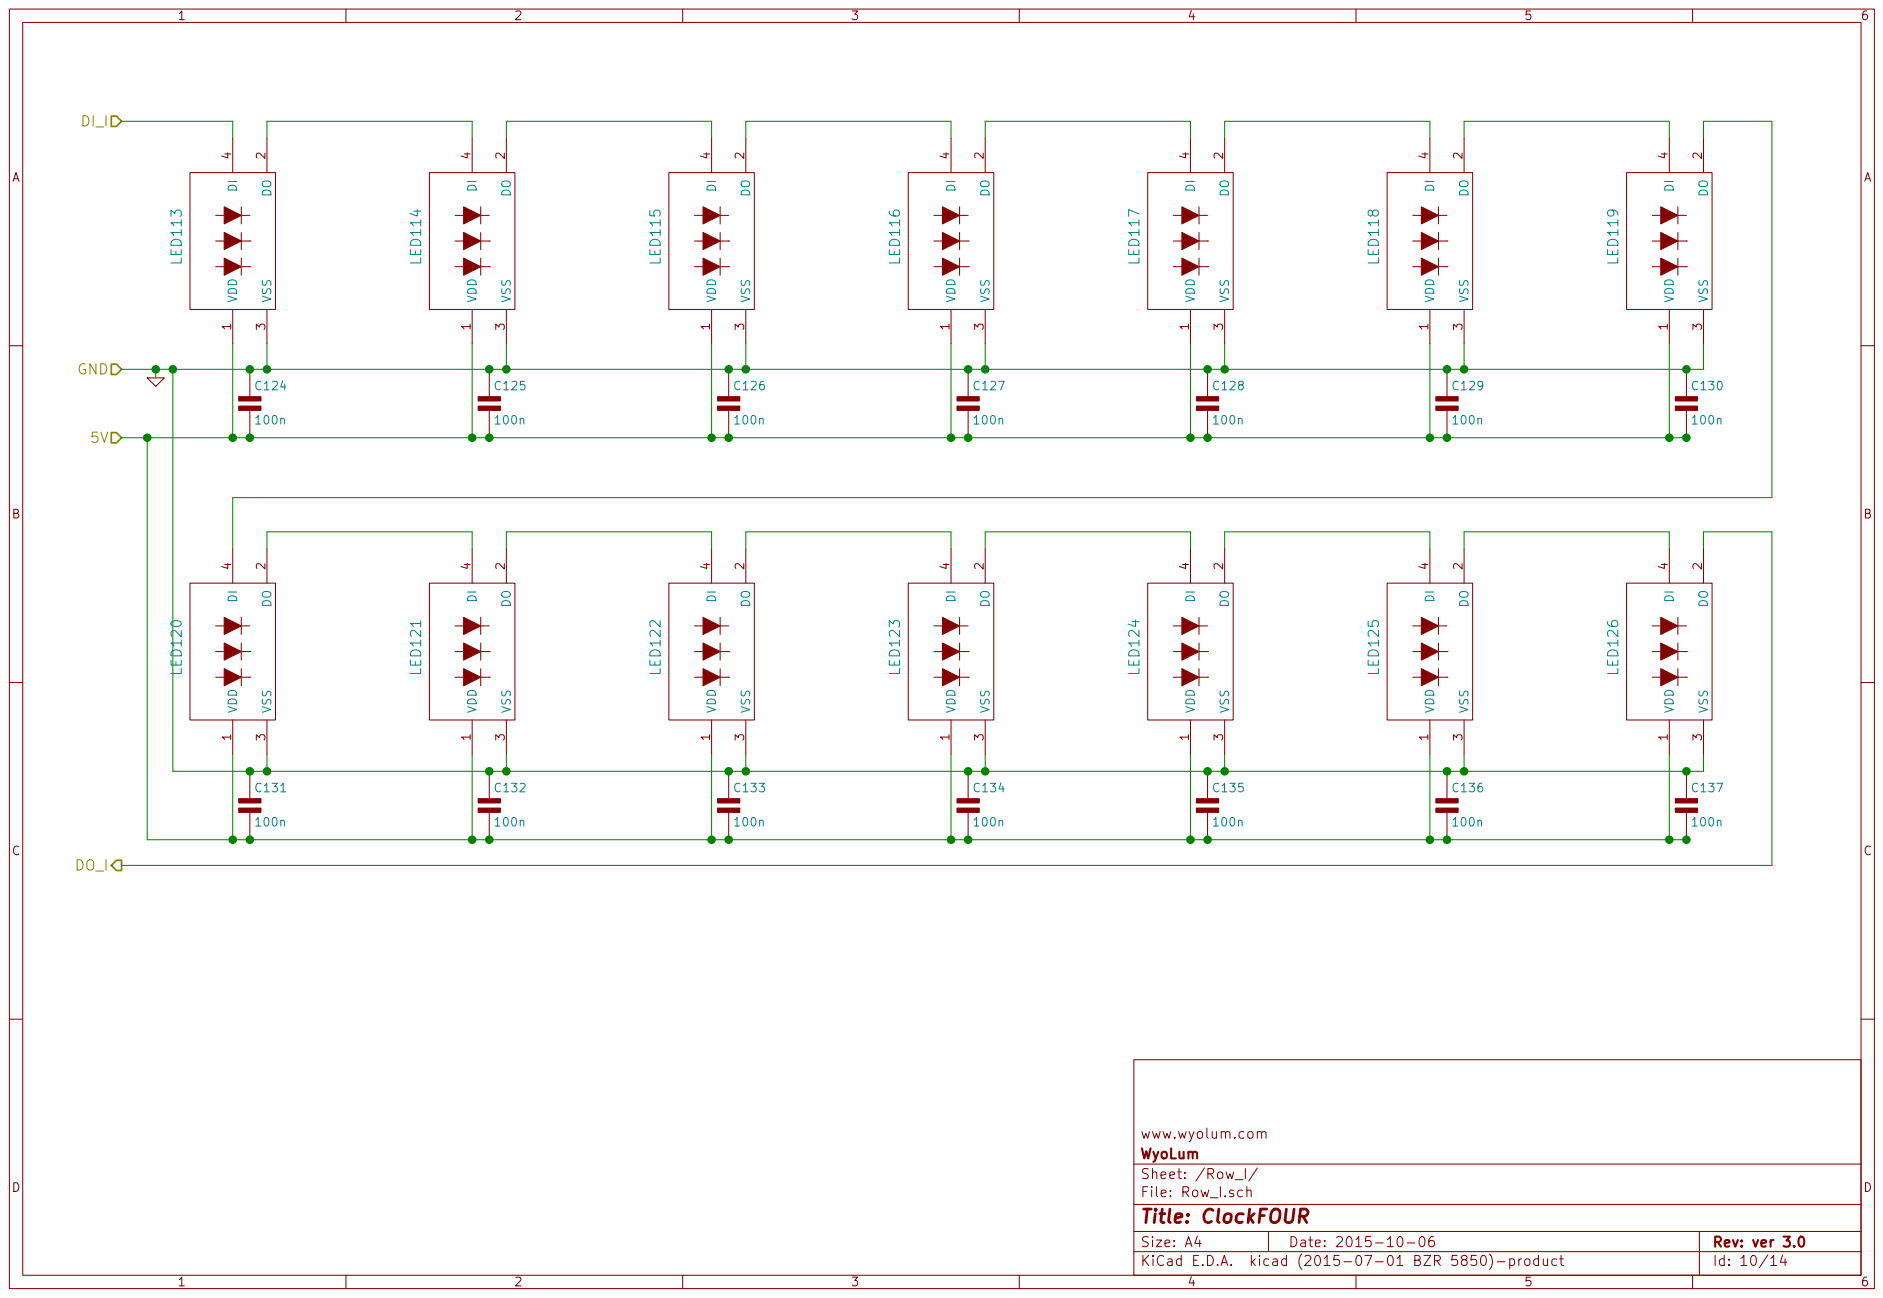
[picture p69: page 10]

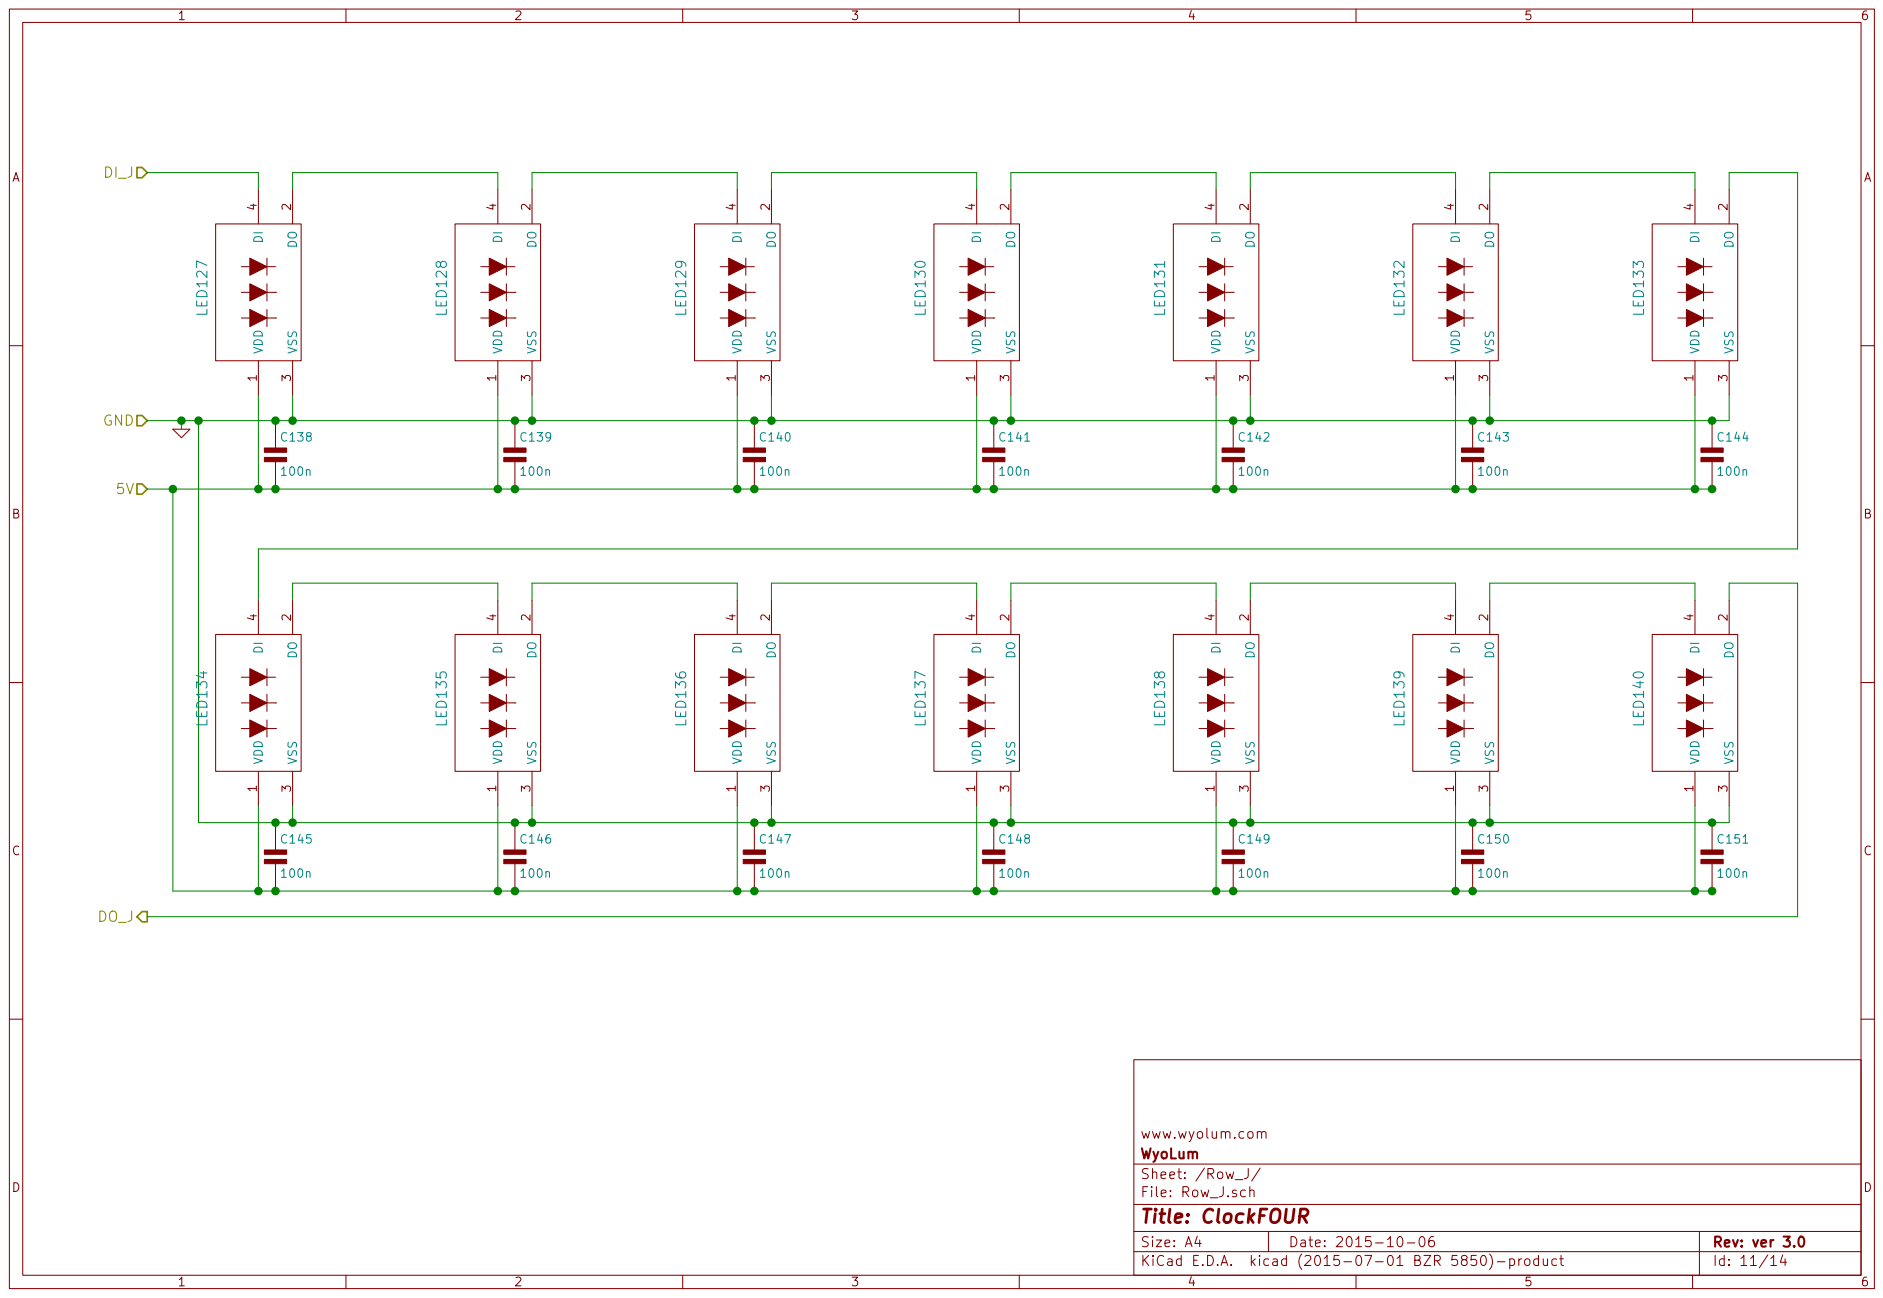
[picture p70: page 11]

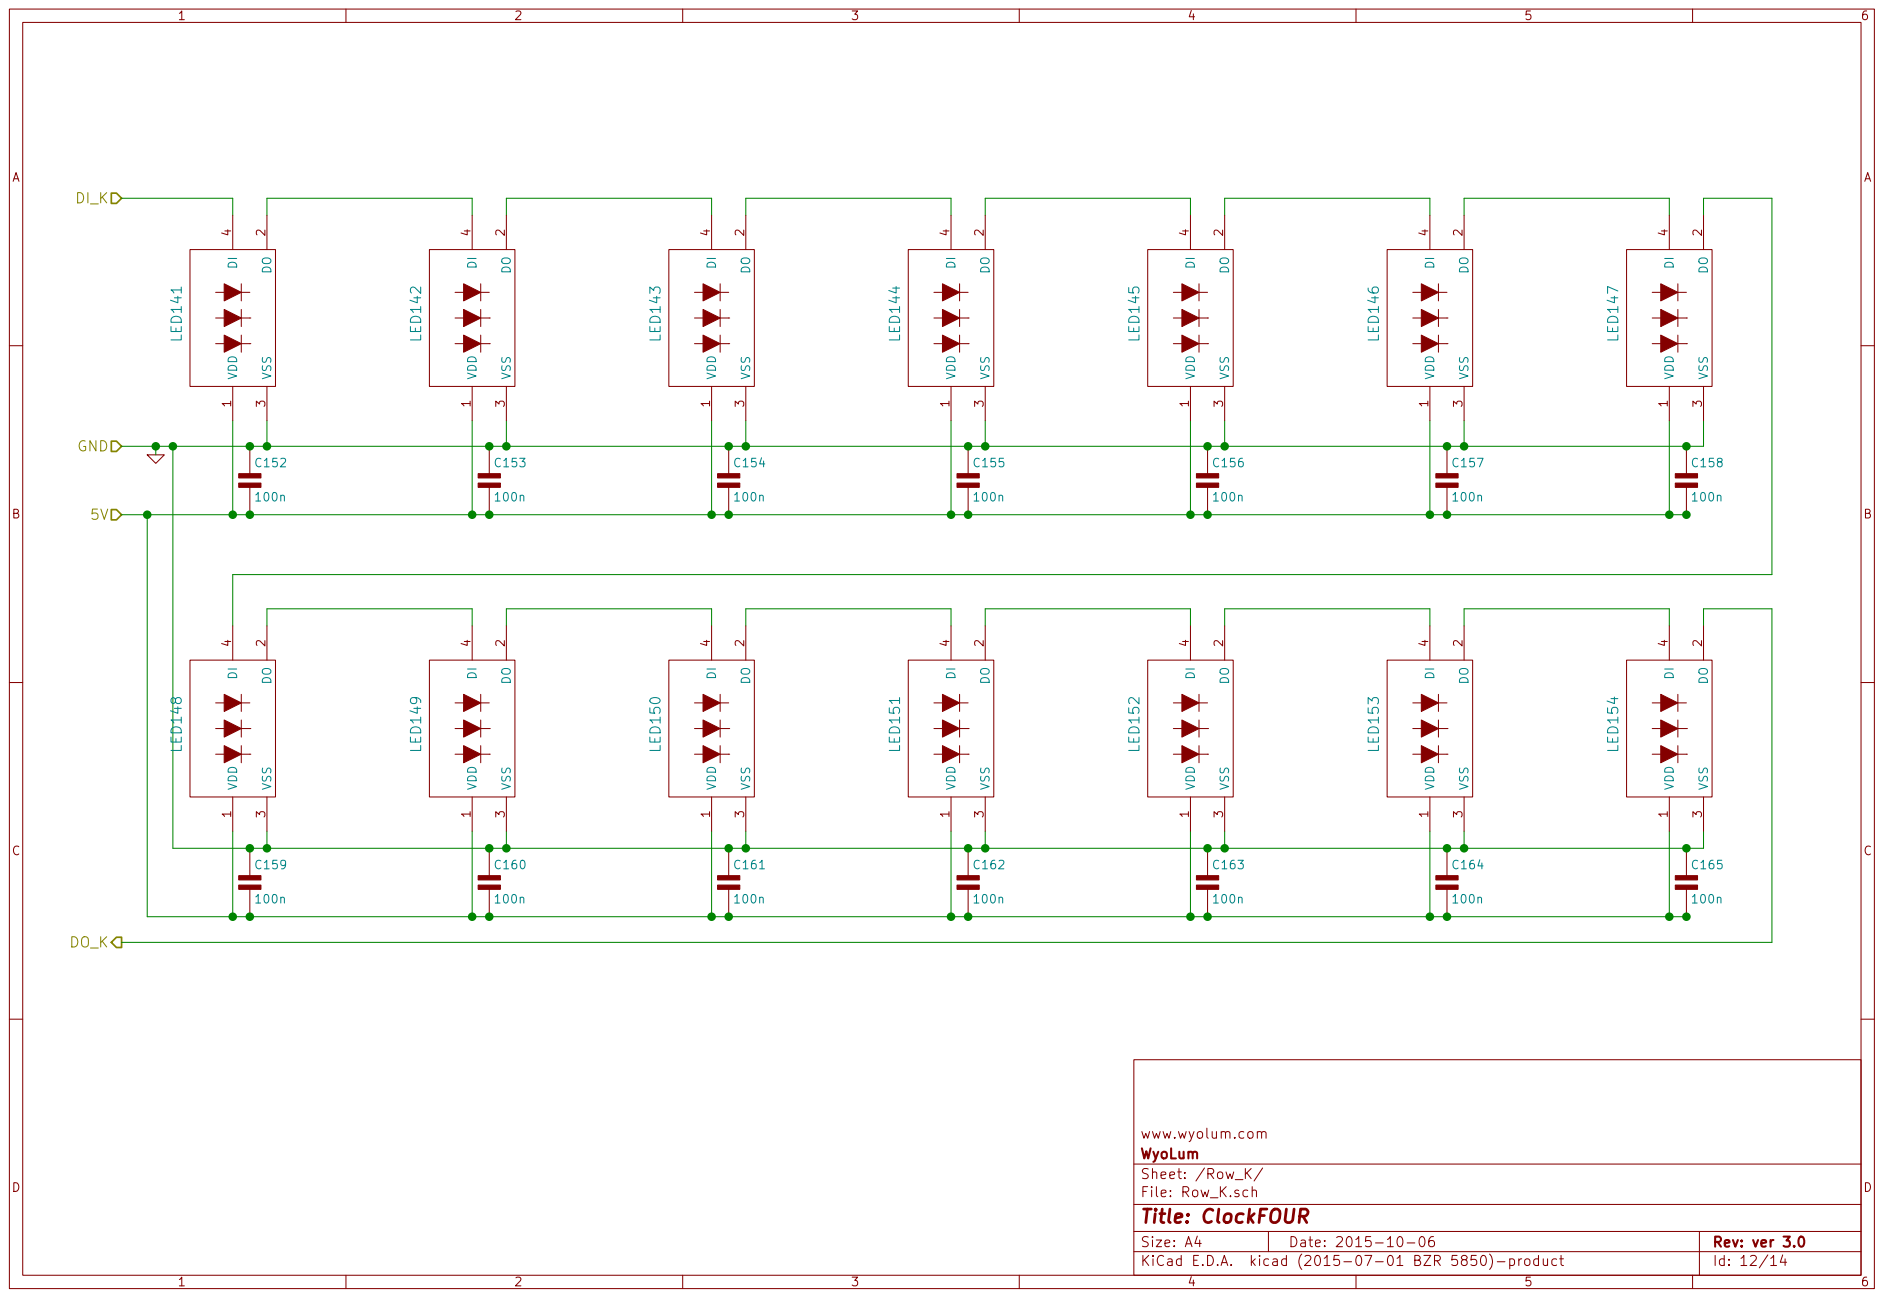
[picture p71: page 12]

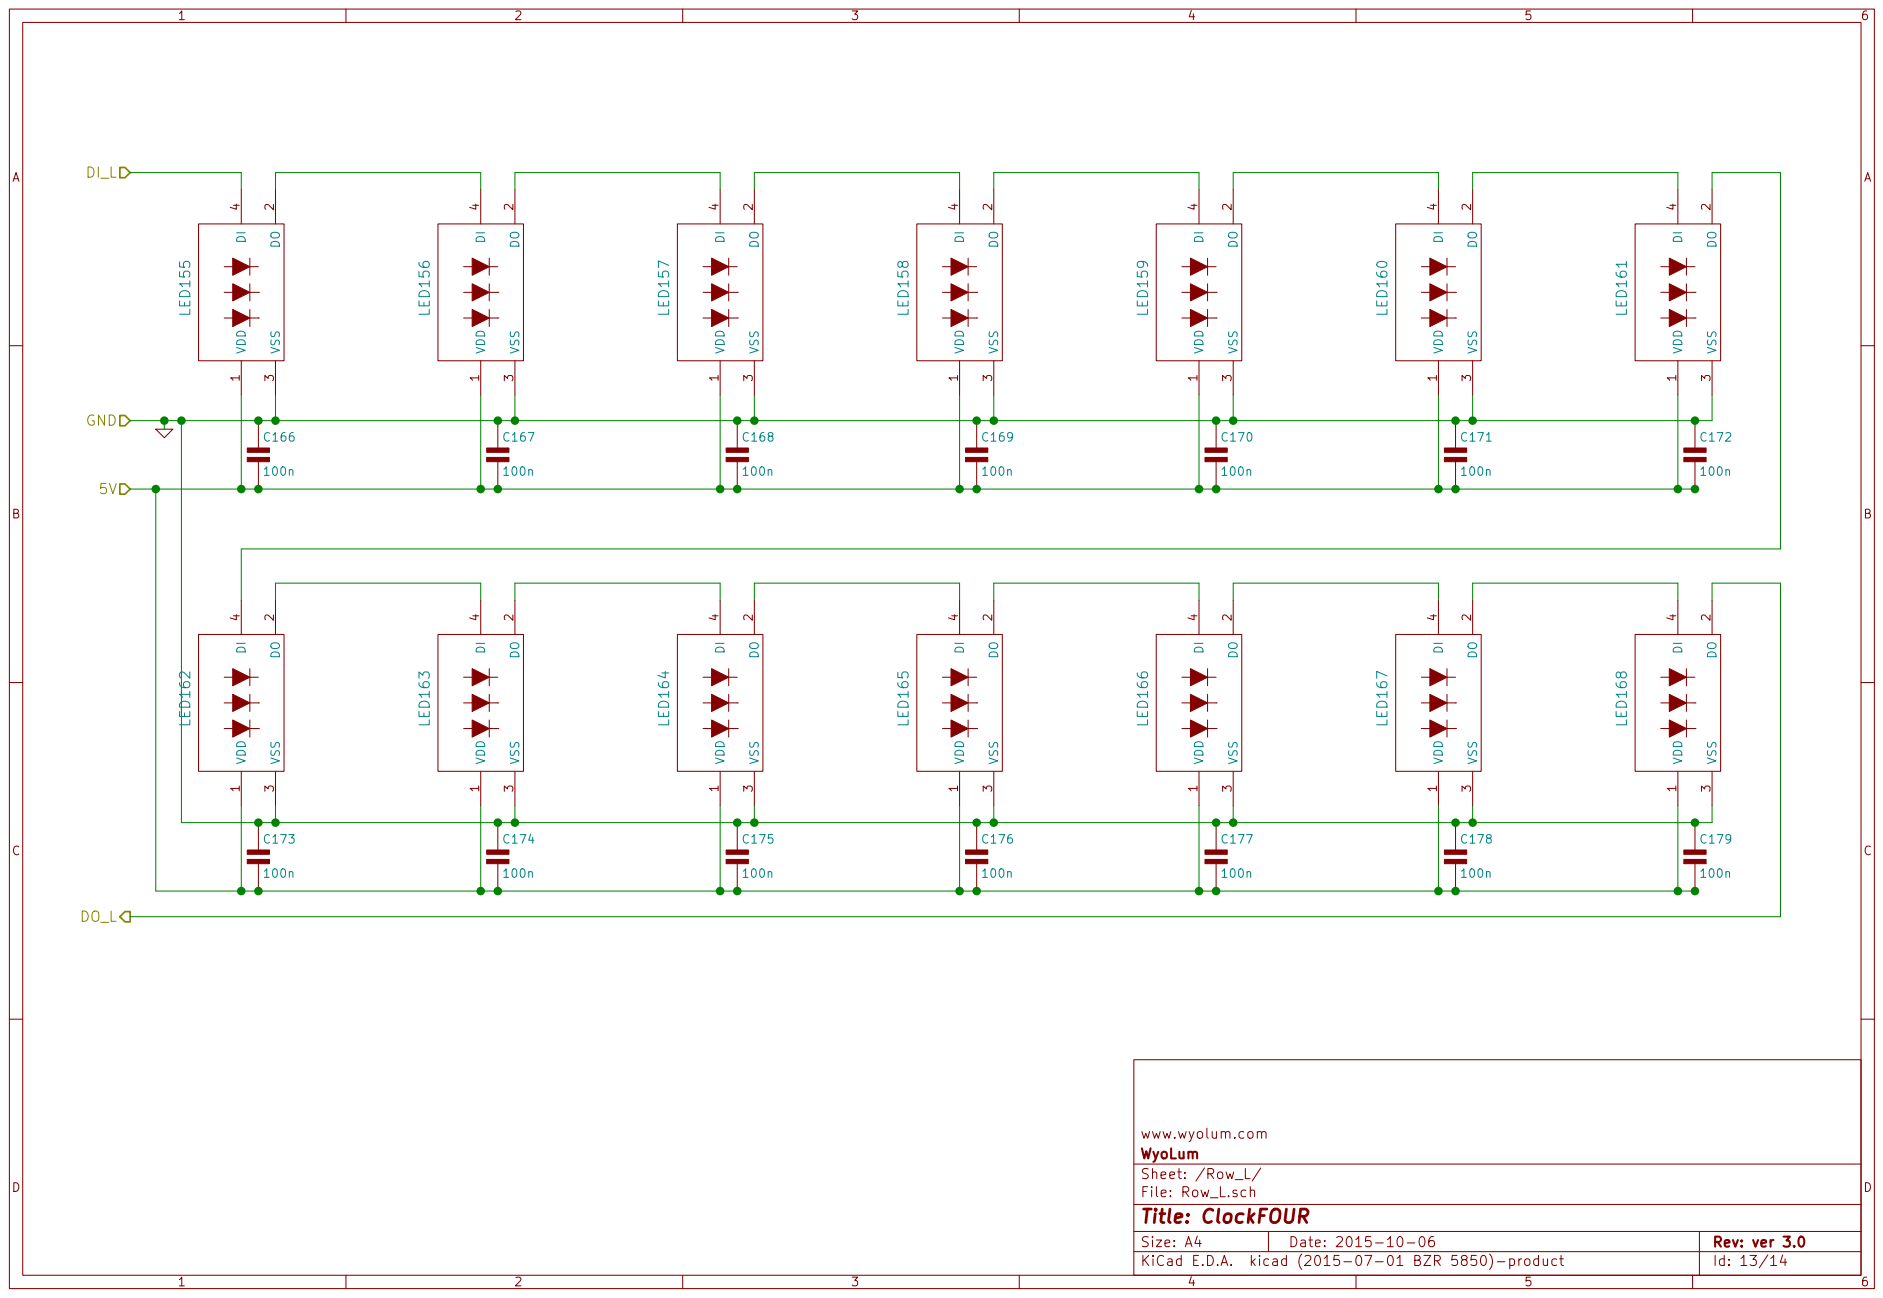
[picture p72: page 13]

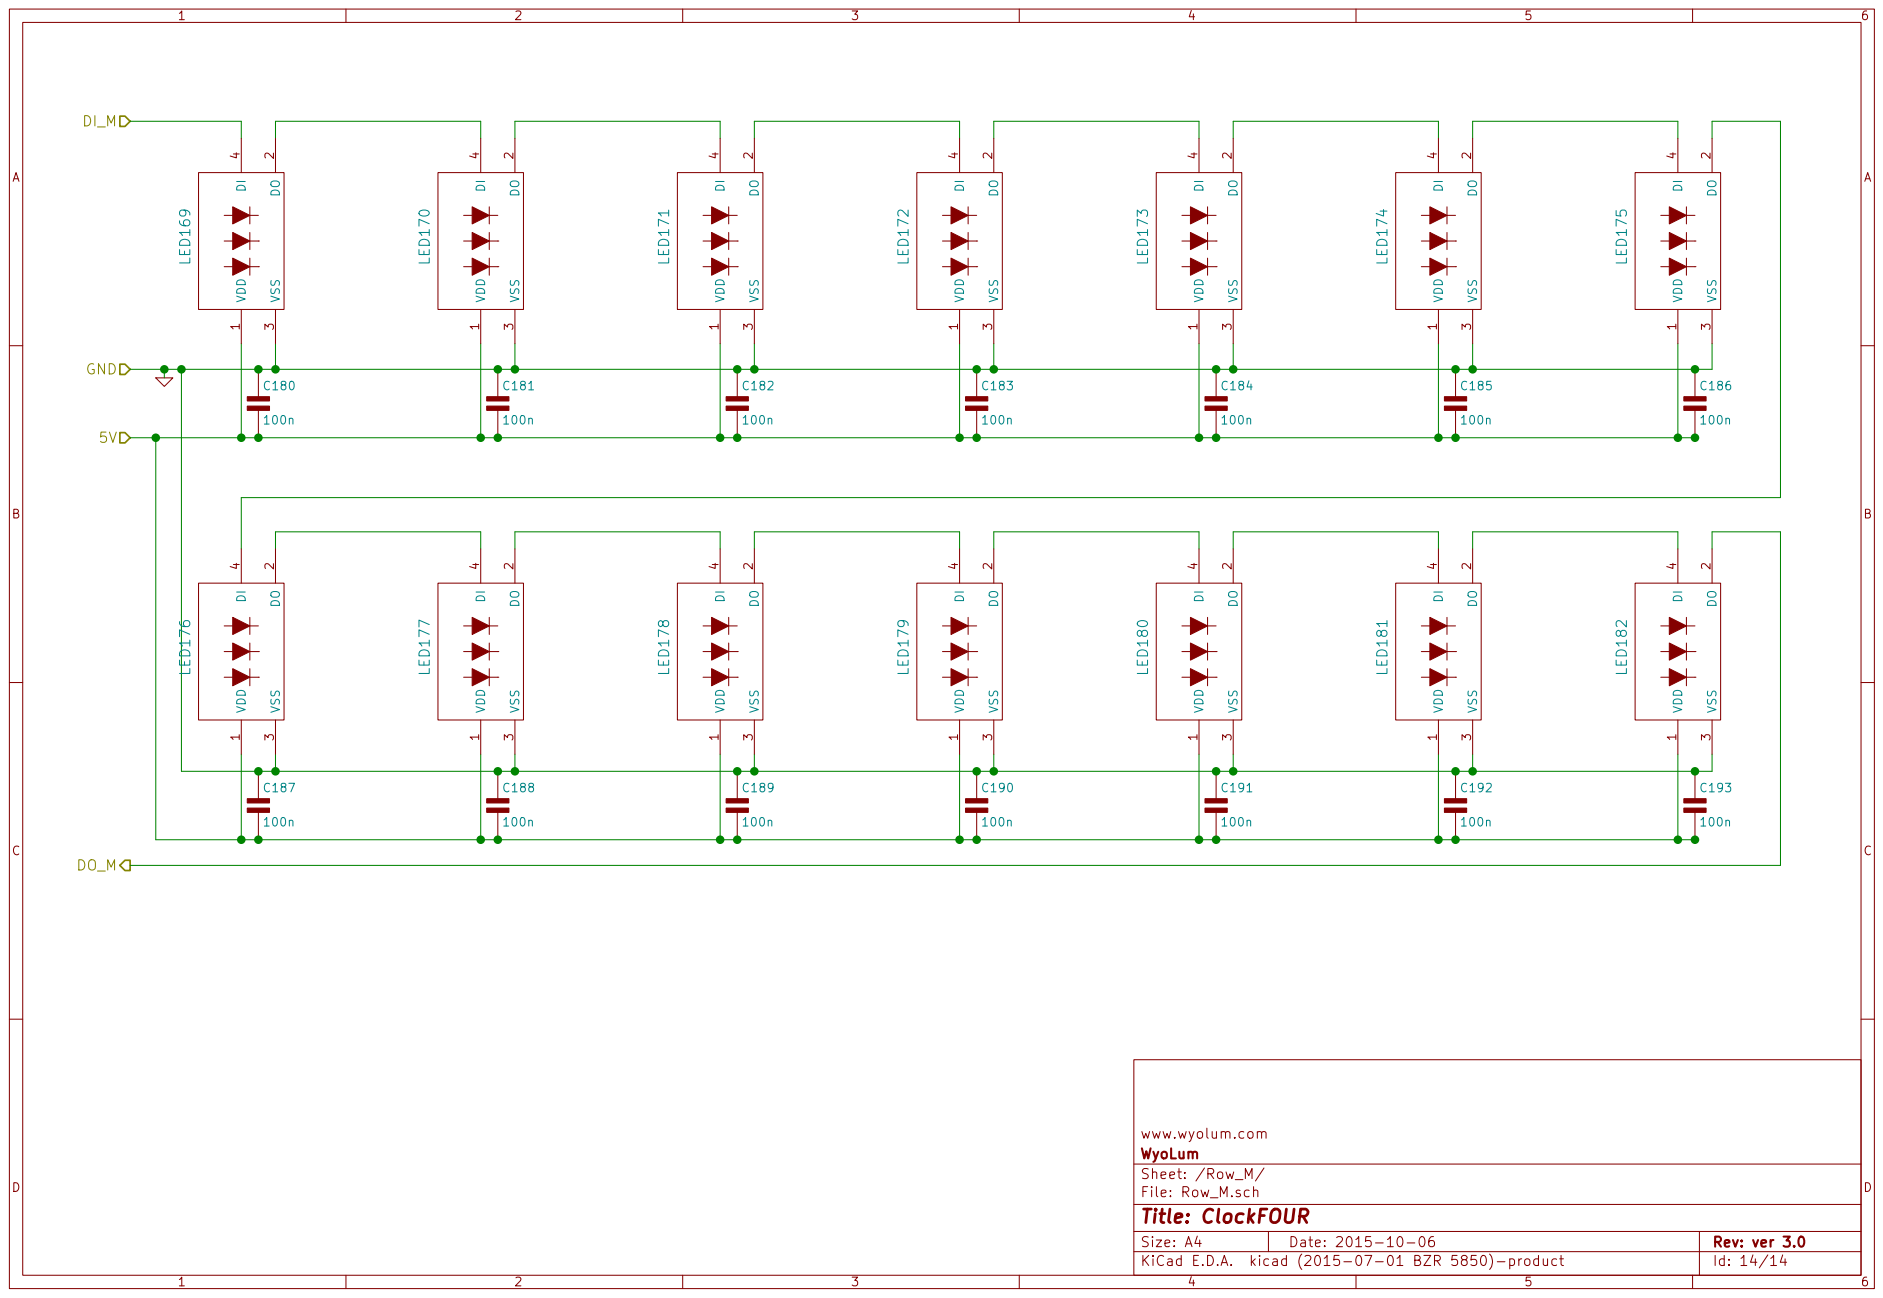
[picture p73: page 14]
