wyolum/ClockFOUR/KiCad/C4_rev1/ClockFOUR.pdf

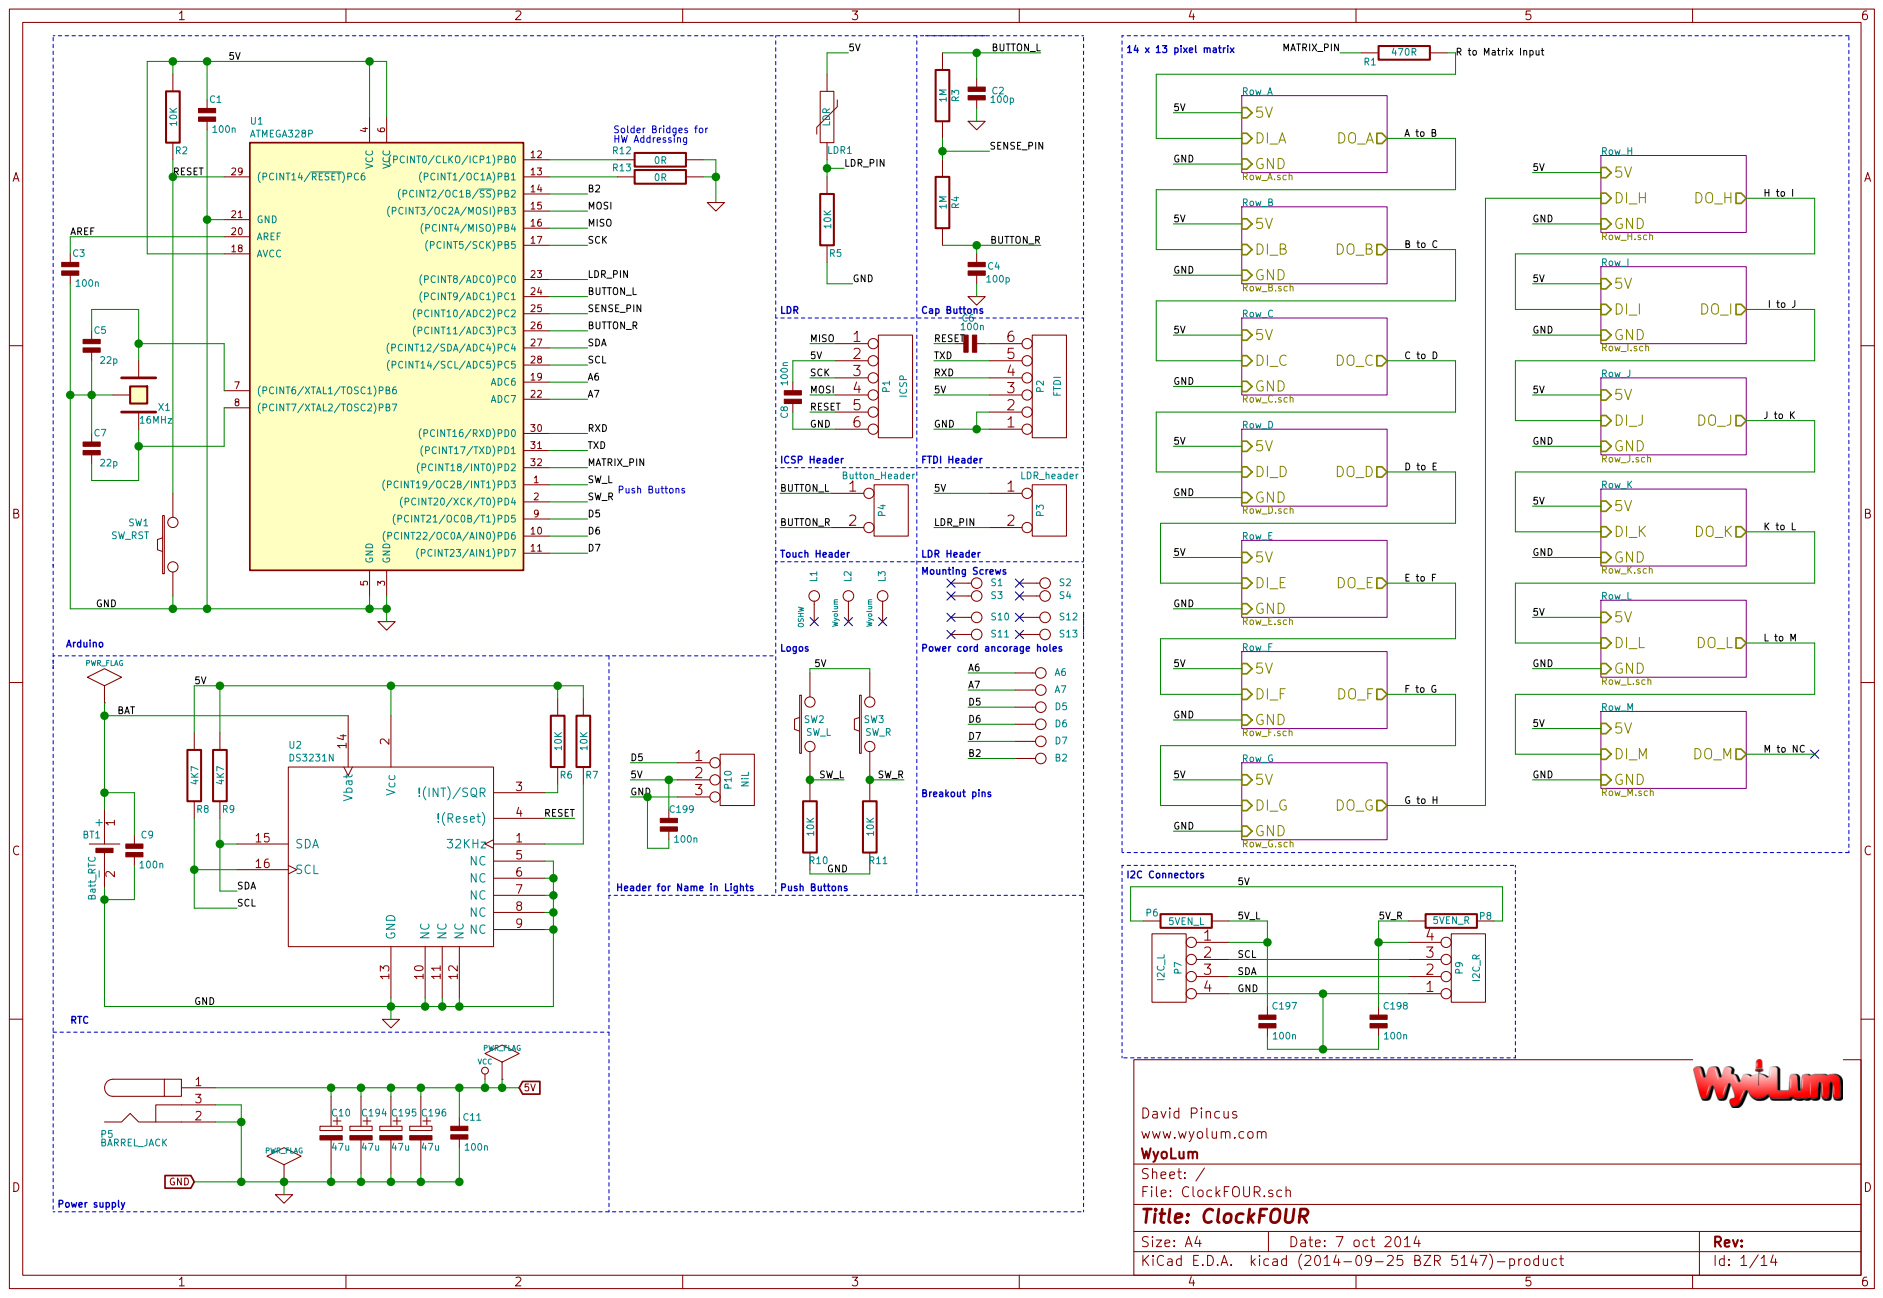
[picture p74: page 1]

5V GND

5VD5Header for Name in Lights C199

www.wyolum.com
File: ClockFOUR.sch Sheet: / WyoLum

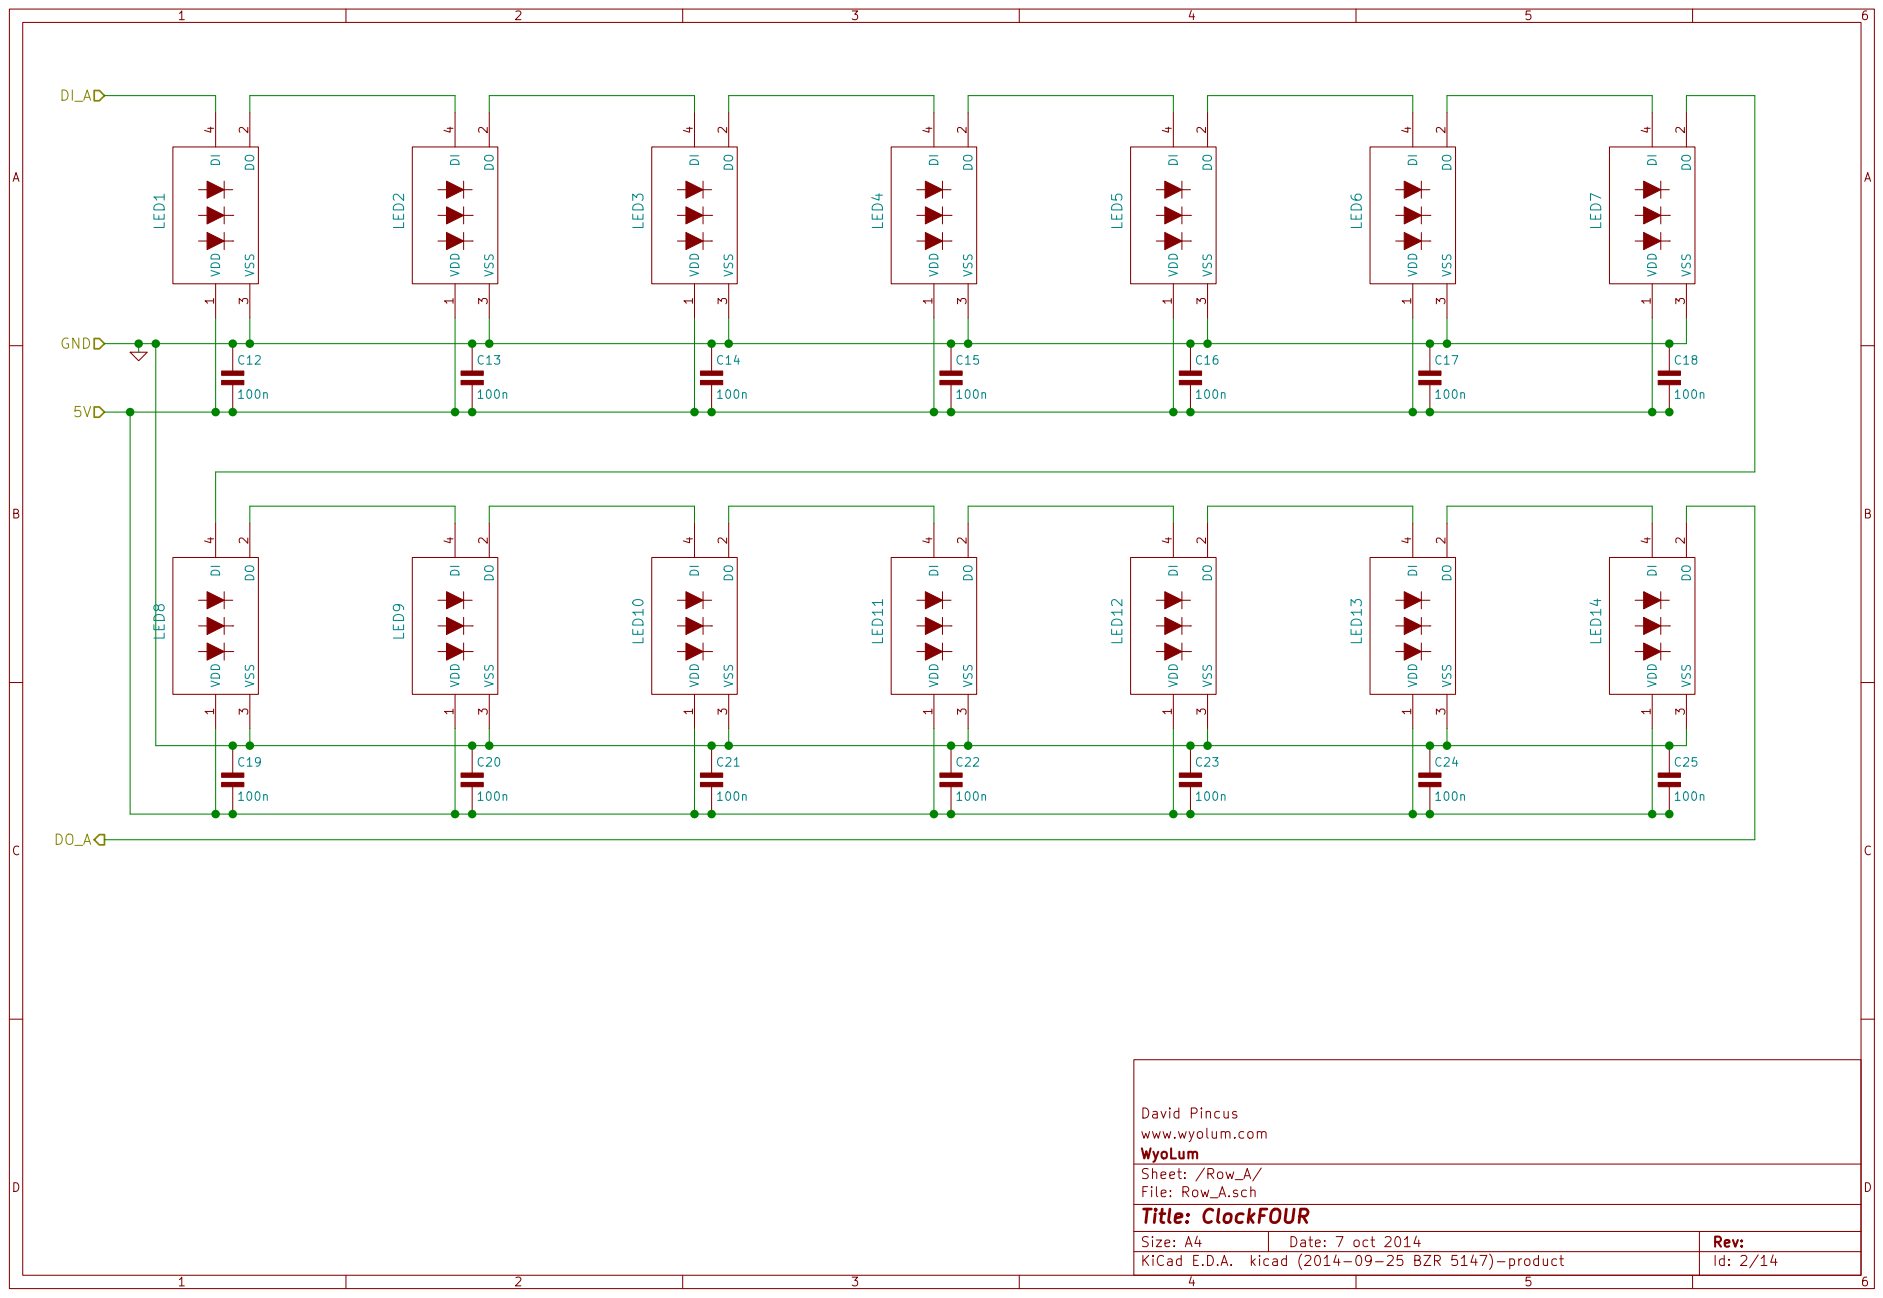
[picture p75: page 2]

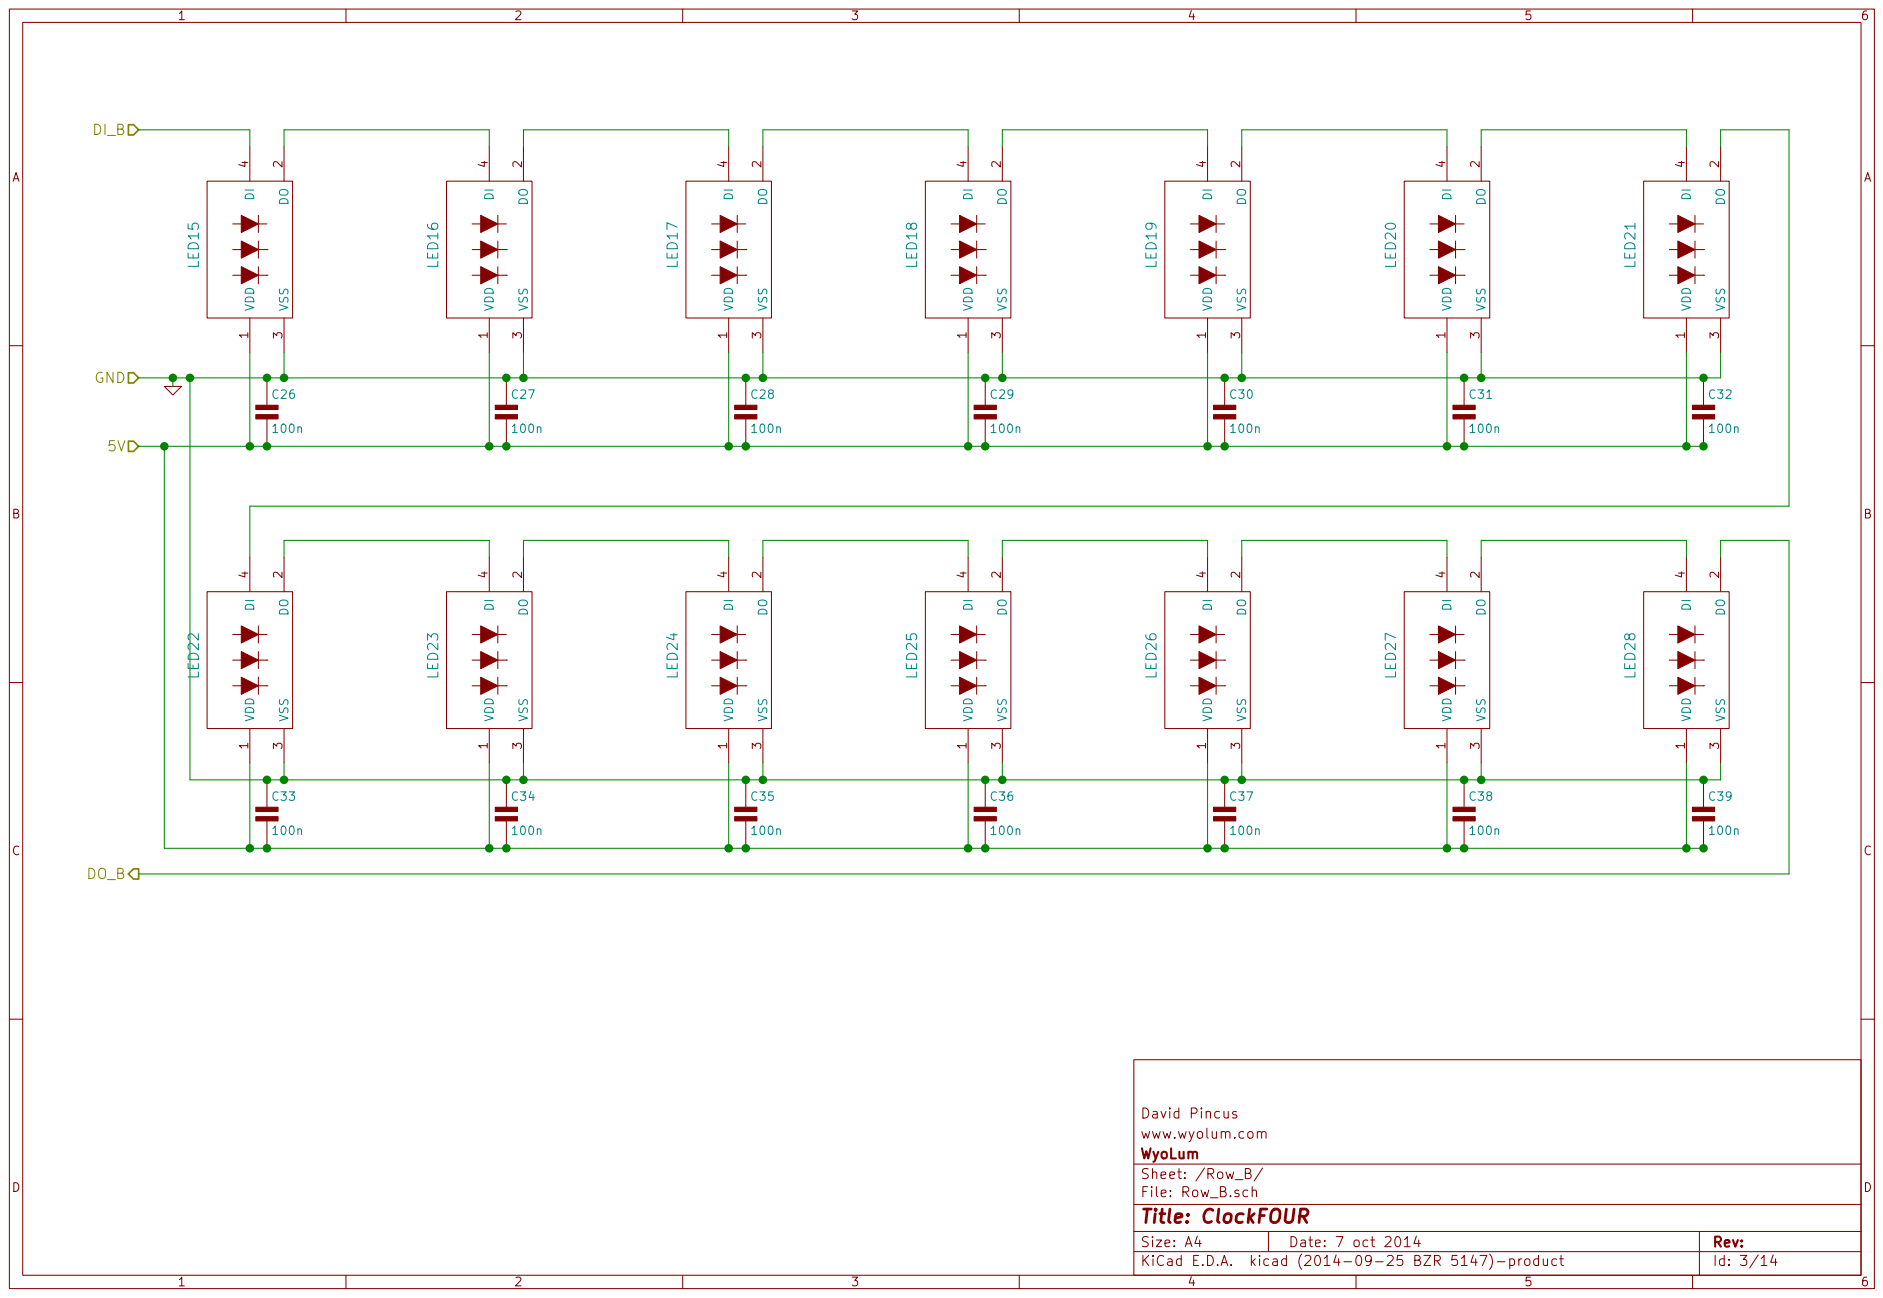
[picture p76: page 3]

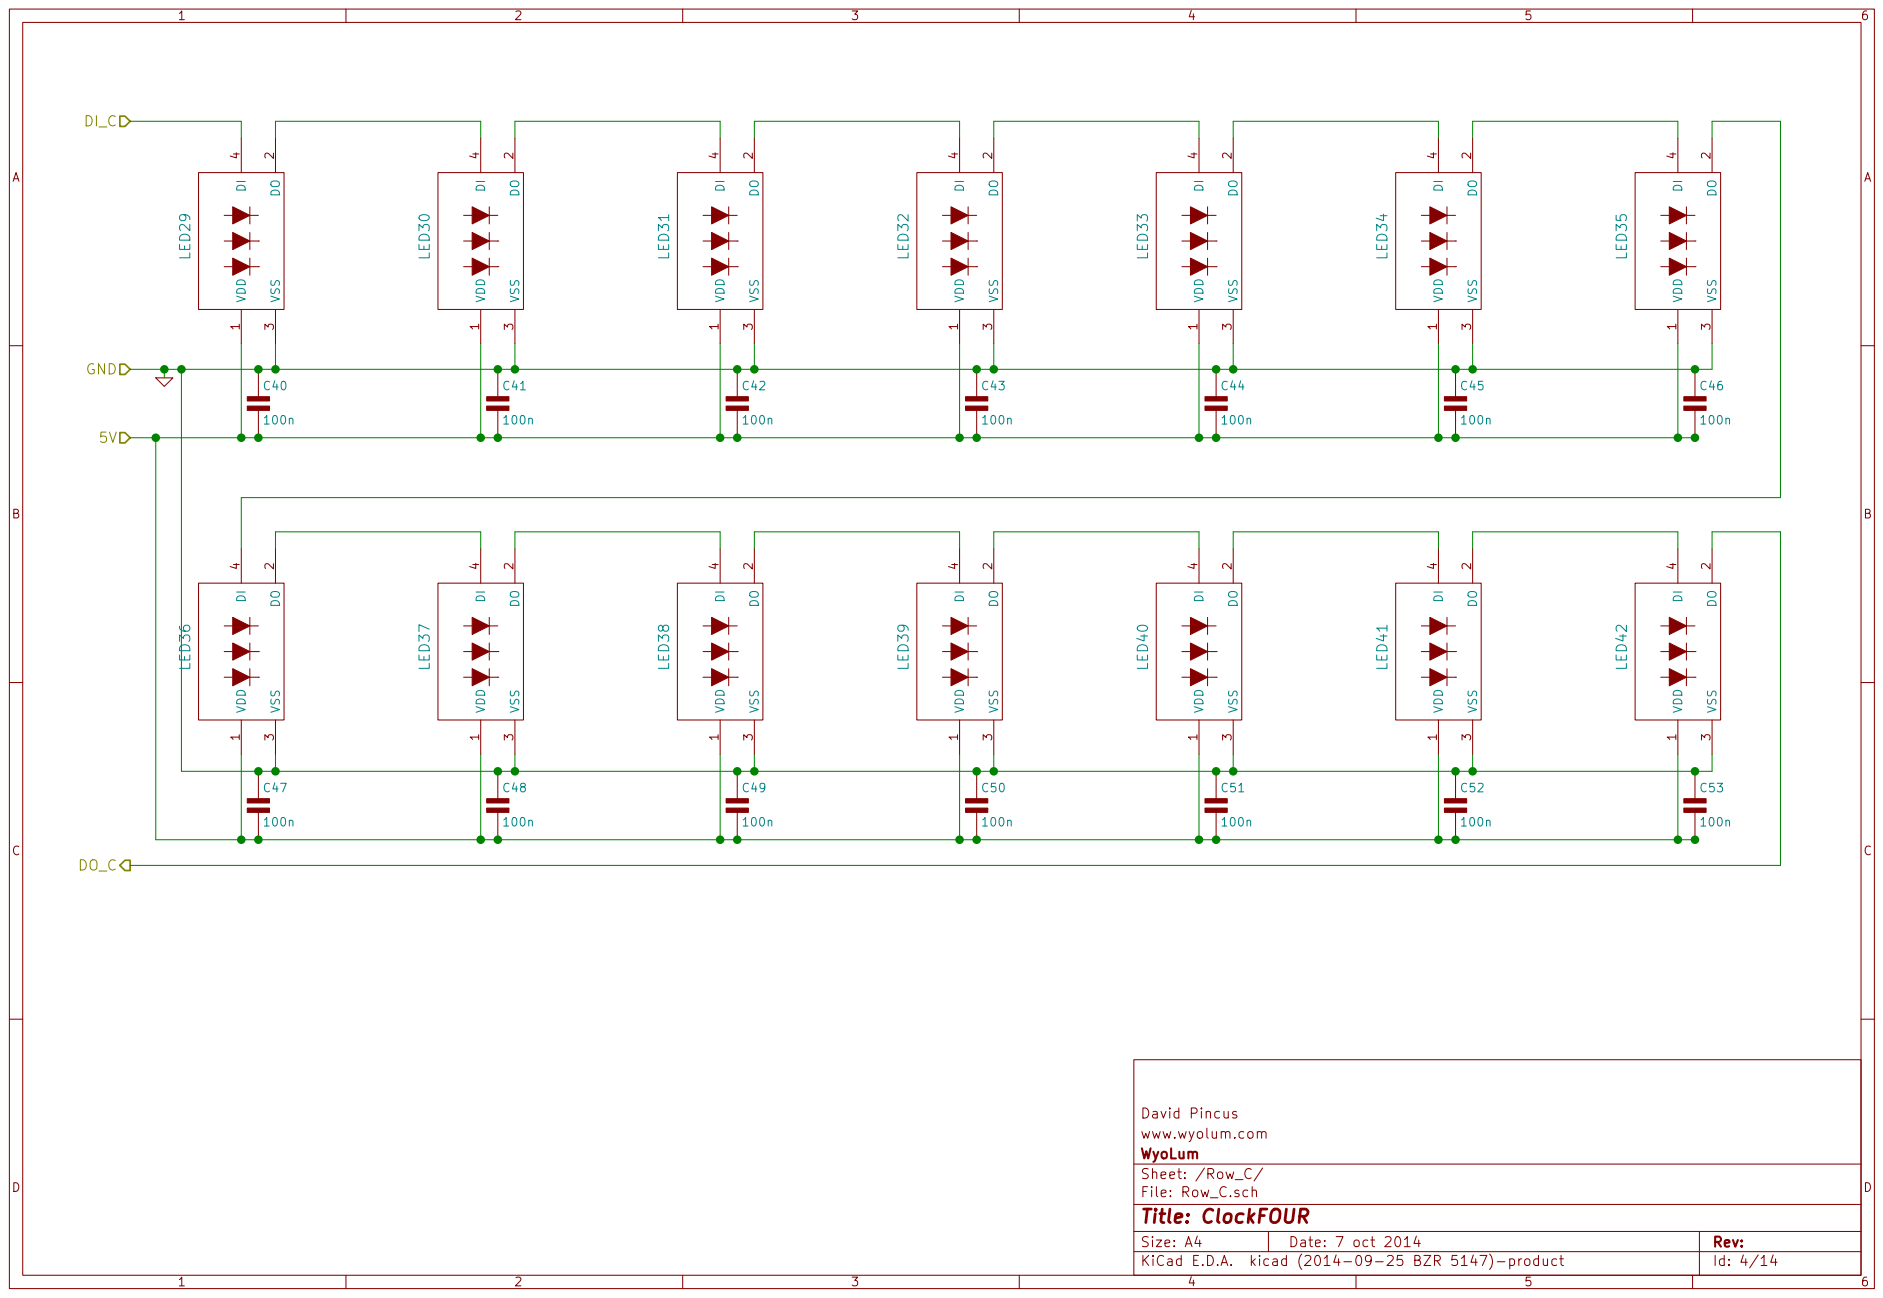
[picture p77: page 4]

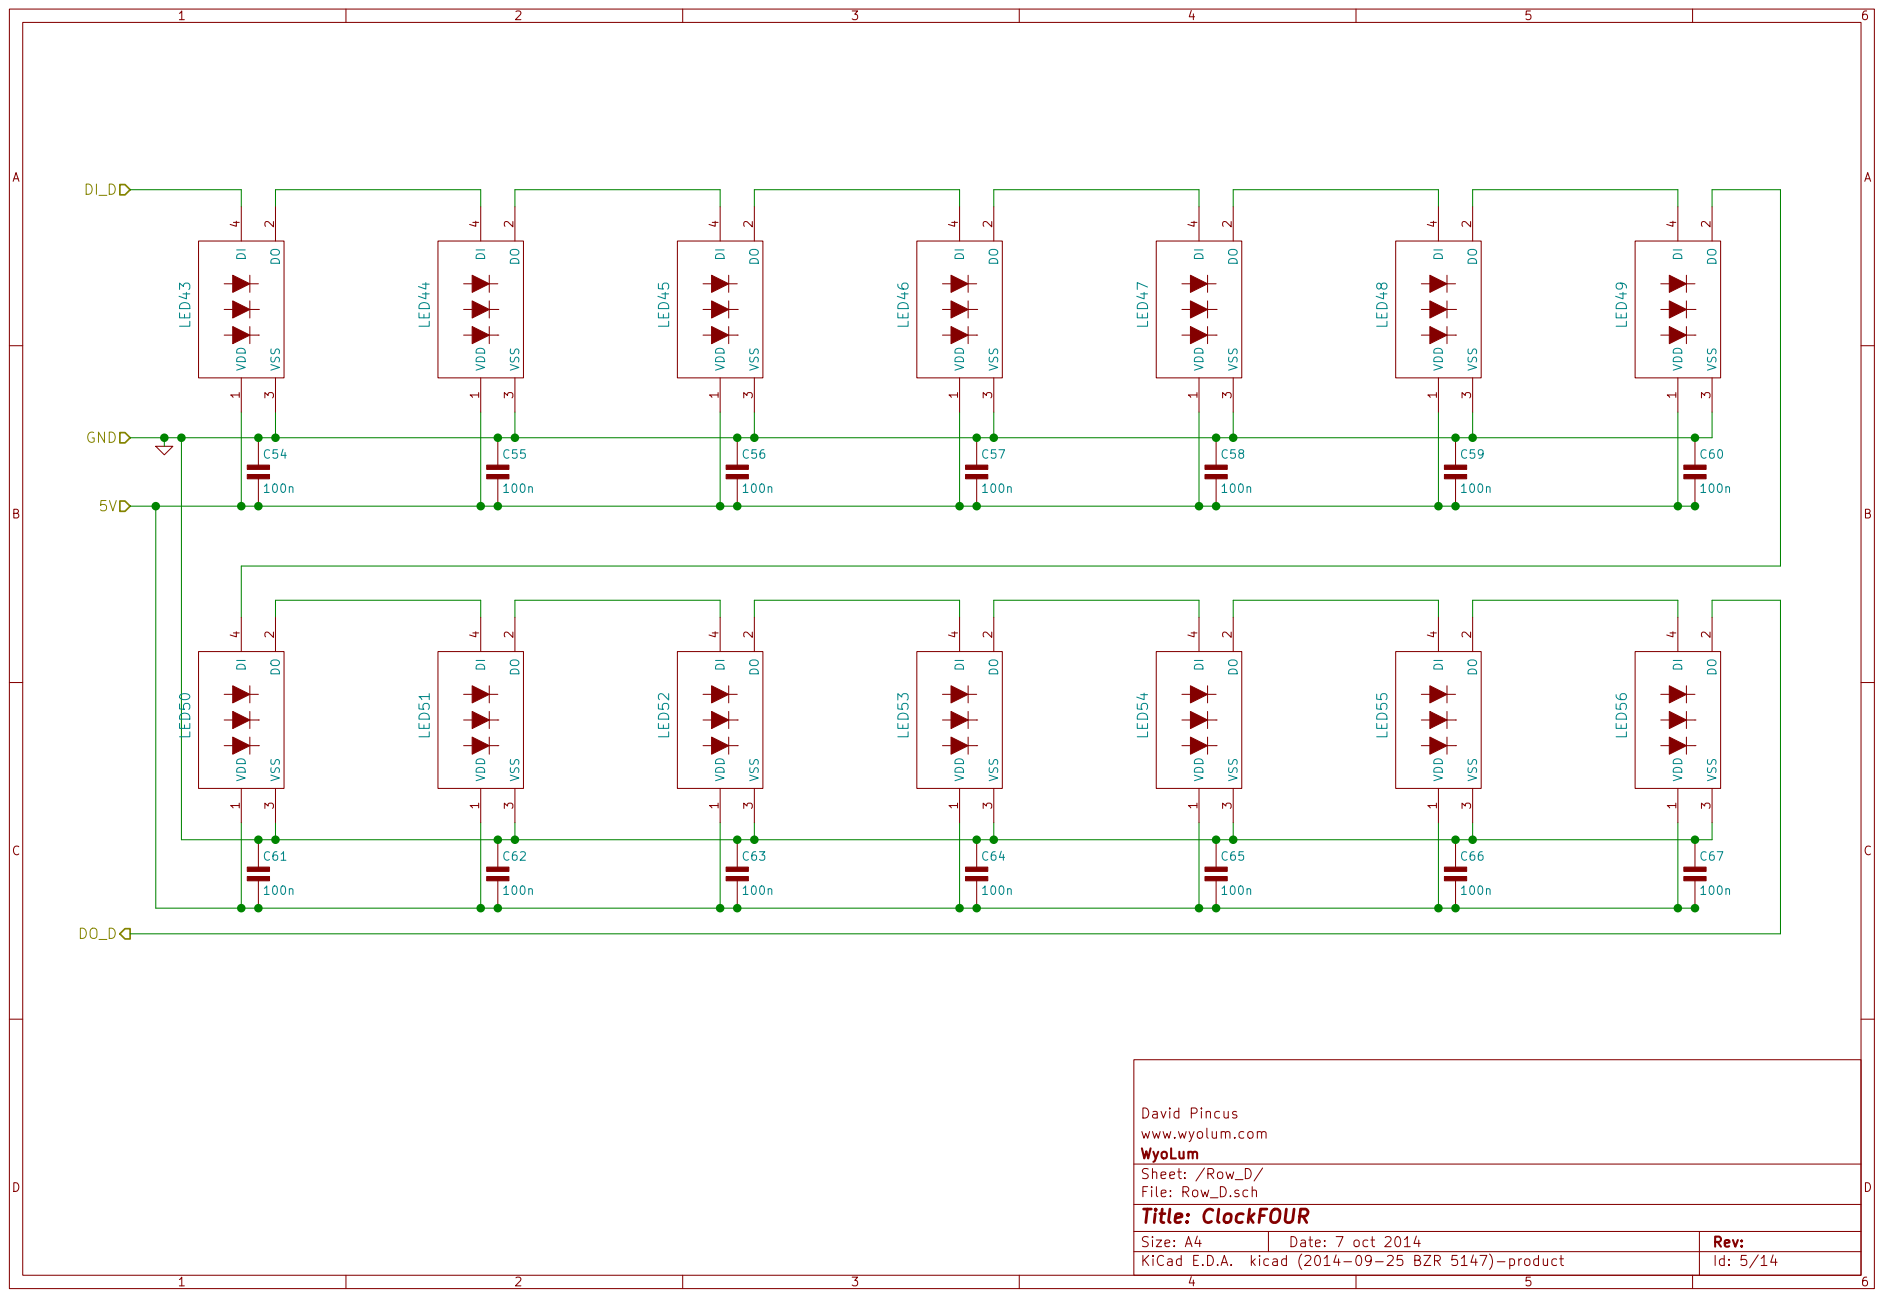
[picture p78: page 5]

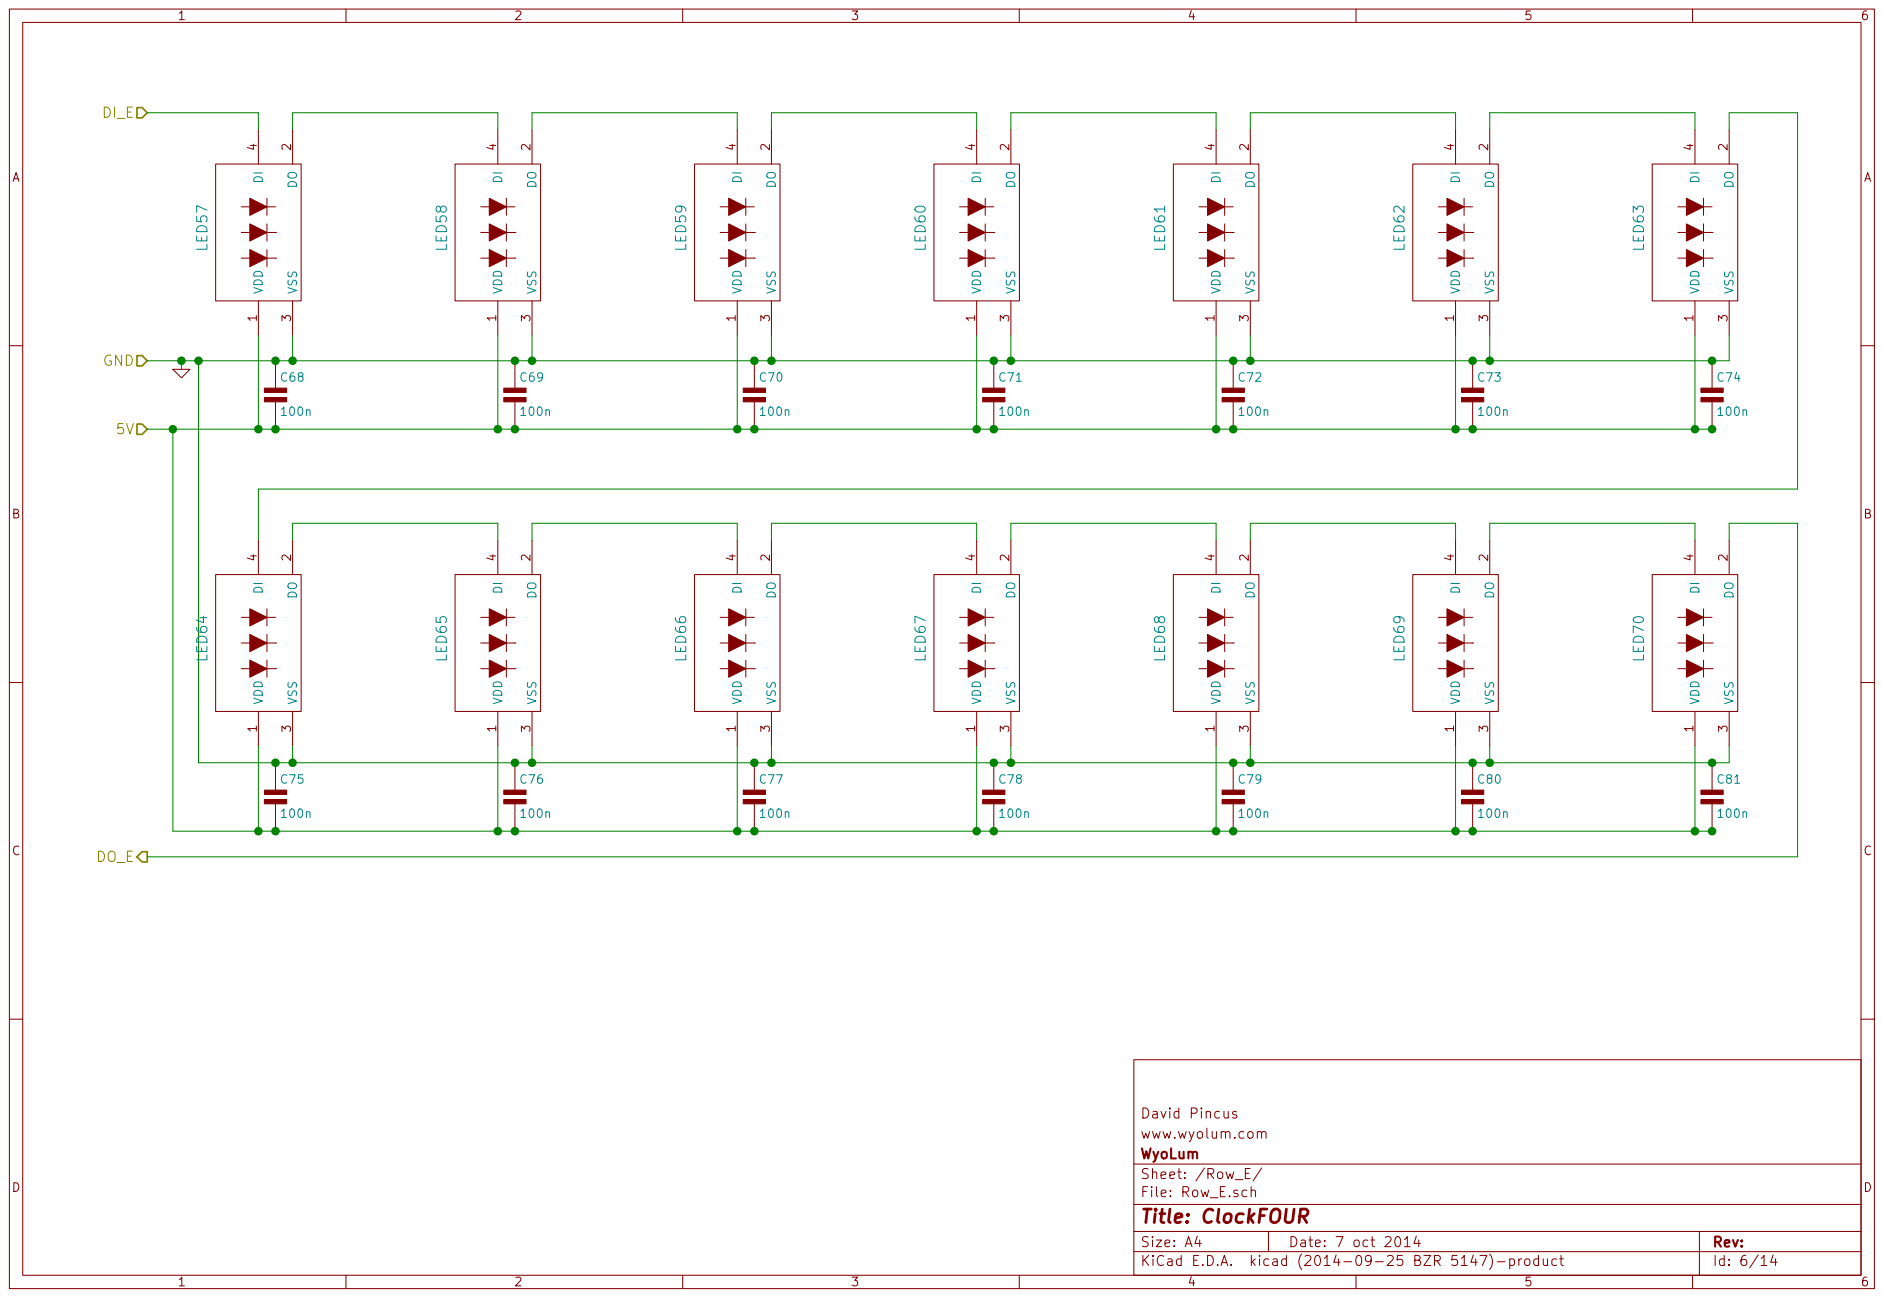
[picture p79: page 6]

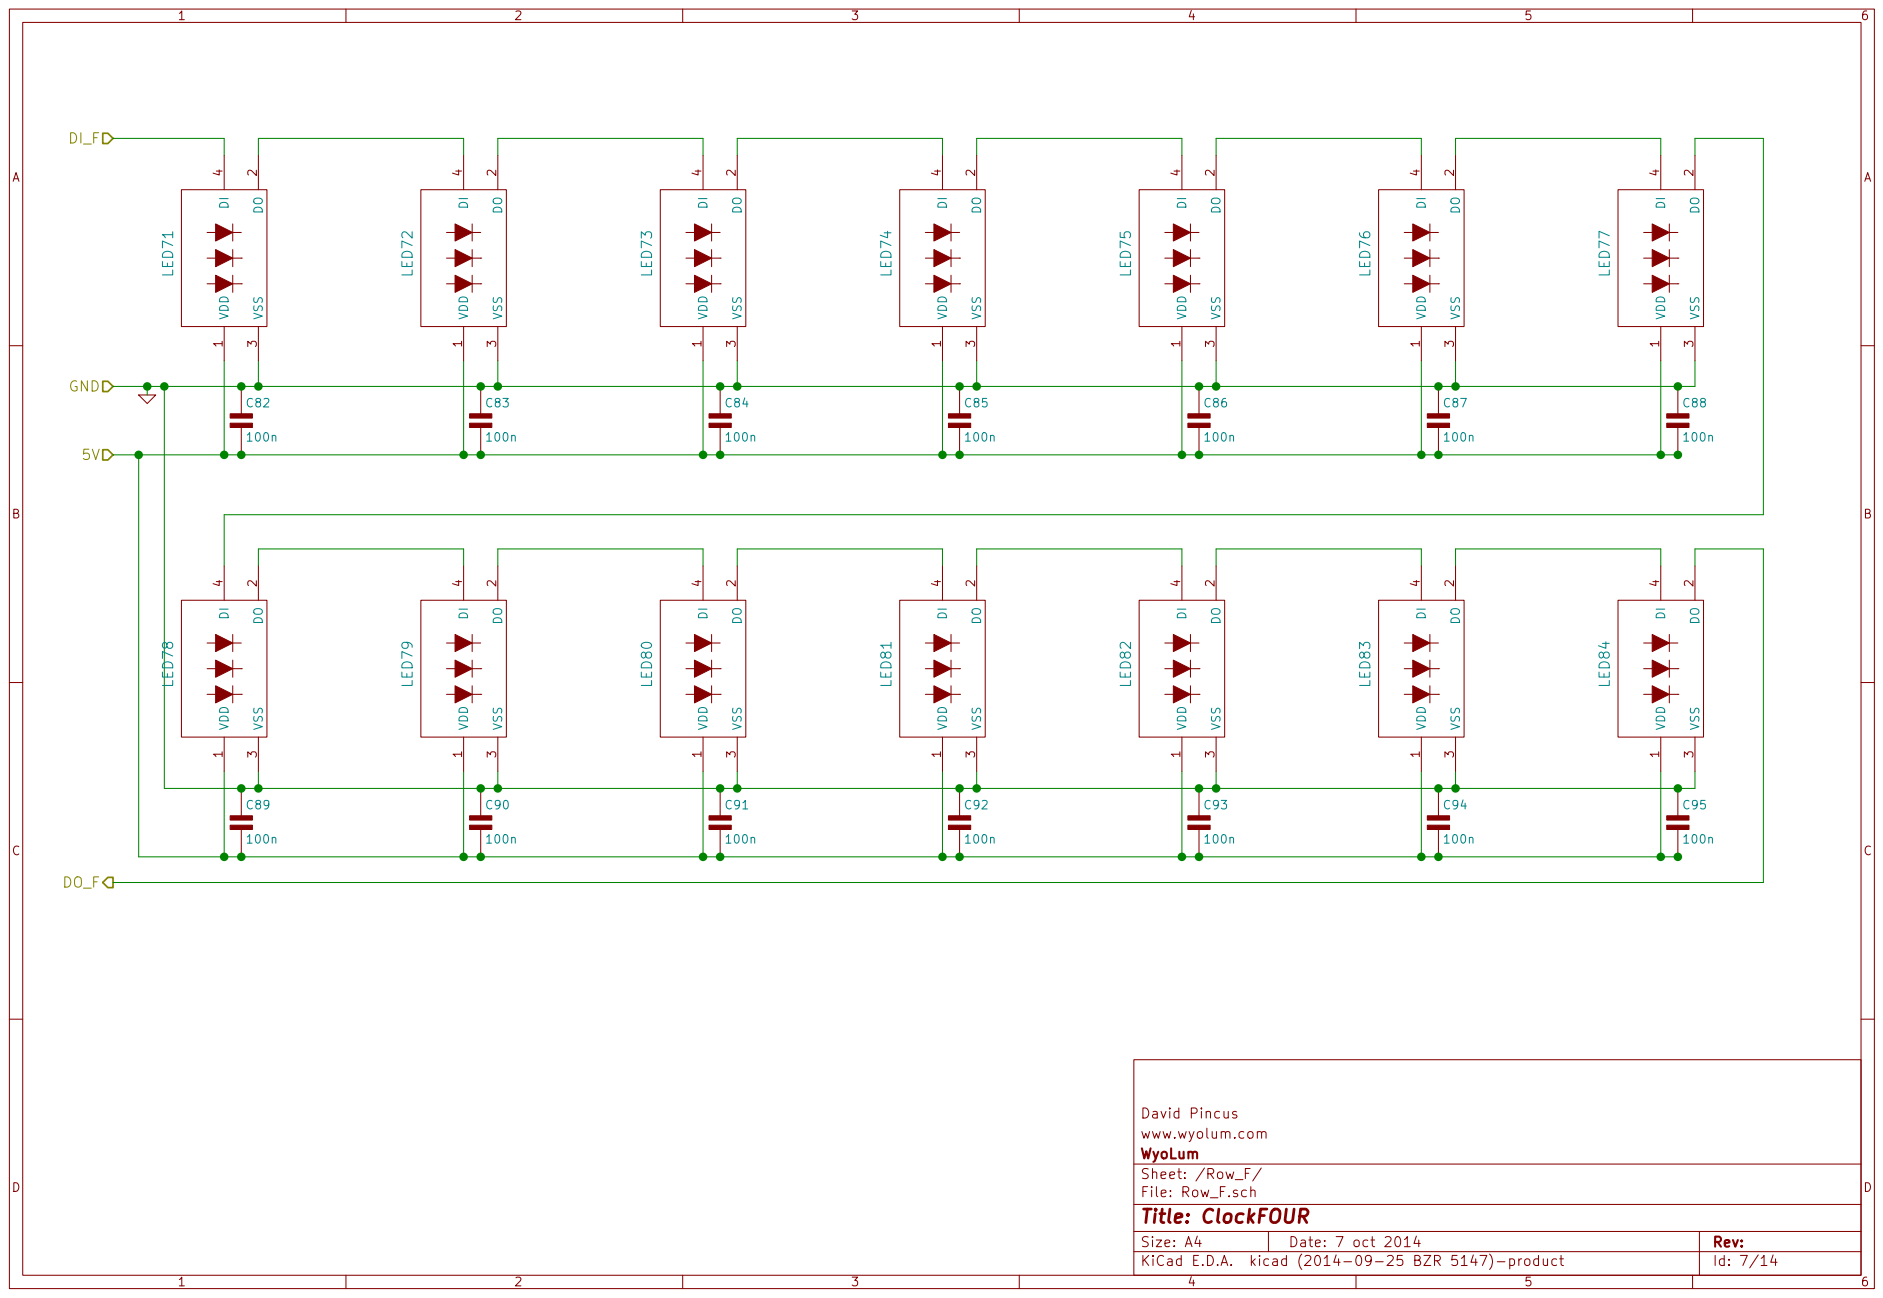
[picture p80: page 7]

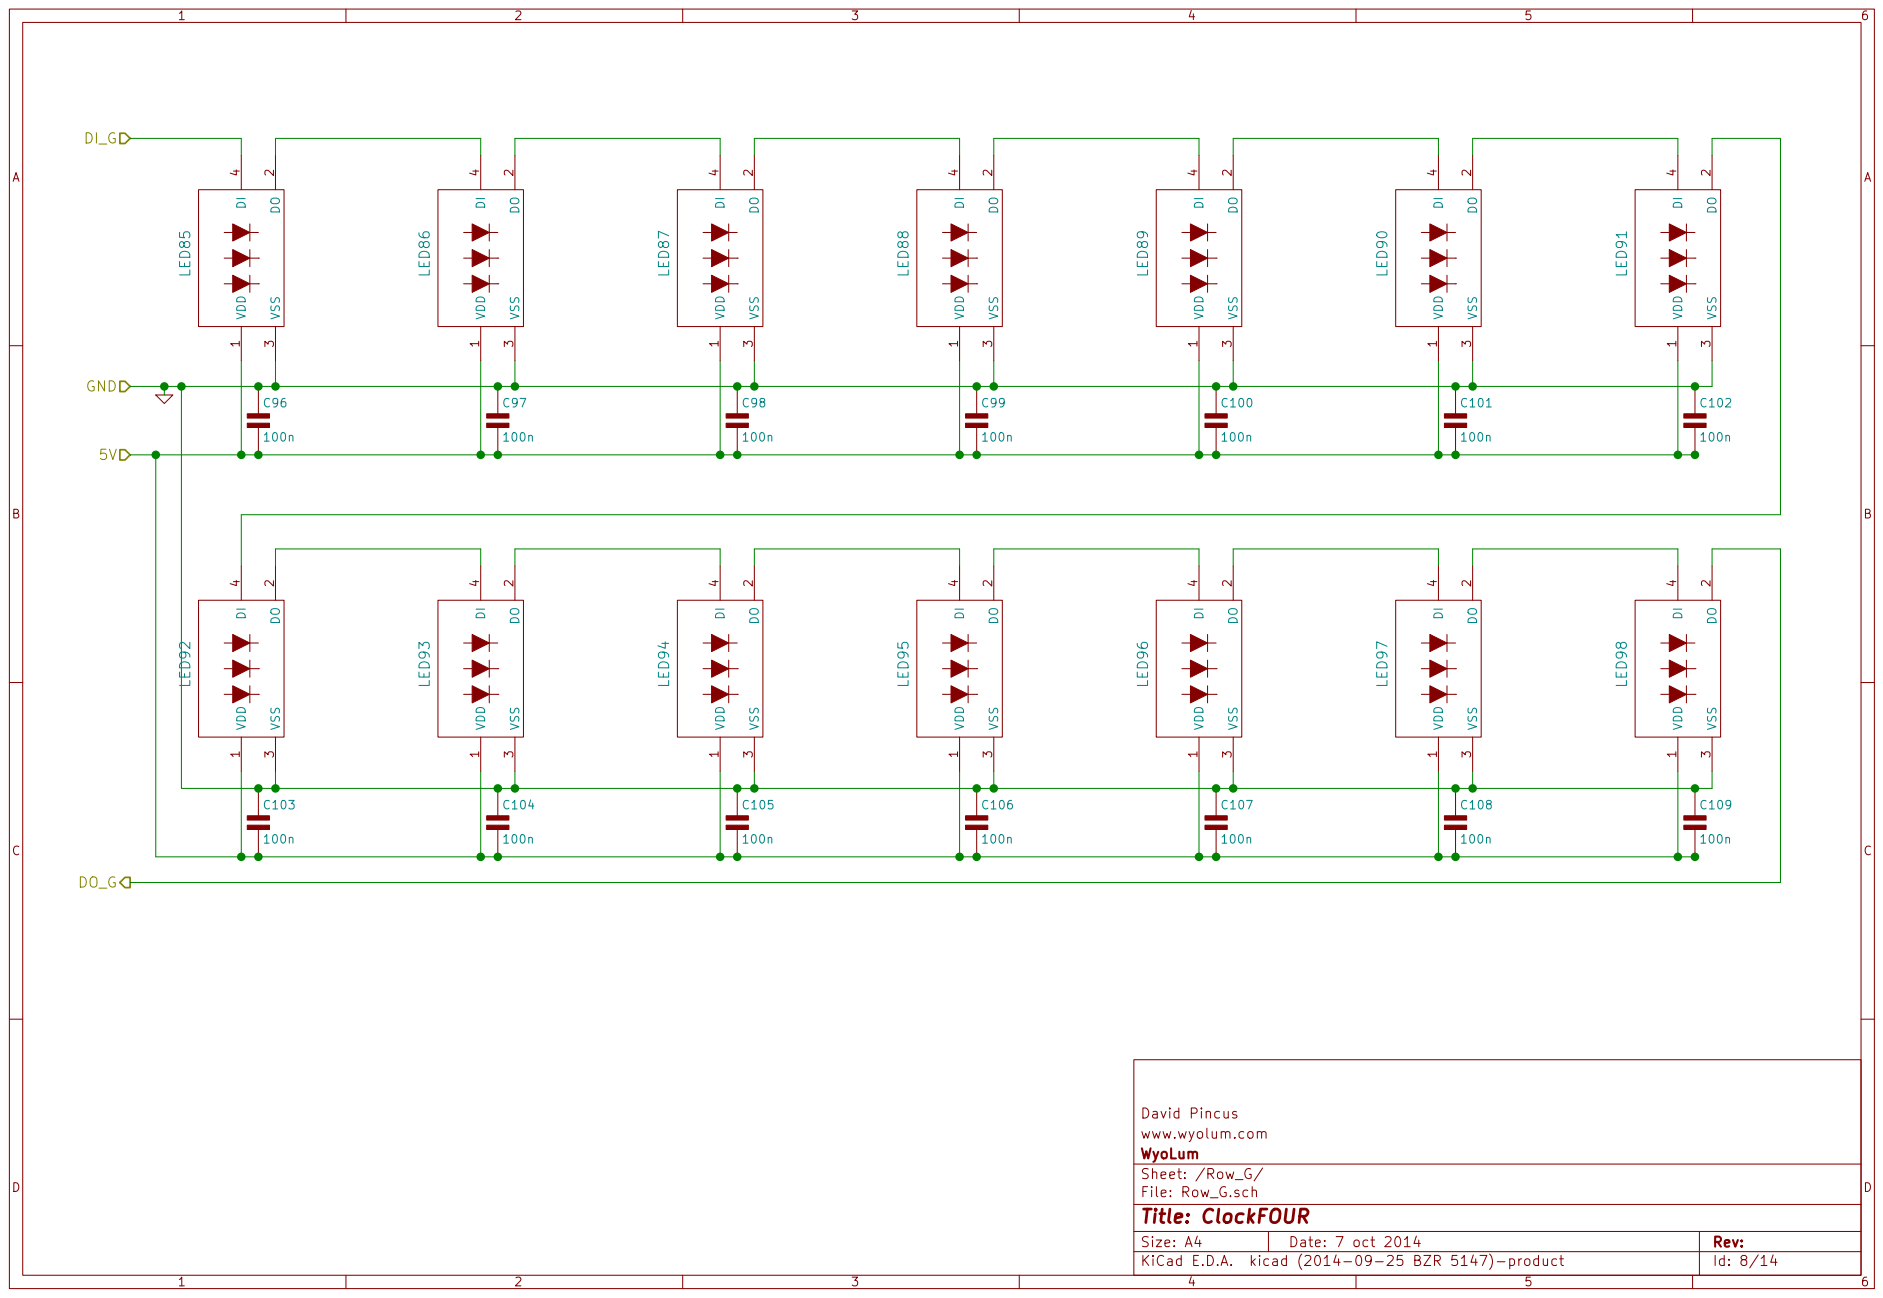
[picture p81: page 8]

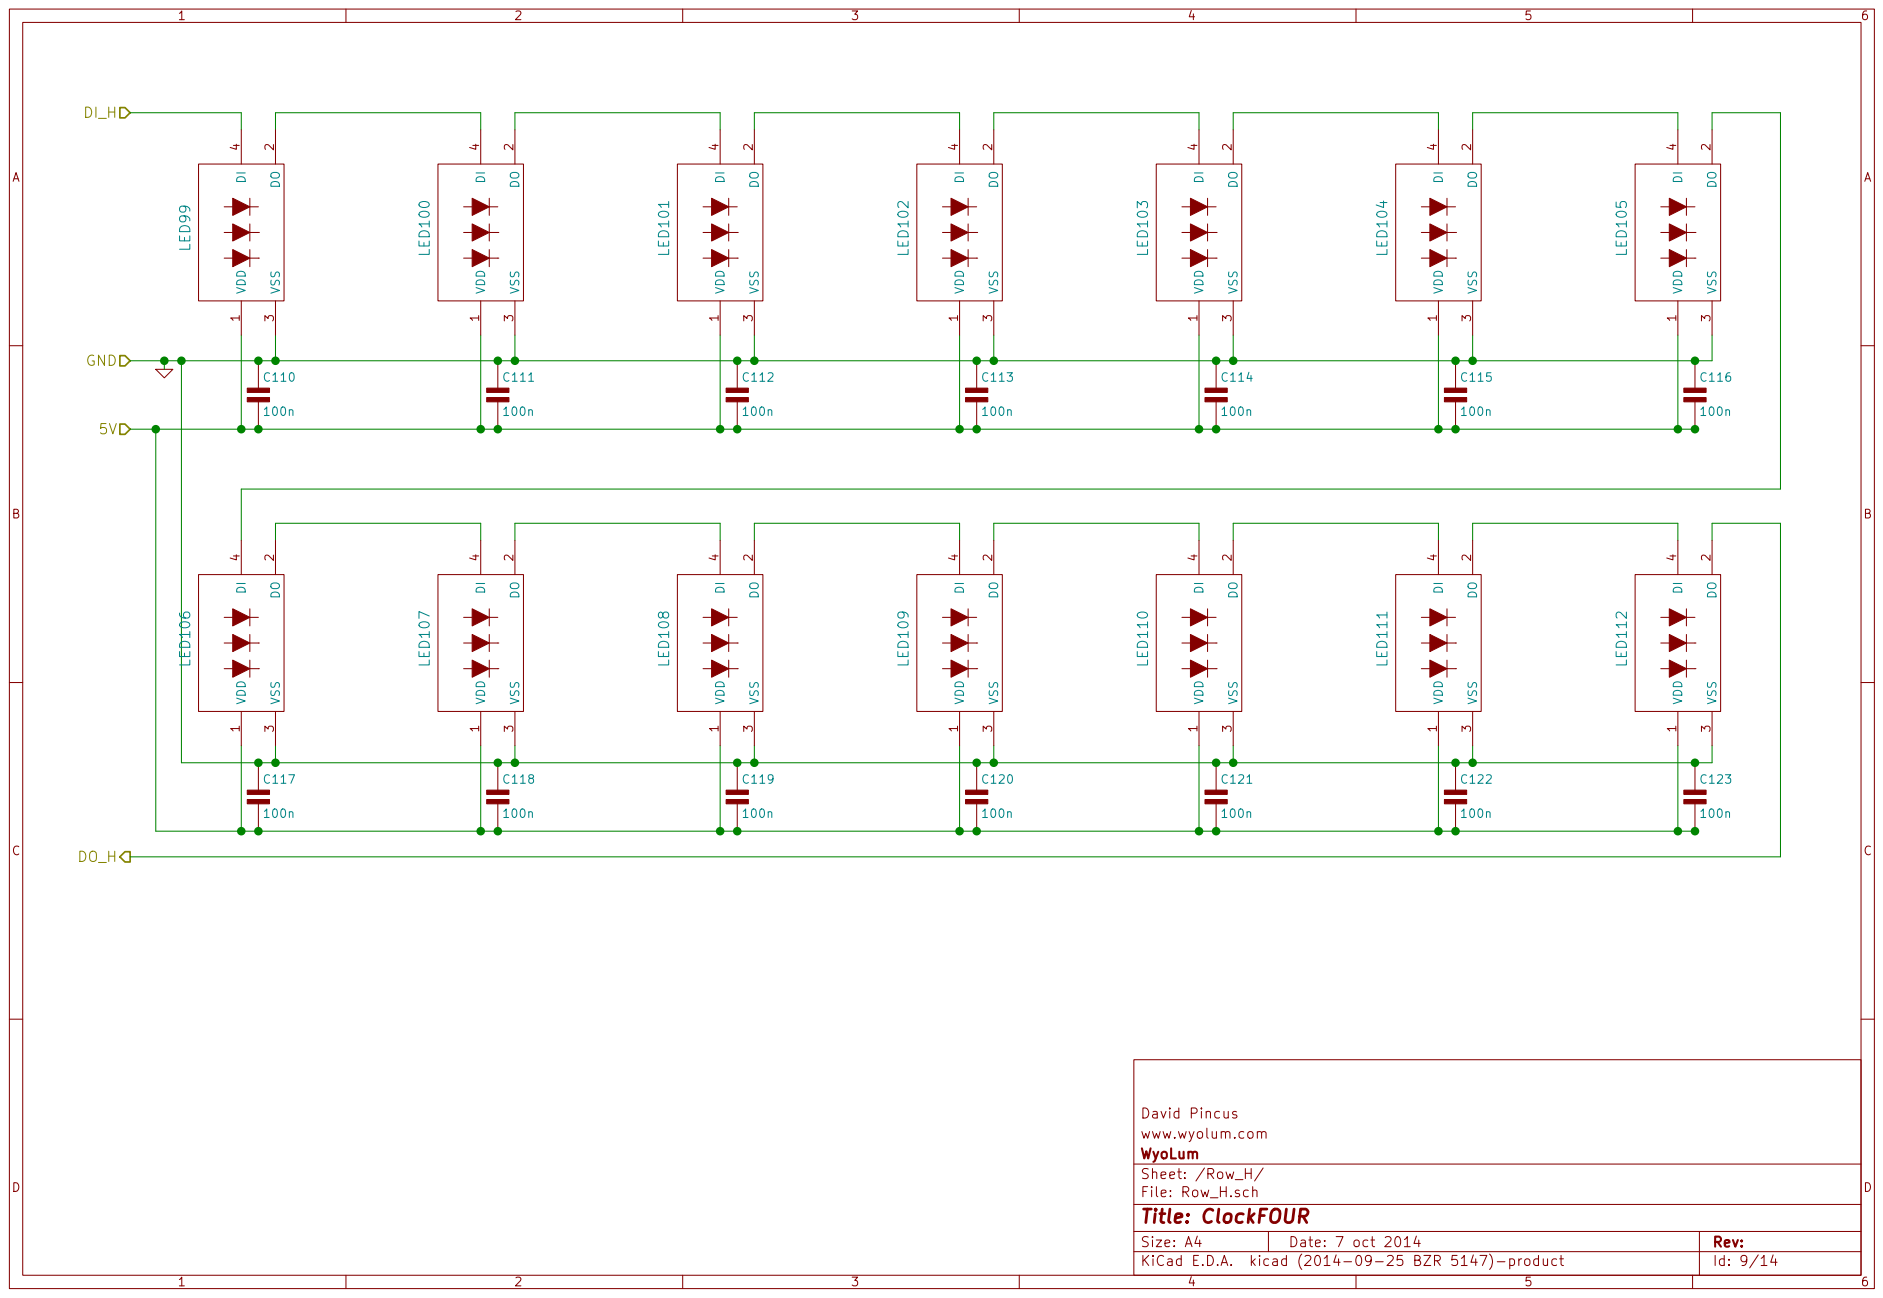
[picture p82: page 9]

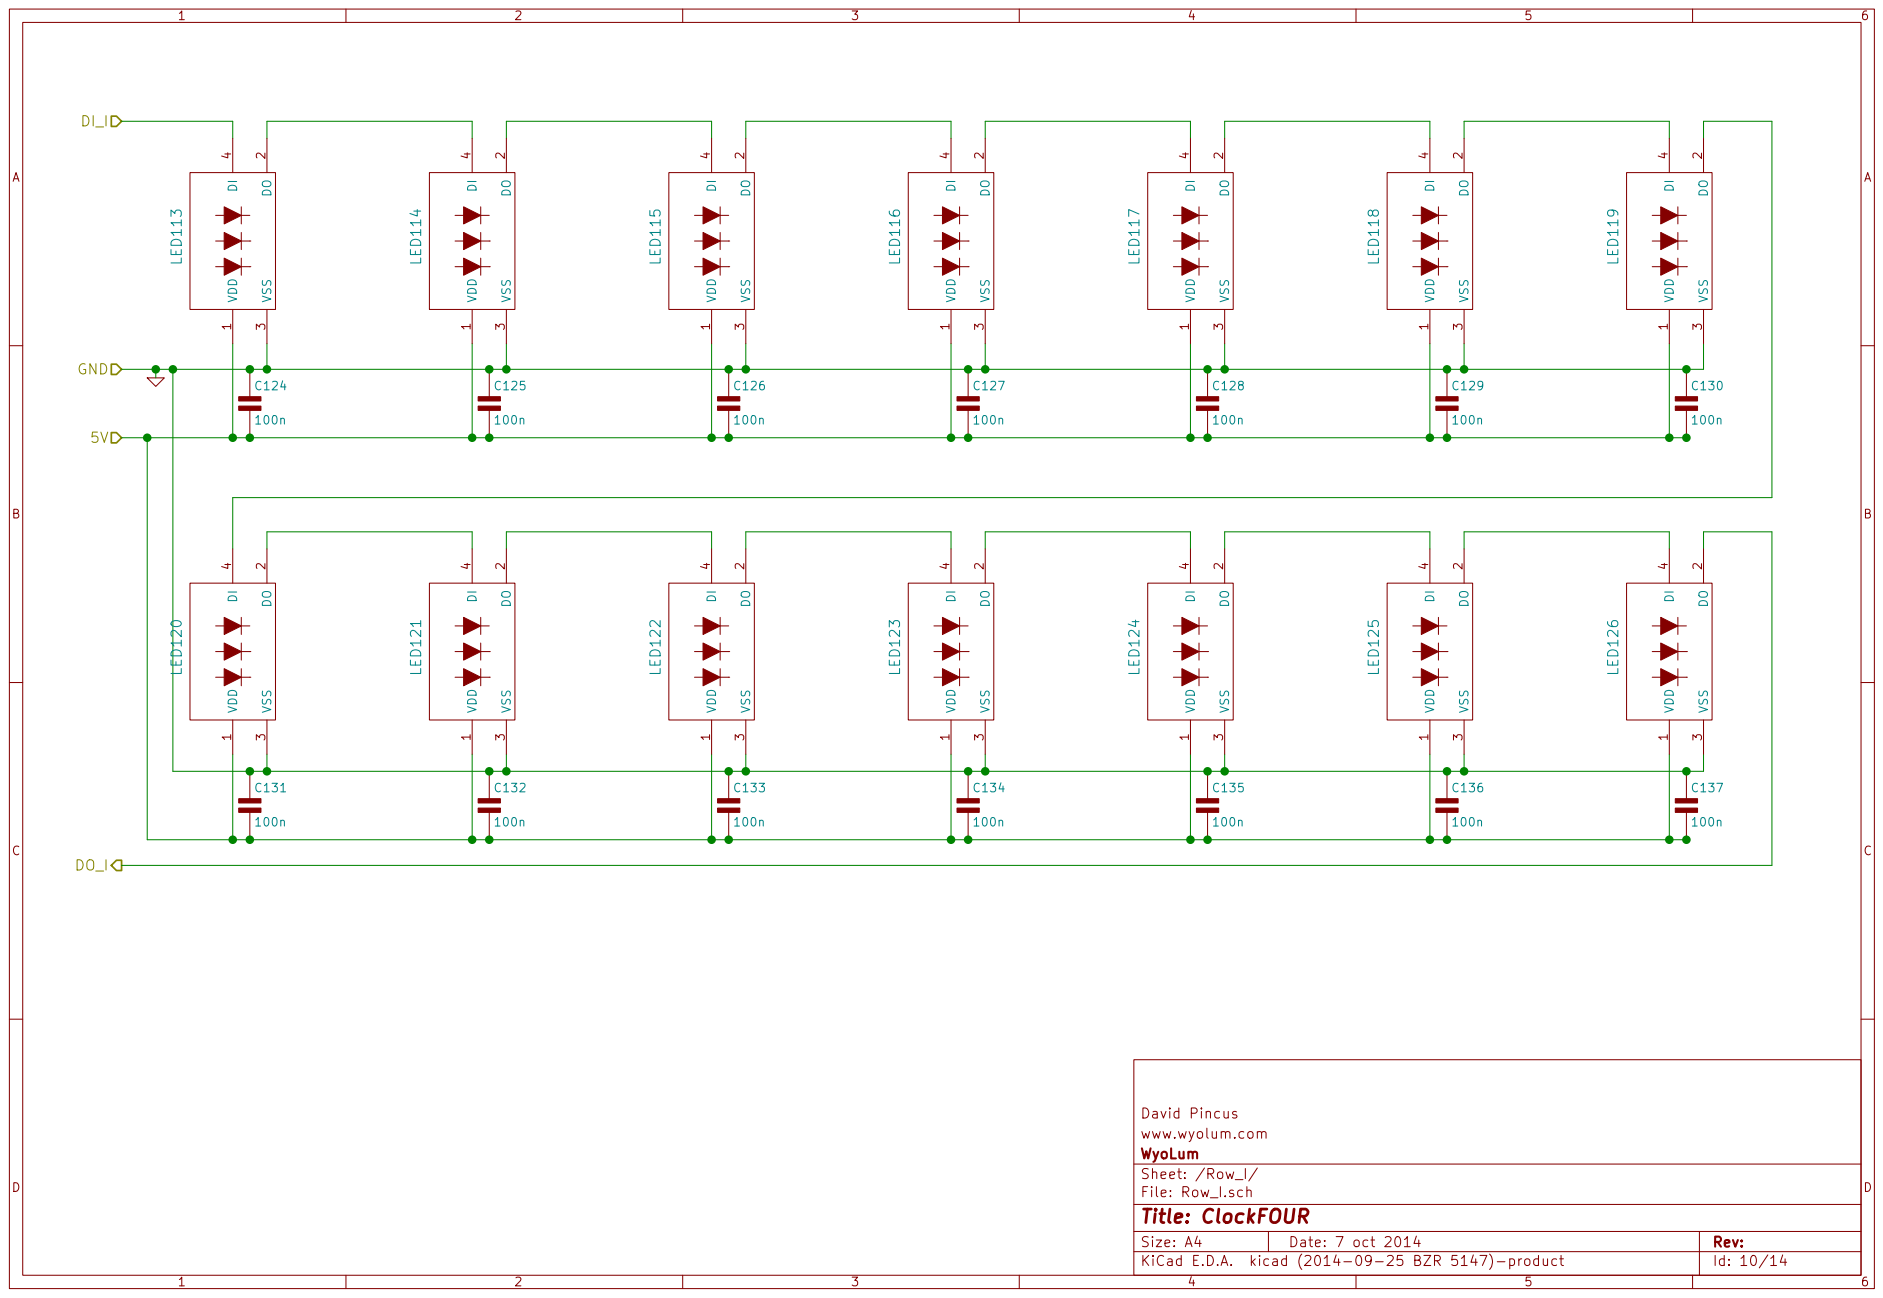
[picture p83: page 10]

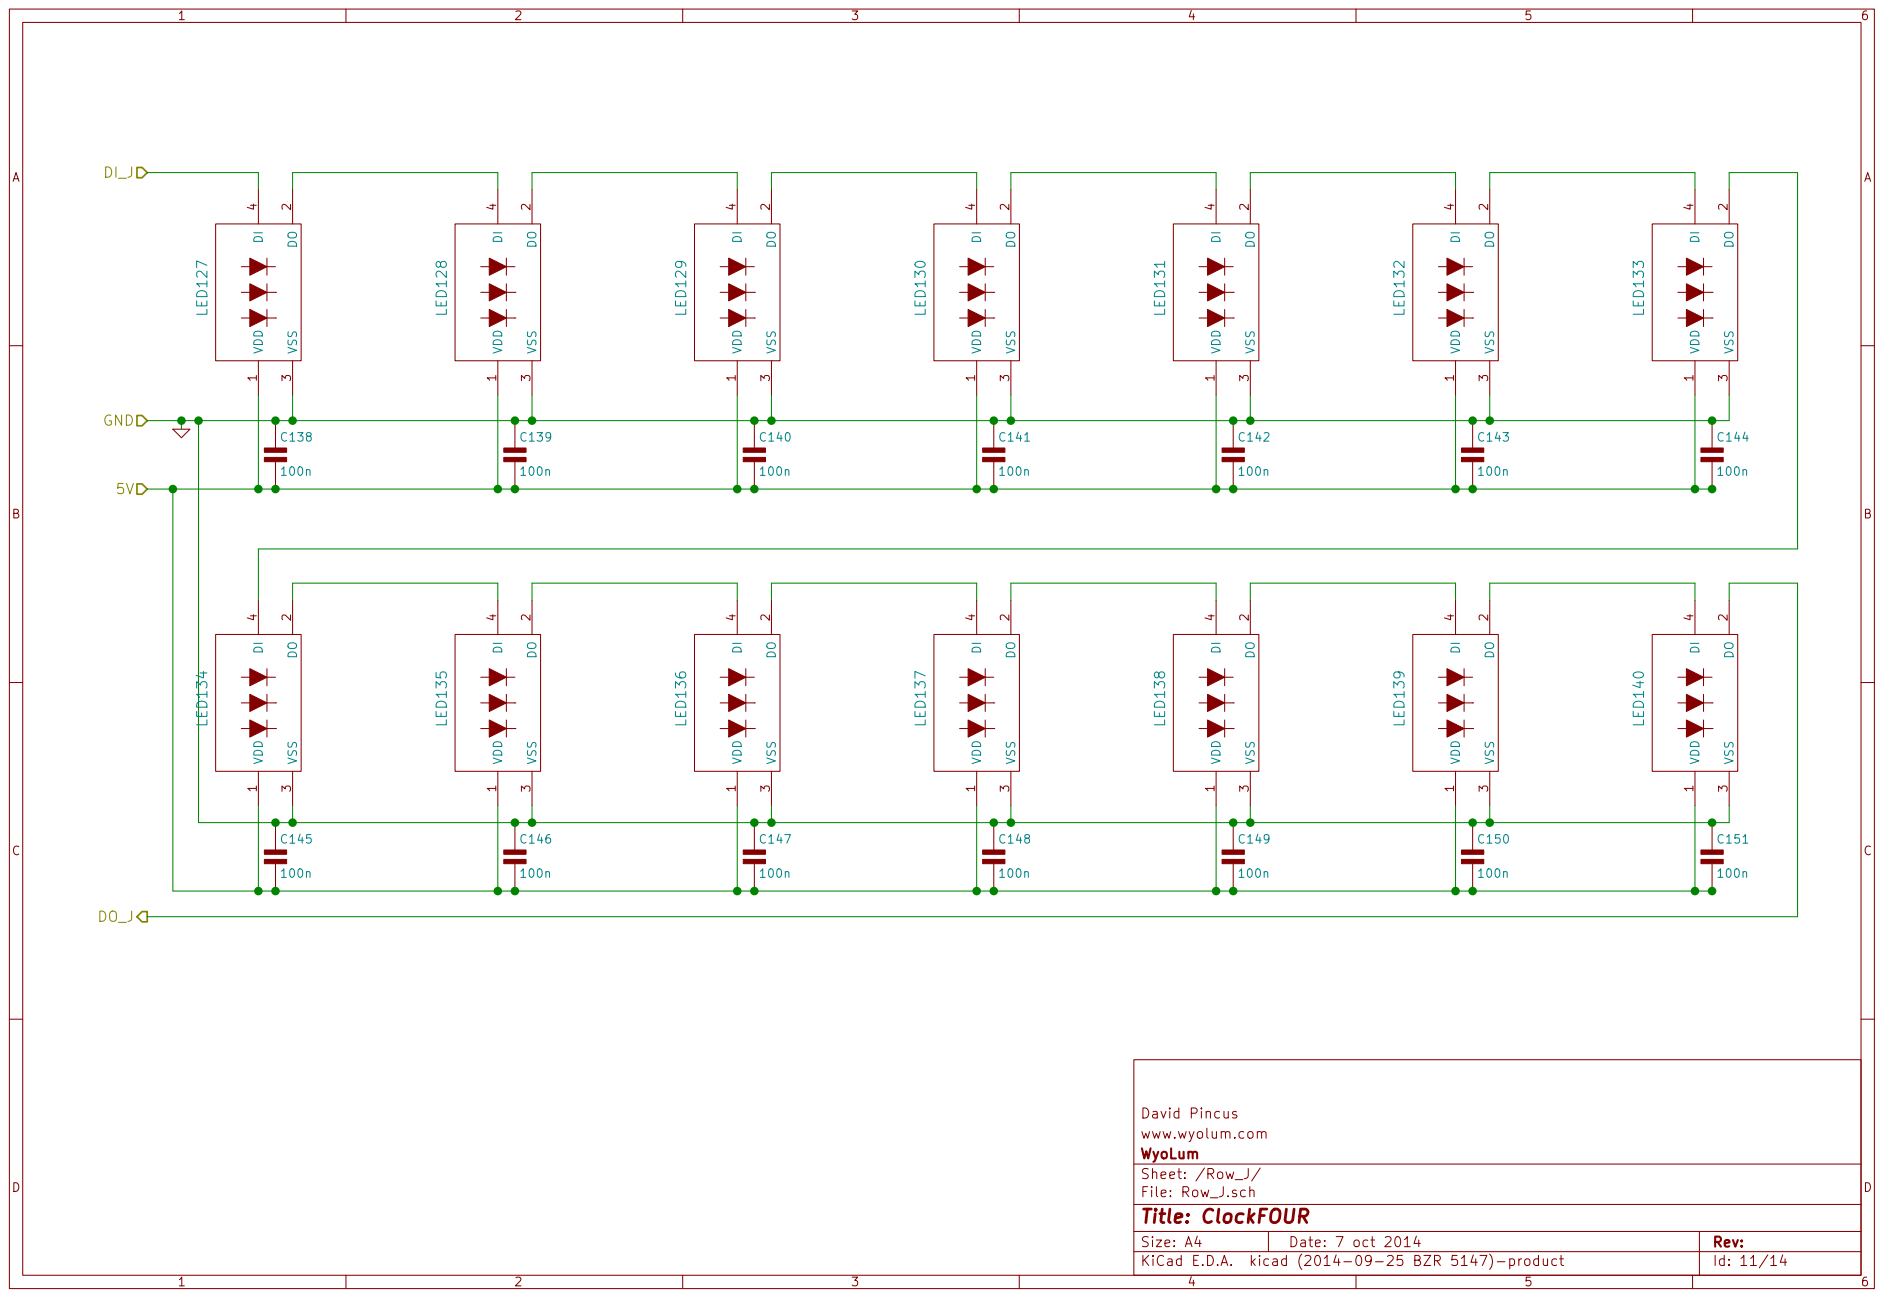
[picture p84: page 11]

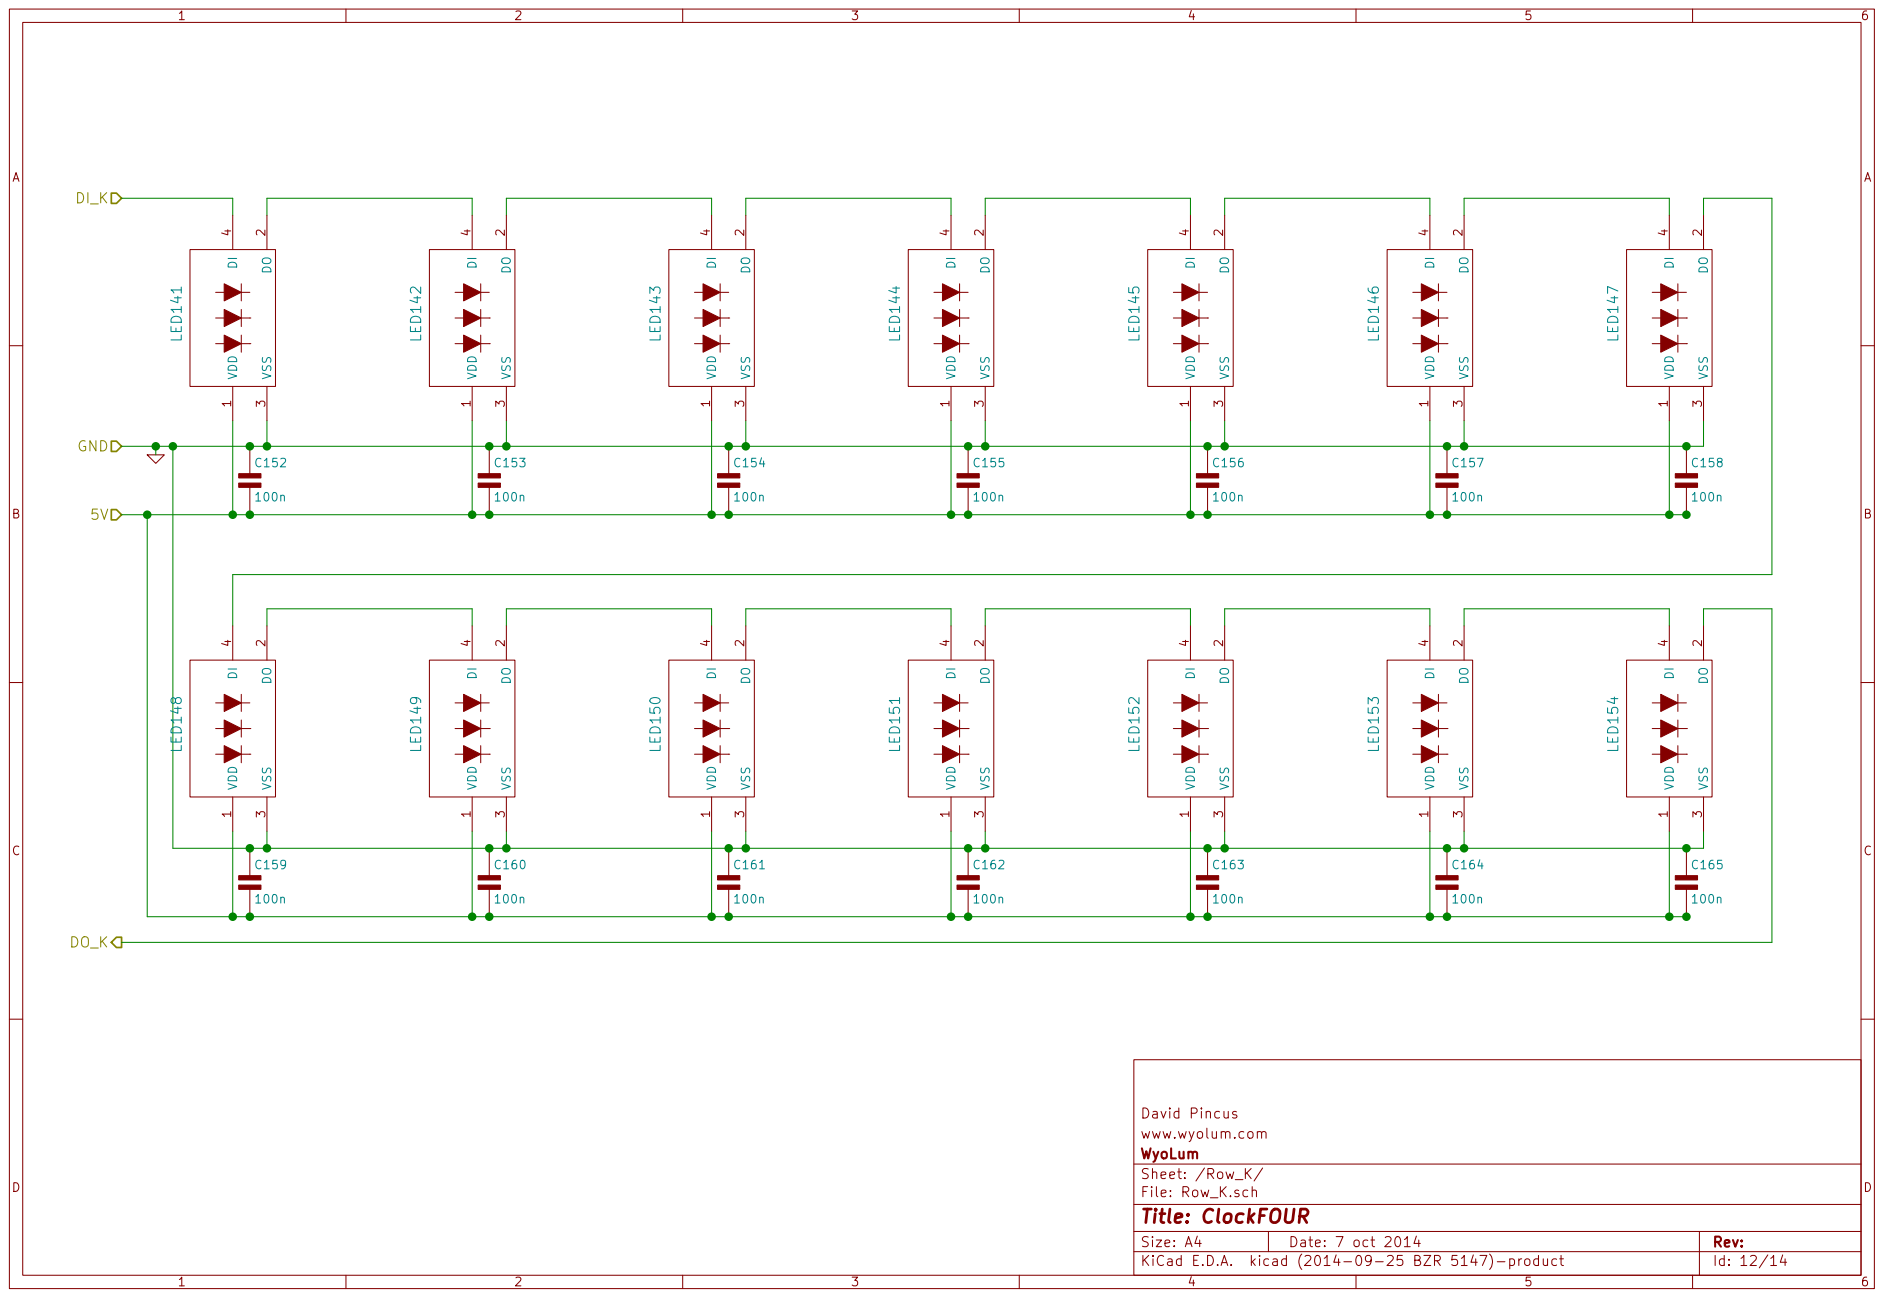
[picture p85: page 12]

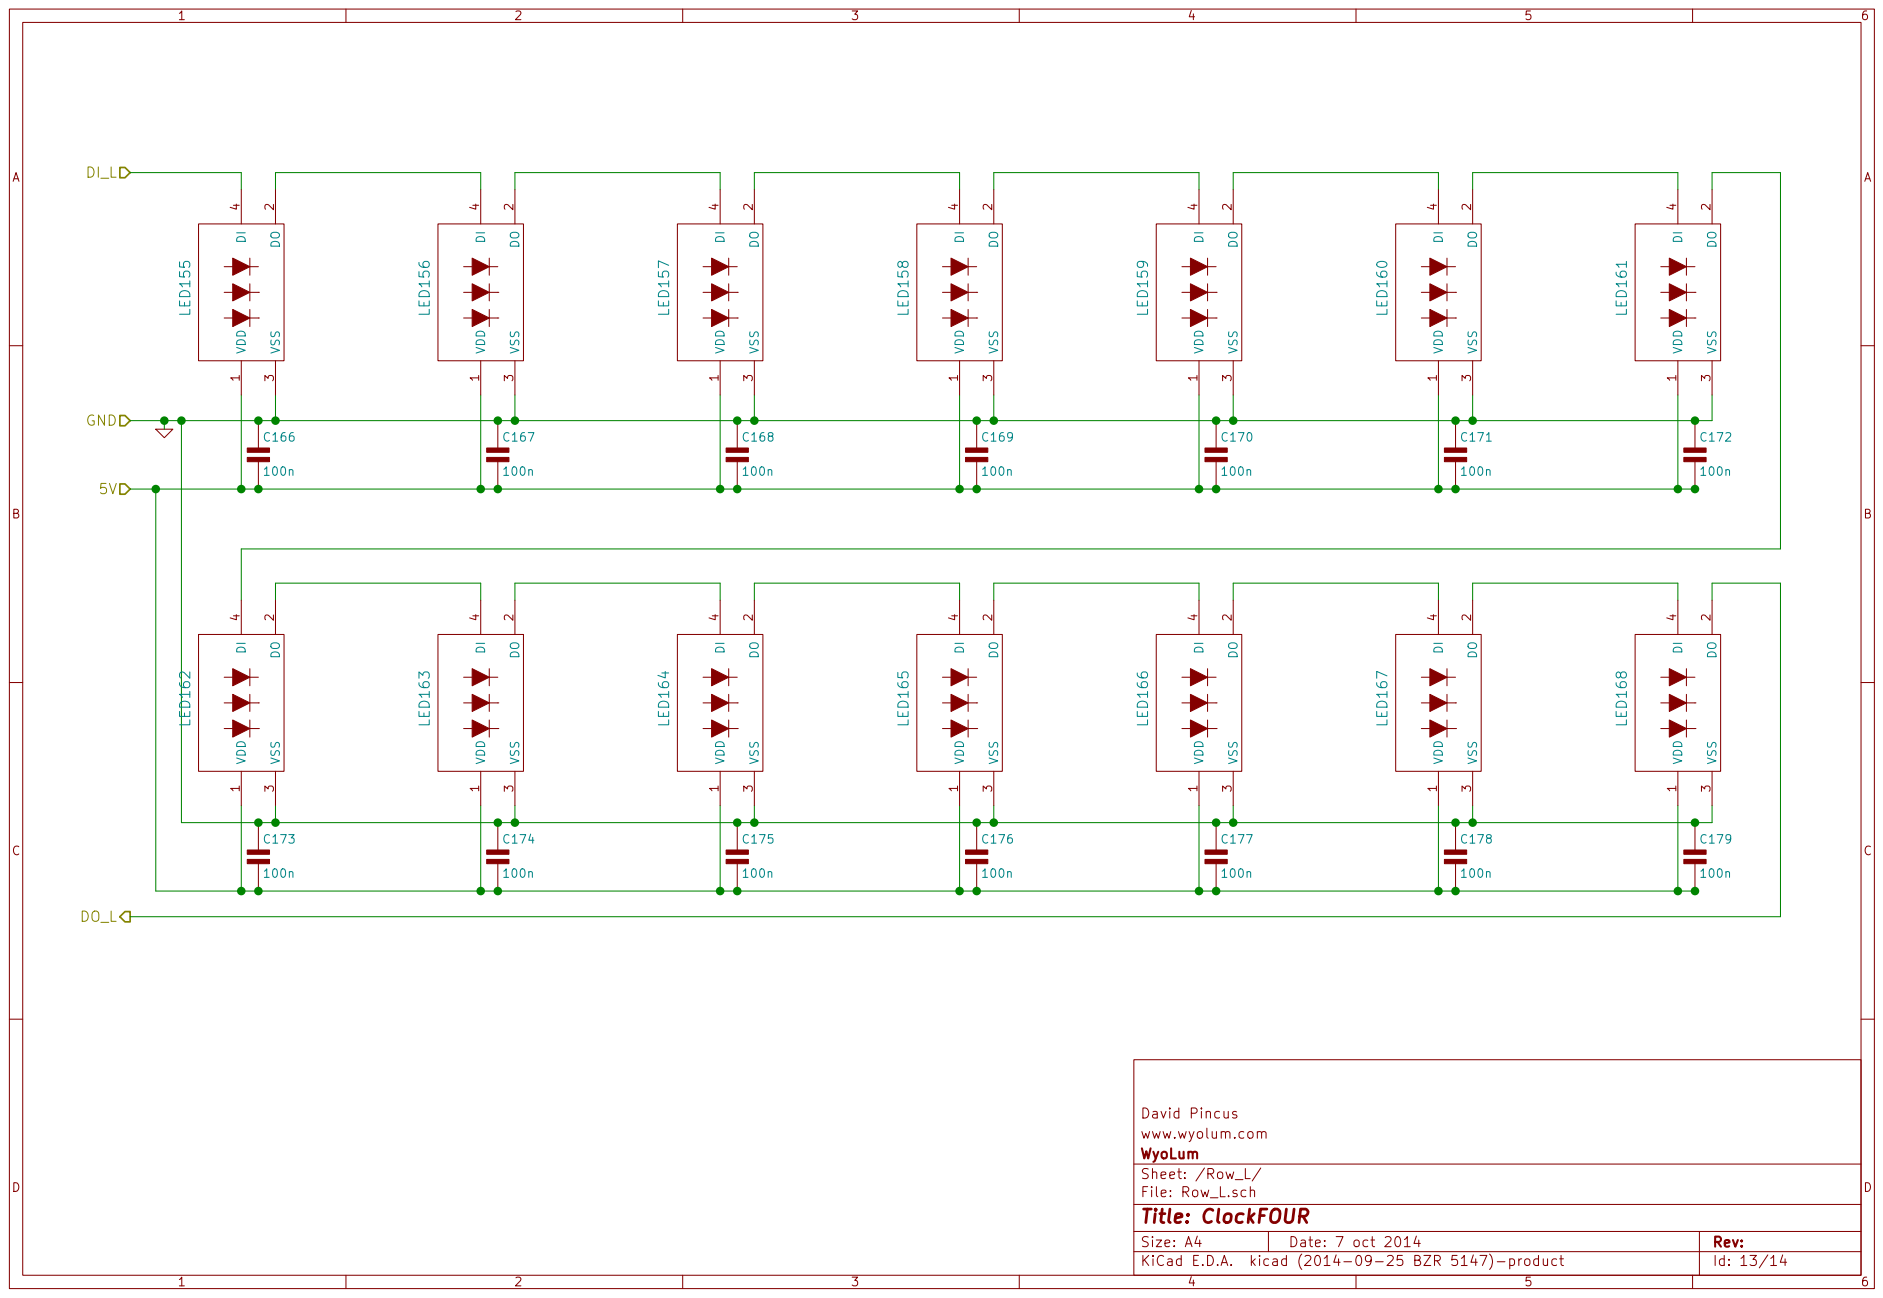
[picture p86: page 13]

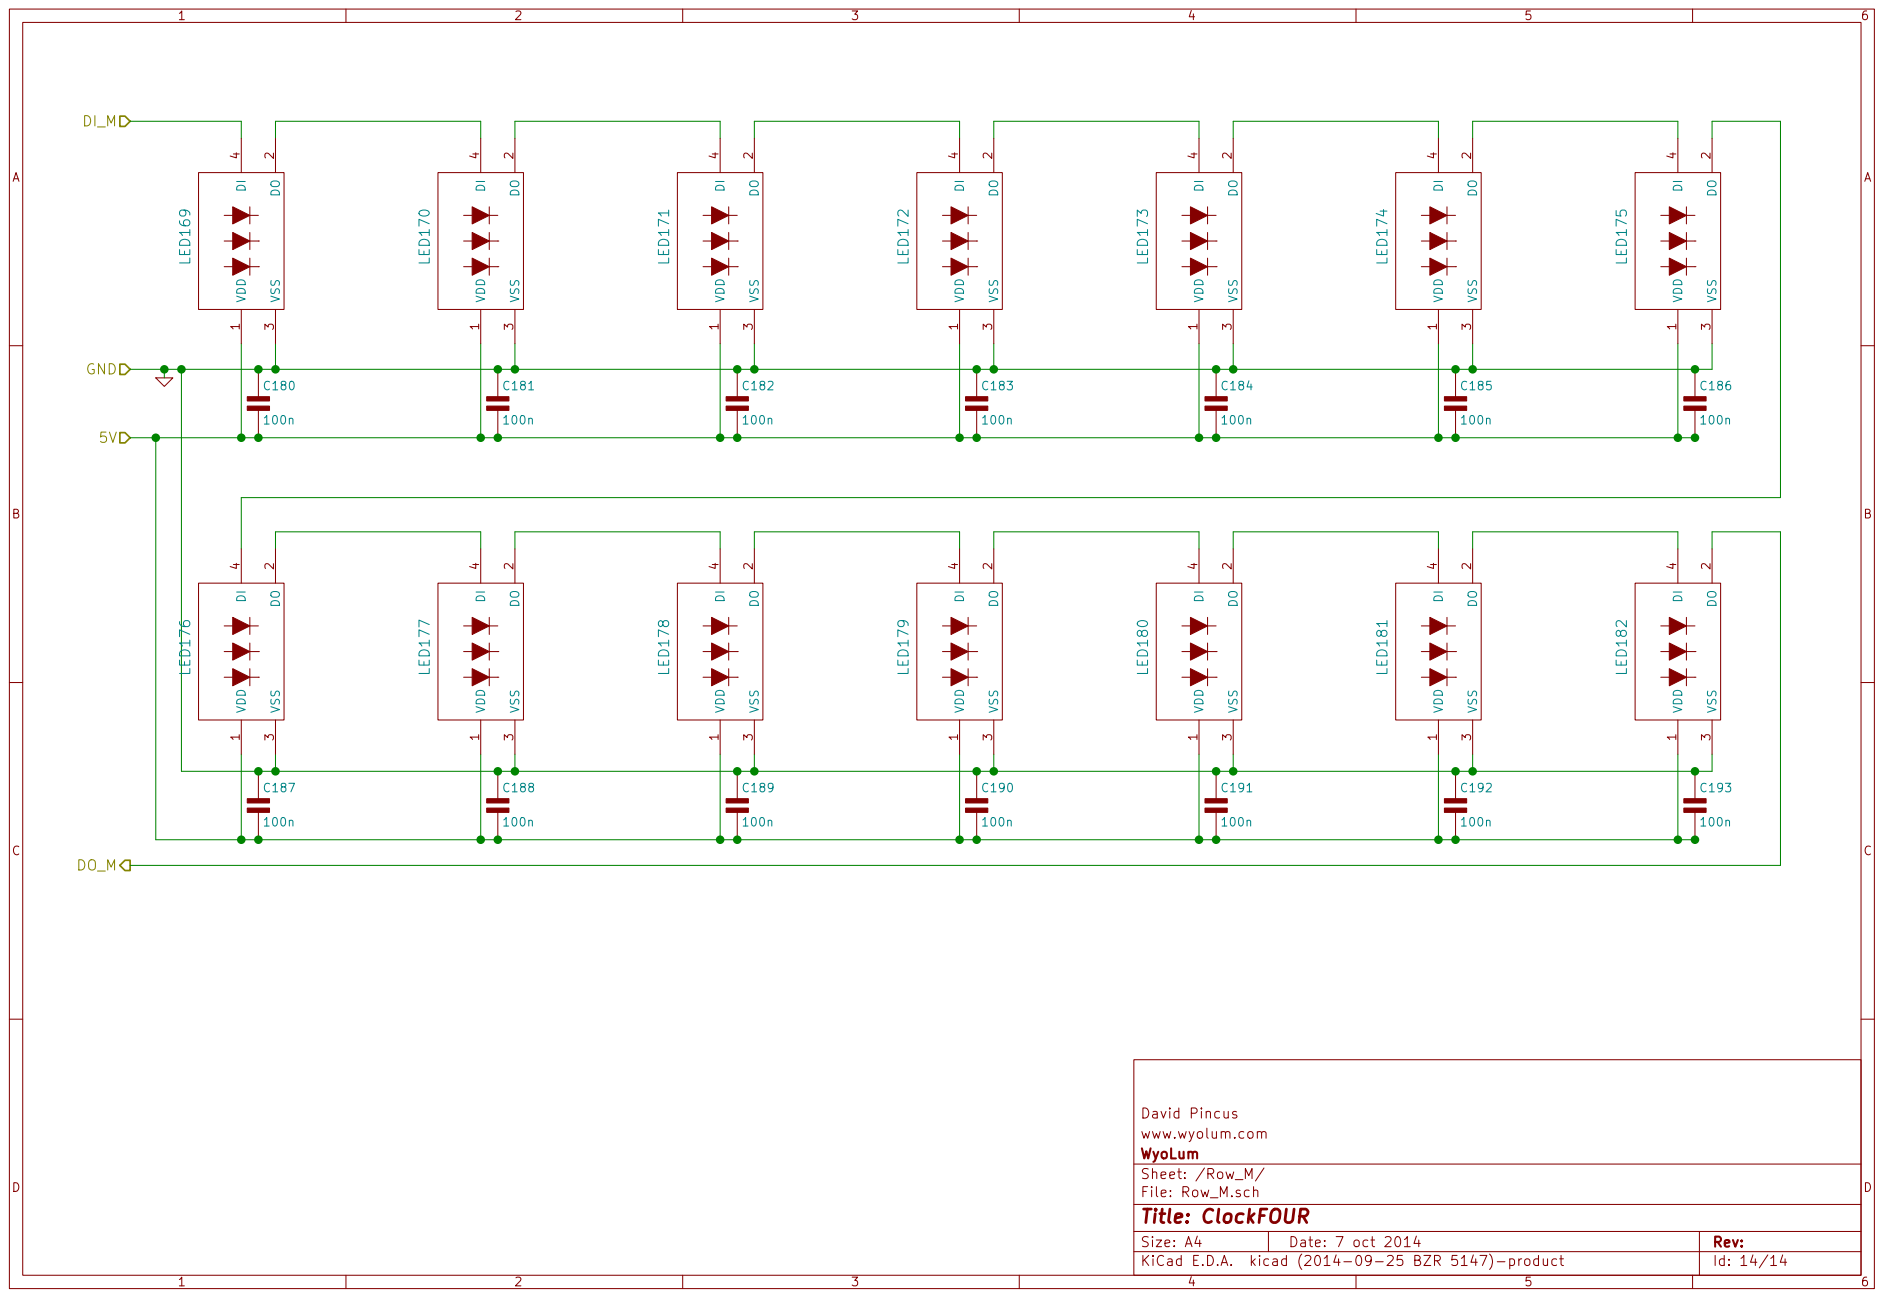
[picture p87: page 14]
