wyolum/ClockFOUR/KiCad/C4_rev1/Gerber/ClockFOUR-B_SilkS.pdf

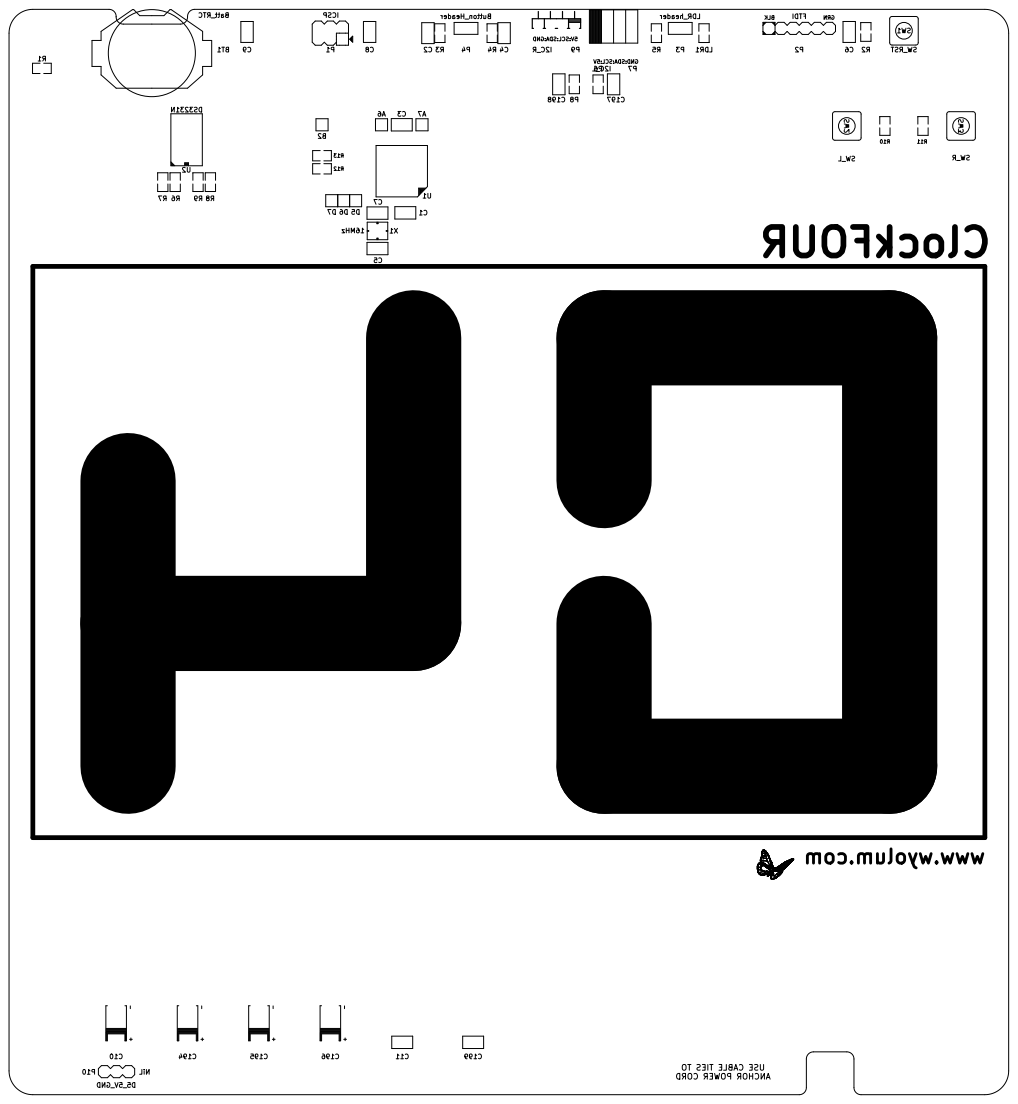
[picture p88: page 1]

5V:SCL:SDA:GND ClockFOUR

USE CABLE TIES TO
