wyolum/ClockFOUR/fabricate/30x30 size/output/backplate_30_30_1.0.pdf

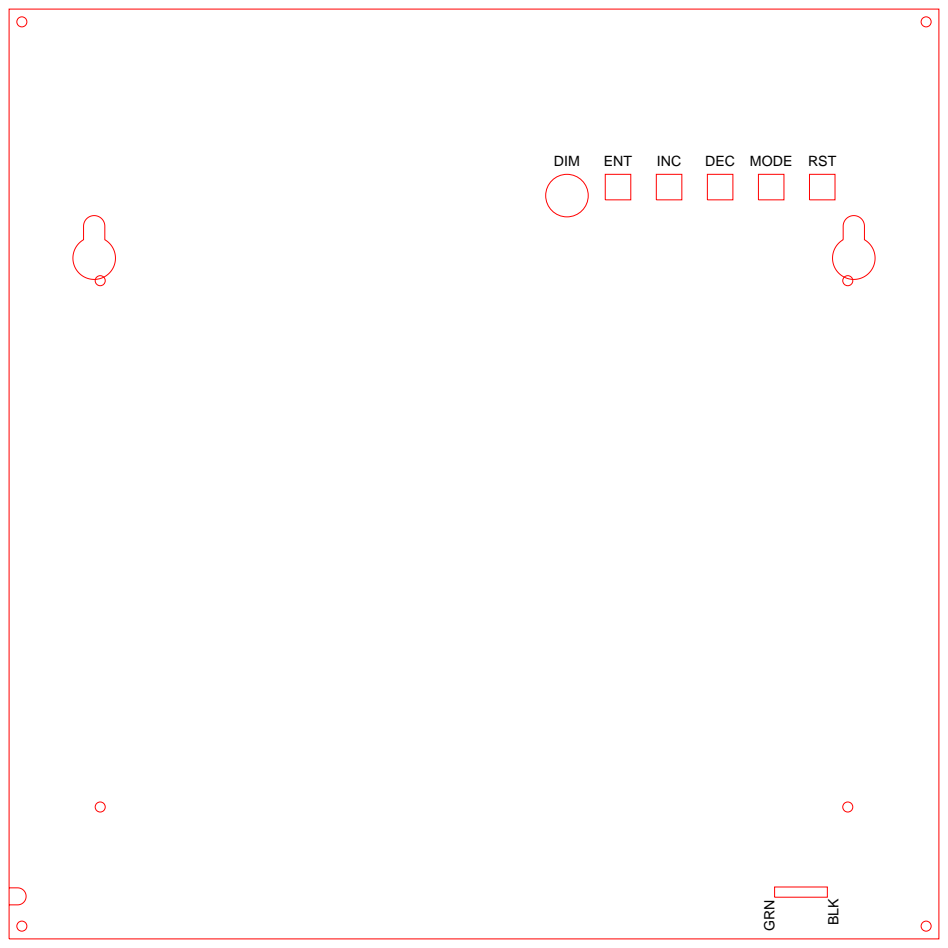
[picture p91: page 1]
DIM; ENT; INC; DEC MODE RST GRN; BLK
