wyolum/ClockFOUR/KiCad_bak/pdf/ClockFOUR-B_Cu.pdf

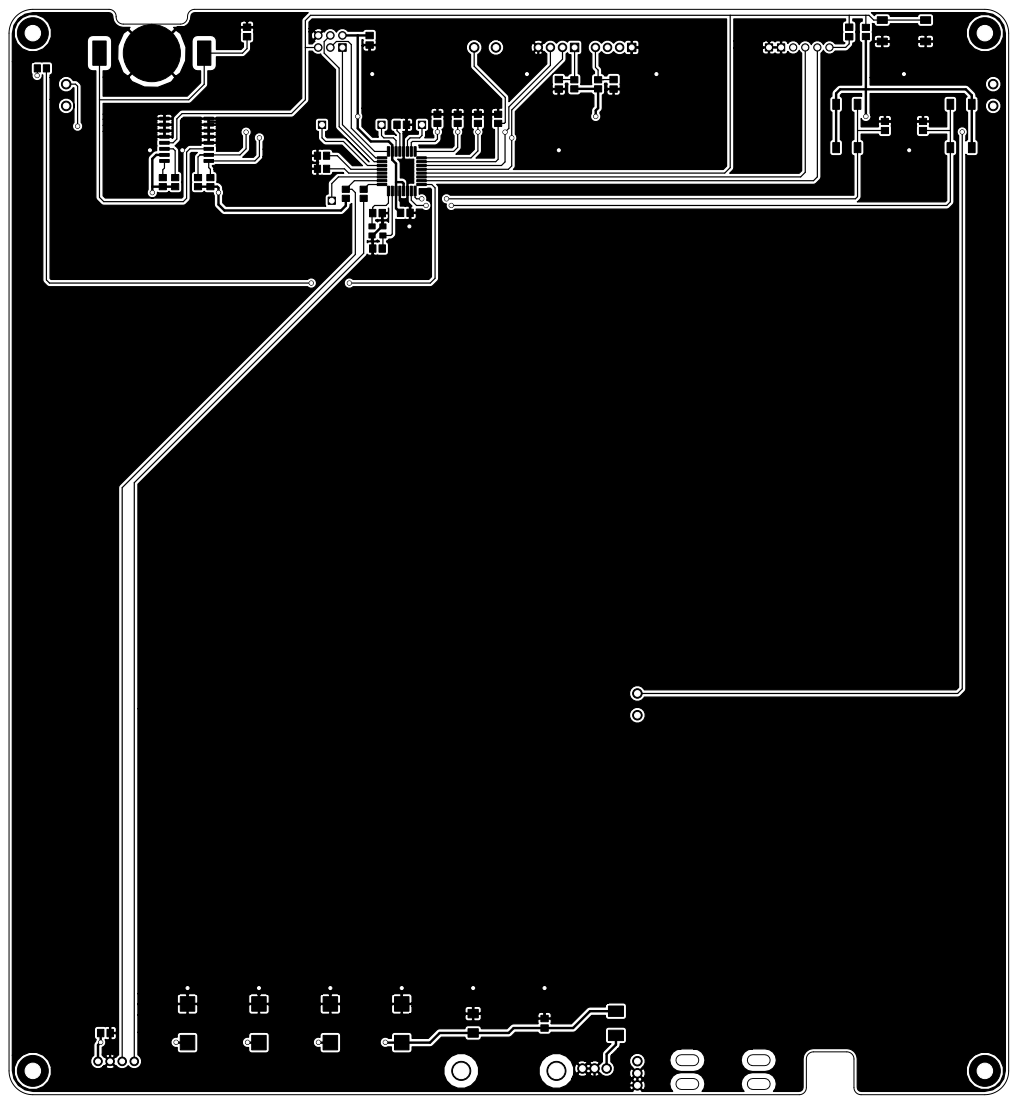
[picture p92: page 1]
