wyolum/ClockFOUR/KiCad_bak/pdf/ClockFOUR-Dwgs_User.pdf

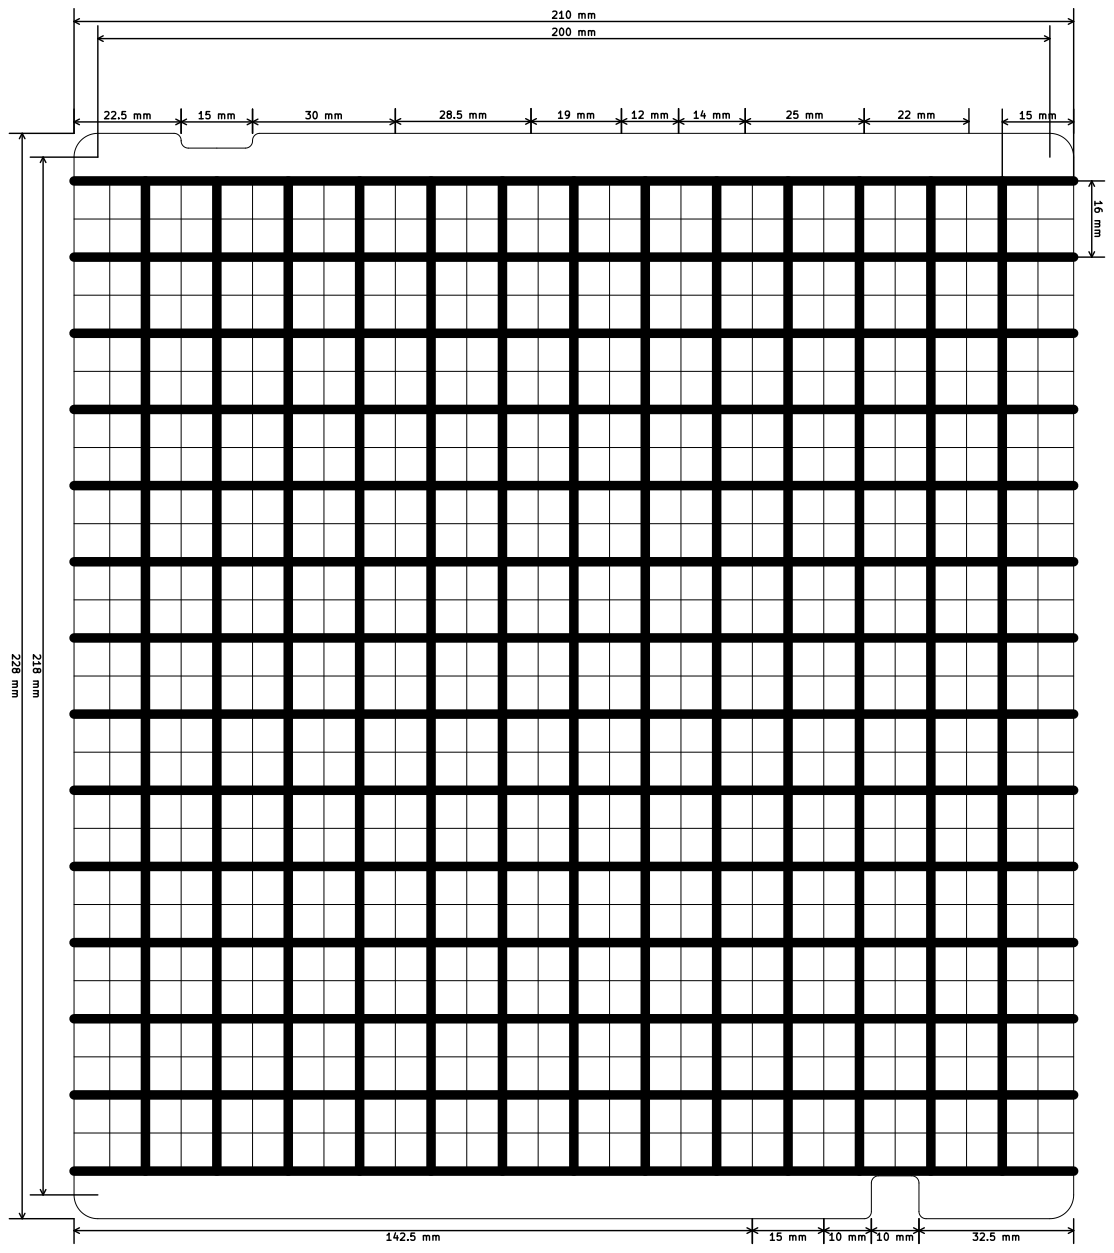
[picture p93: page 1]
