wyolum/ClockFOUR/KiCad_bak/pdf/ClockFOUR-F_Cu.pdf

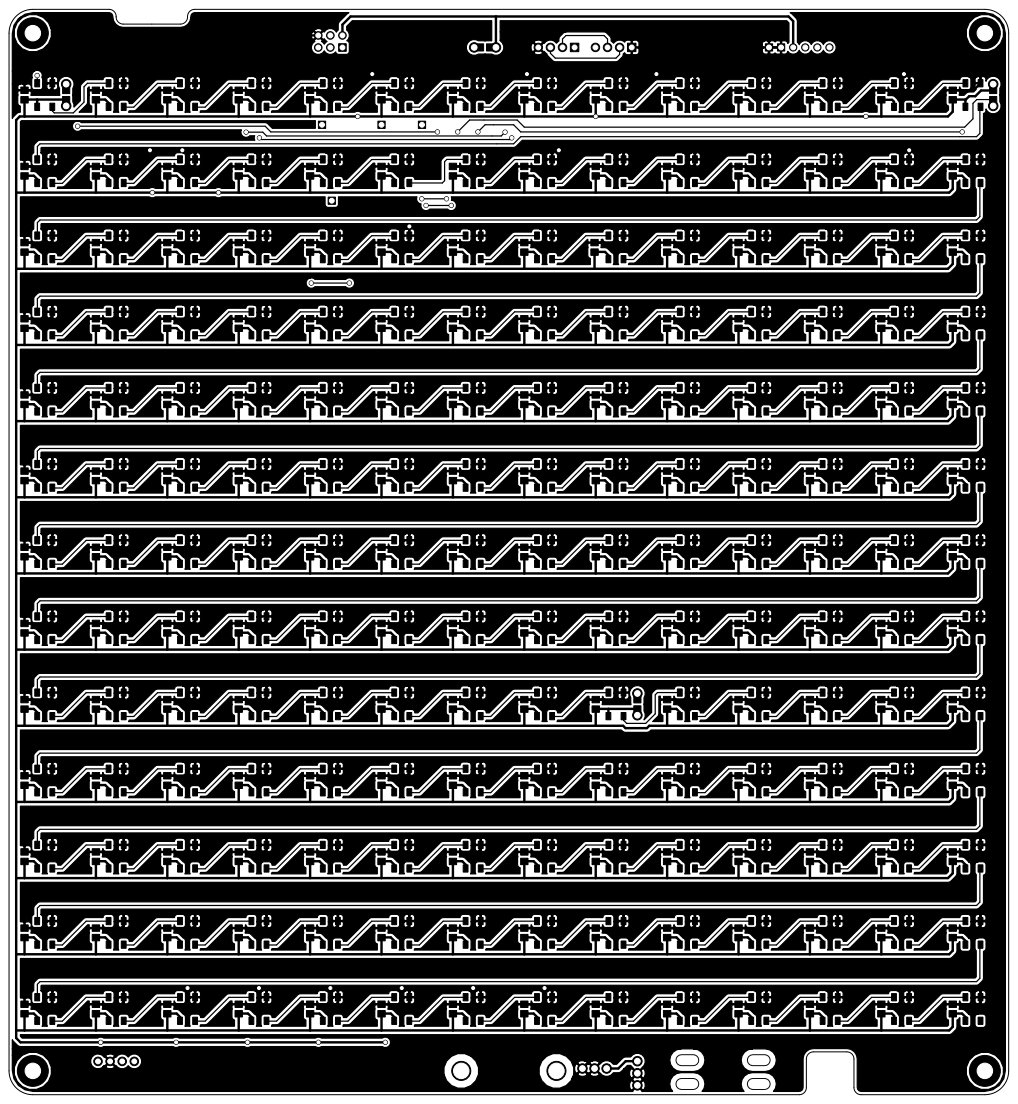
[picture p94: page 1]
