wyolum/ClockFOUR/KiCad_bak/pdf/ClockFOUR-F_SilkS.pdf

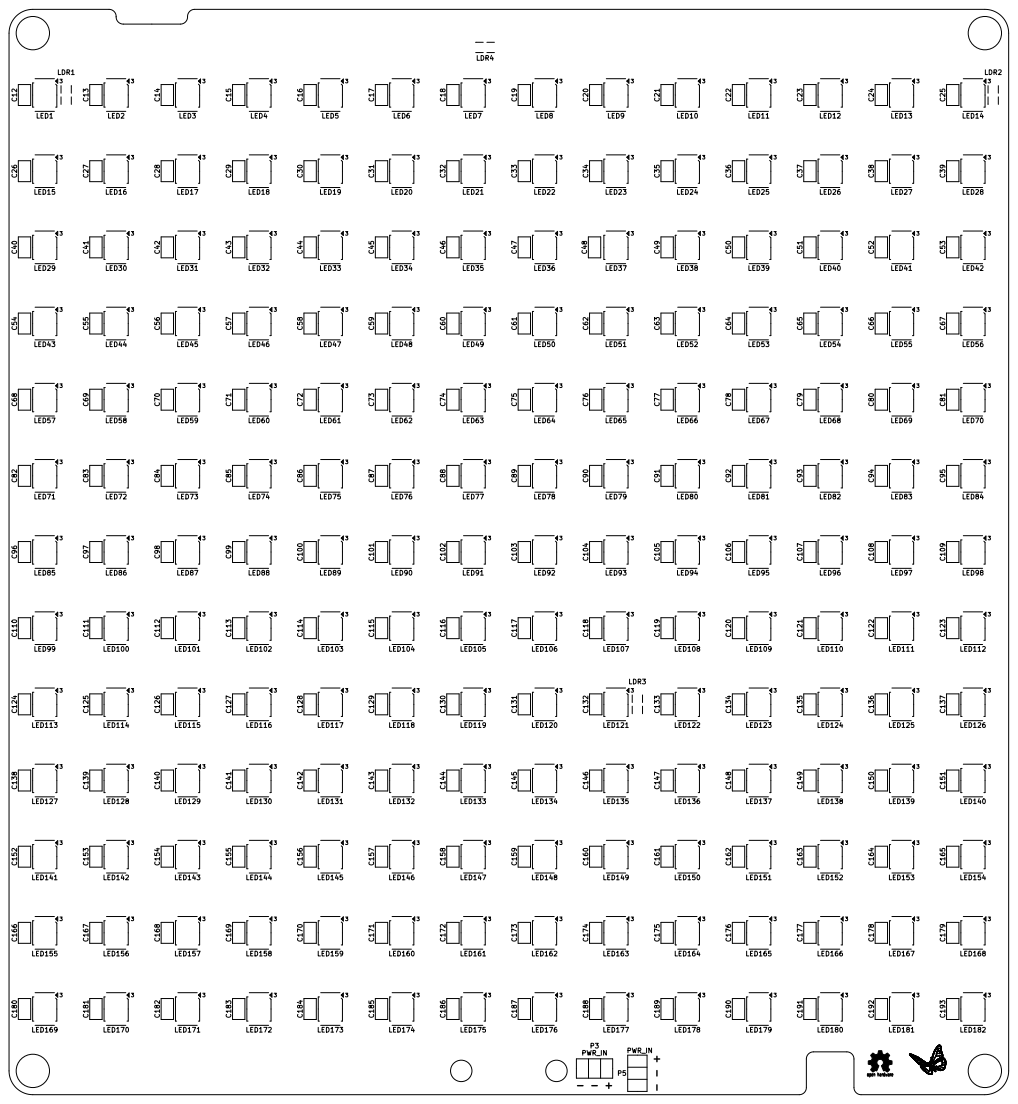
[picture p95: page 1]
