wyolum/ClockFOUR/KiCad/C4_rev1/Gerber/ClockFOUR-B_Cu.pdf

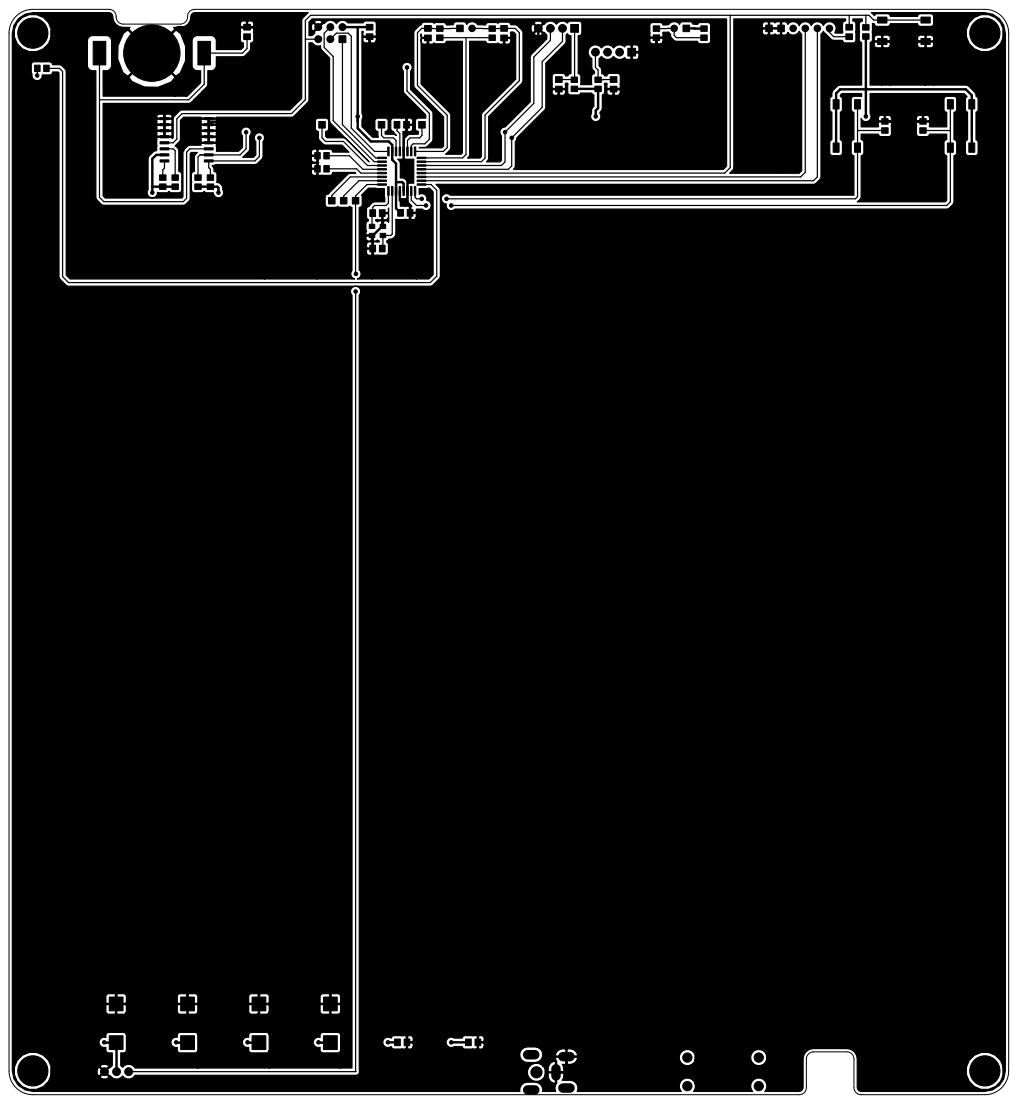
[picture p96: page 1]
