wyolum/ClockFOUR/KiCad/C4_rev1/Gerber/ClockFOUR-B_Mask.pdf

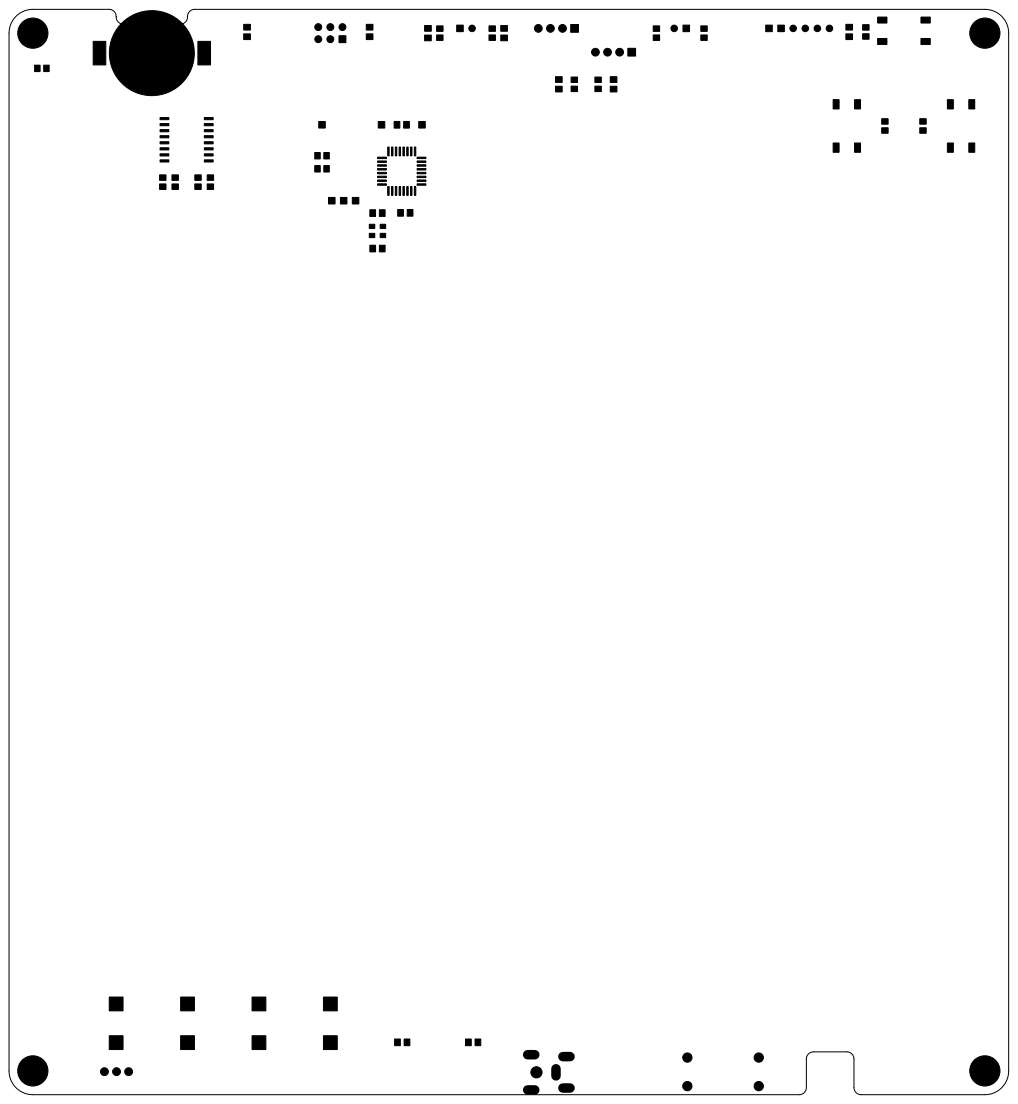
[picture p97: page 1]
