wyolum/ClockFOUR/KiCad/C4_rev1/Gerber/ClockFOUR-B_Paste.pdf

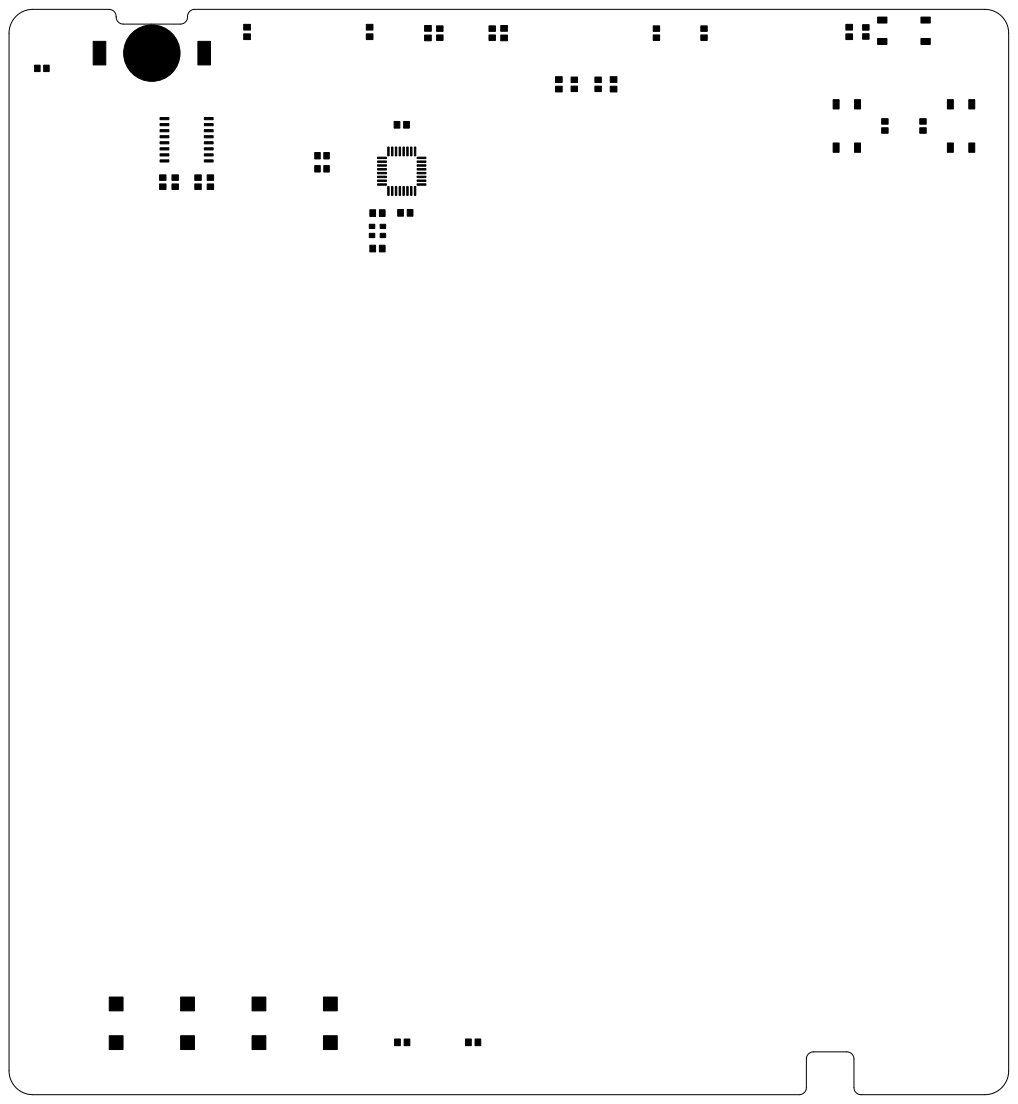
[picture p98: page 1]
