wyolum/ClockFOUR/KiCad/C4_rev1/Gerber/ClockFOUR-Edge_Cuts.pdf

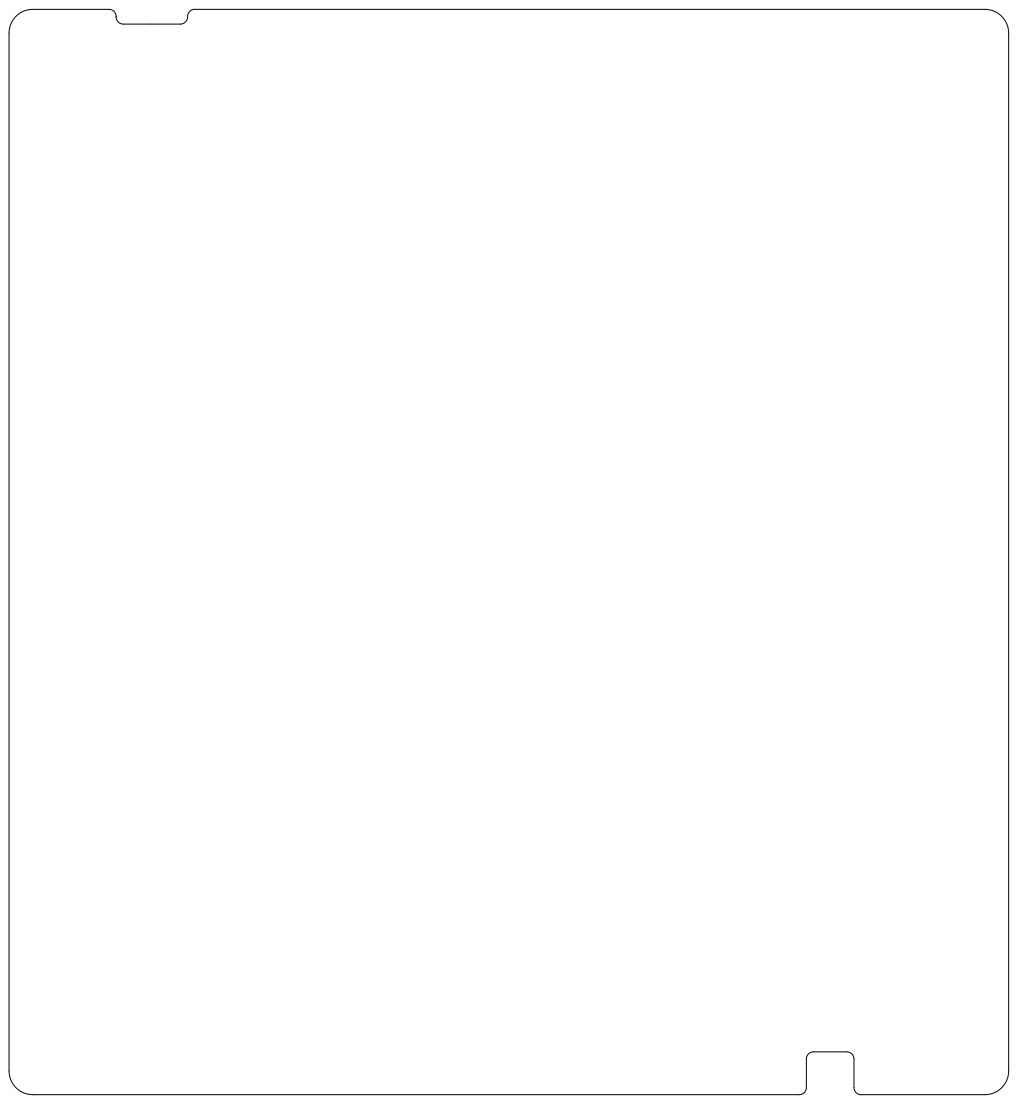
[picture p99: page 1]
