wyolum/ClockFOUR/KiCad/C4_rev1/Gerber/ClockFOUR-F_Cu.pdf

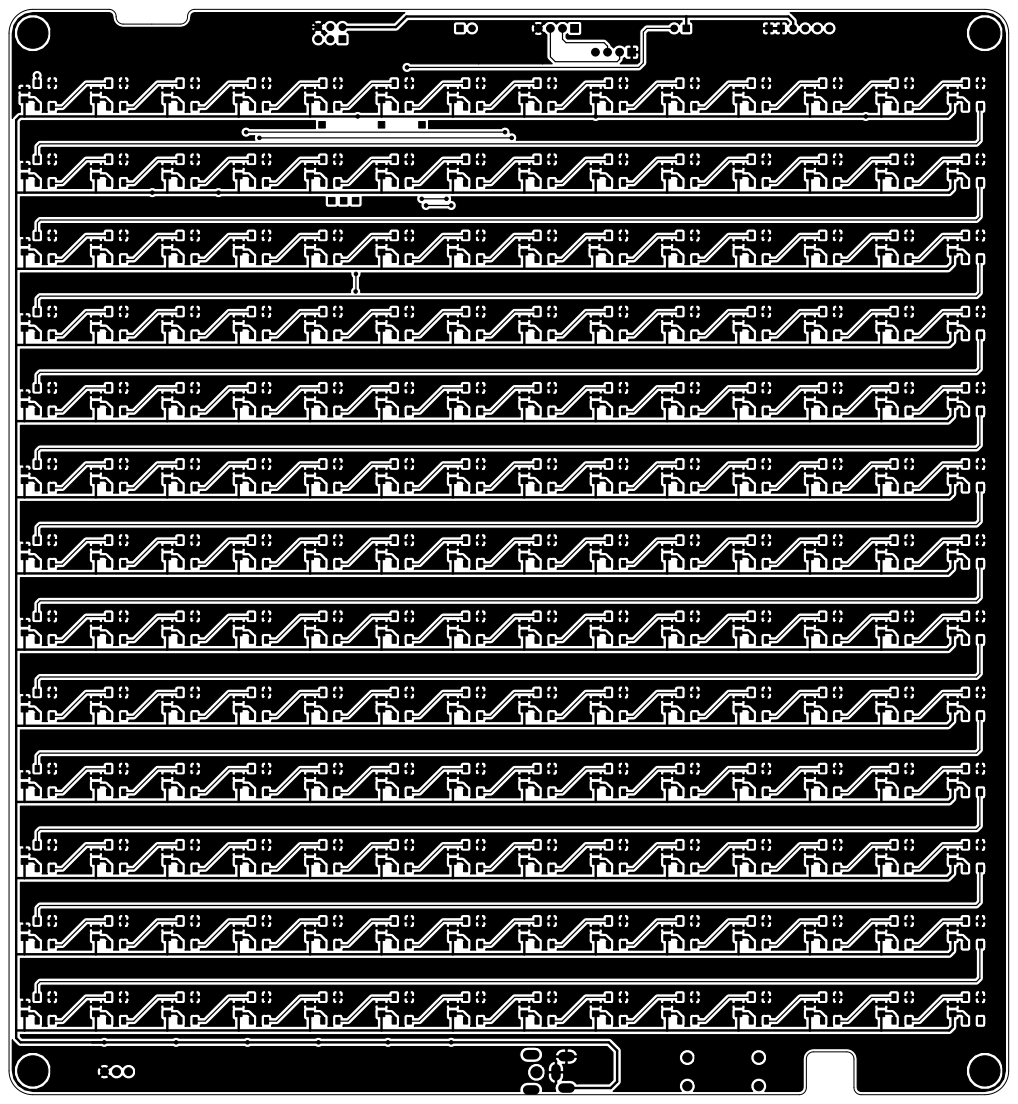
[picture p100: page 1]
