wyolum/ClockFOUR/KiCad/C4_rev1/Gerber/ClockFOUR-F_Mask.pdf

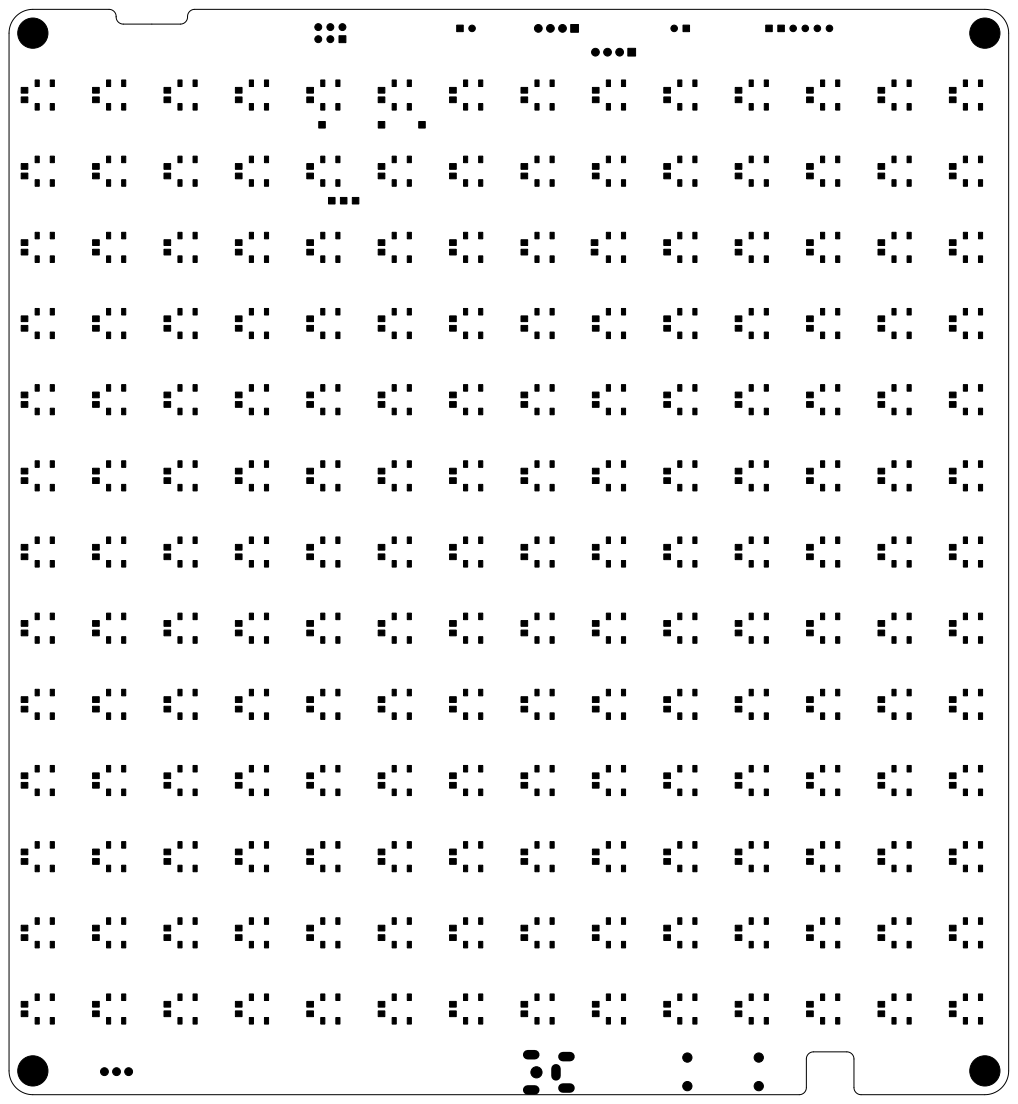
[picture p101: page 1]
