wyolum/ClockFOUR/KiCad/C4_rev1/Gerber/ClockFOUR-F_Paste.pdf

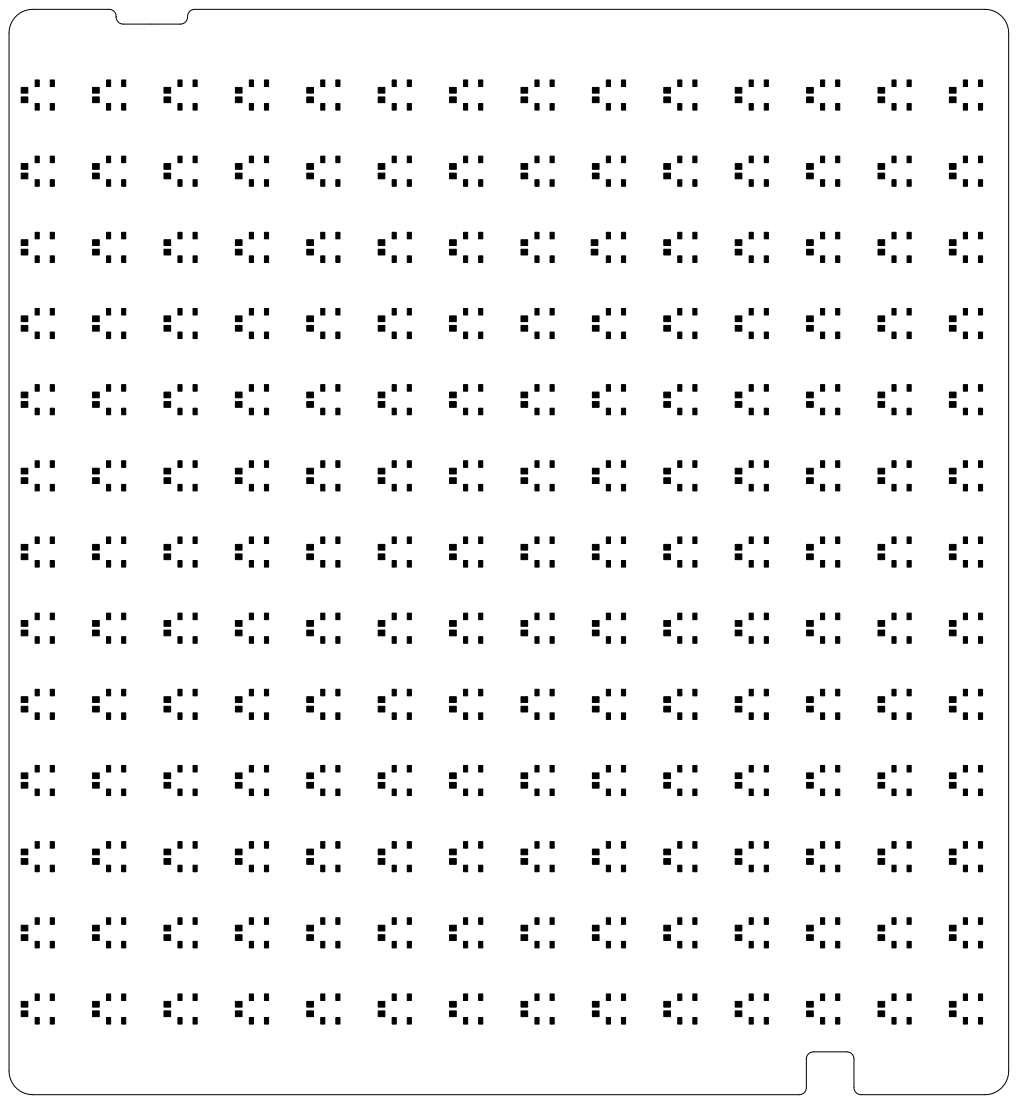
[picture p102: page 1]
