wyolum/ClockFOUR/KiCad/C4_rev1/Gerber/ClockFOUR-F_SilkS.pdf

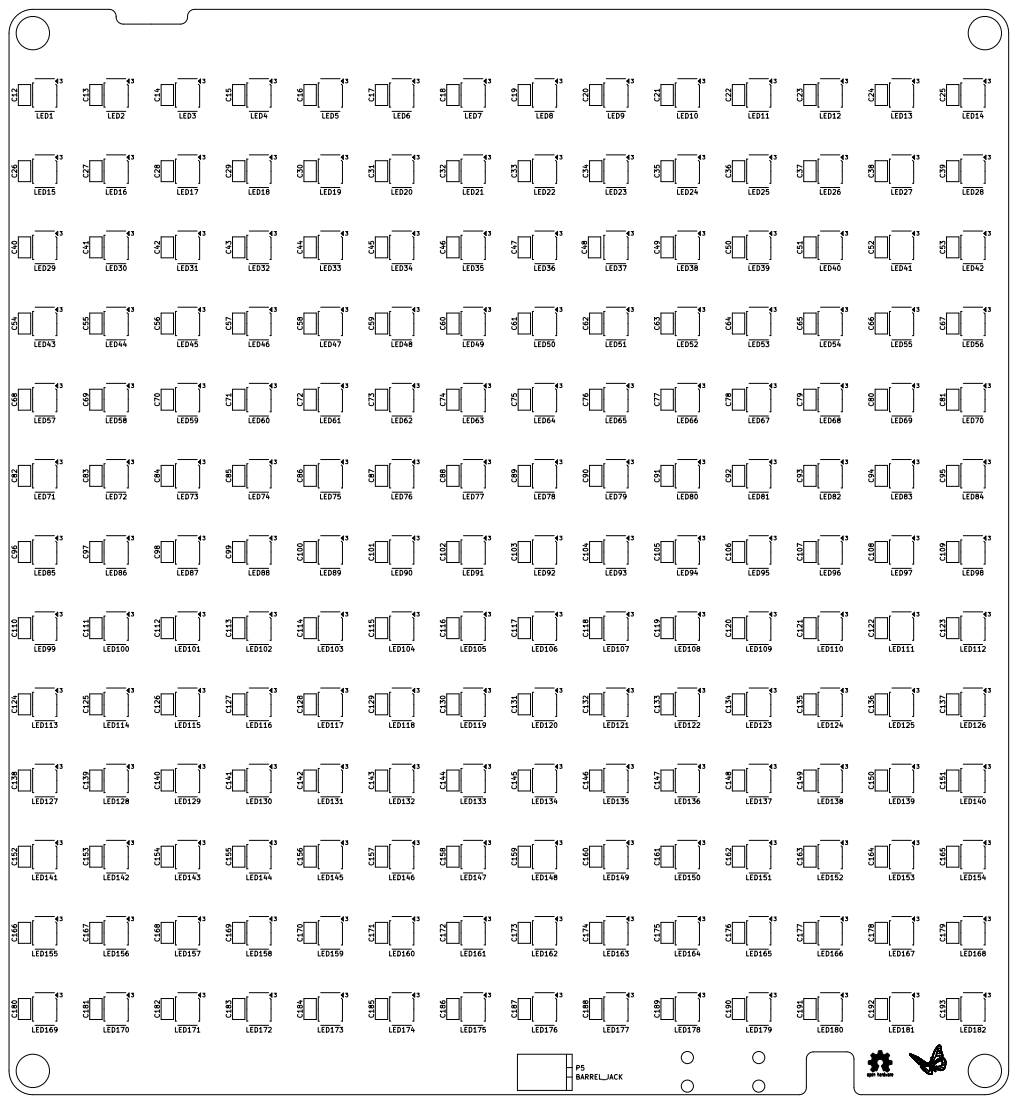
[picture p103: page 1]
