wyolum/ClockFOUR/arduino/ClockFOUR_v1/LANGUAGE_English_v1.h

/*
 * Clock_v1 faceplate file
 * 
 * 
 *  Author: David Pincus
 *  Licence: http://creativecommons.org/licenses/by/3.0/
 *  Description:
 *    30 x 30 Word clock in English
 * 
 *    0 1 2 3 4 5 6 7 8 910111213
 *  0 T W E N T Y D P T H I R T Y
 *  1 F O R T Y F I F T Y B T E N
 *  2 T H I R T E E N O N E T W O
 *  3 F O U R T E E N A F I V E K
 *  4 F I F T E E N S I X T E E N 
 *  5 S E V E N T E E N T H R E E
 *  6 E I G H T E E N E L E V E N
 *  7 N I N E T E E N T W E L V E
 *  8 E M I N U T E S T P A S T O
 *  9 T W O N E I G H T E N S I X
 *  10T H R E E N I N E L E V E N
 *  11F O U R F I V E T W E L V E
 *  12S E V E N D L P O C L O C K
 */

const uint8_t WORDS_min[] PROGMEM = {   // minute words
     28,          // # words
	8,  2, 3,   //one
	11, 2, 3,   //two
	9,  5, 5,   //three
	0,  3, 4,   //four
	9,  3, 4,   //five
	7,  4, 3,   //six
	0,  5, 5,   //seven
	0,  6, 5,   //eight
	0,  7, 4,   //nine
	11, 1, 3,   //ten
	8,  6, 6,   //eleven
	8,  7, 6,   //twelve
	0,  2, 8,   //thirteen
	0,  3, 8,   //fourteen
	0,  4, 7,   //fifteen
	7,  4, 7,   //sixteen
	0,  5, 9,   //seventeen
	0,  6, 8,   //eighteen
	0,  7, 8,   //nineteen
	0,  0, 6,   //twenty
	8,  0, 6,   //thirty
	0,  1, 5,   //forty
	5,  1, 5,   //fifty
	1,  8, 6,   //minute
	1,  8, 7,   //minutes
	9,  8, 4,   //past
	12, 8, 2,   //to
	8, 12, 6,   //oclock
};


const uint8_t DISPLAY_min[] PROGMEM = {
   4, 			 // number of bytes per state
//	  essfftto     sffttetn     mffttnes         otpm          xx:MM
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
	0b00100000,  0b00000000,     //17:xx
	0b01000000,  0b00000000,     //18:xx
	0b10000000,  0b00000000,     //19:xx
	0b00000000,  0b00000001,     //20:xx
	0b00000000,  0b00000010,     //21:xx
	0b00000000,  0b00000100,     //22:xx
	0b00000000,  0b00001000,     //23:xx
};
