wyolum/ClockFOUR/arduino/ClockFOUR_v1/bitmaps.h

/*
 * bitmaps.h
 *
 * Created: 7/12/2014
 *  Author: David
 */ 


#ifndef BITMAPS_H_
#define BITMAPS_H_

#include <avr/pgmspace.h>

const uint8_t Hour_bw_bmp[] PROGMEM = {
	14,
	13,
	0x00, 0x00,
	0x00, 0x00,
	0x00, 0x02,
	0x20, 0x08,
	0x80, 0x22,
	0x00, 0xf8,
	0x02, 0x20,
	0x08, 0x80,
	0x22, 0x00,
	0x00, 0x00,
	0x00, 0x00,
	0x00,
};


const uint8_t Min_bw_bmp[] PROGMEM = {
	14,
	13,
	0x00, 0x00,
	0x00, 0x00,
	0x00, 0x0f,
	0x70, 0x22,
	0x20, 0x88,
	0x82, 0x22,
	0x08, 0x88,
	0x22, 0x20,
	0x88, 0x80,
	0x00, 0x00,
	0x00, 0x00,
	0x00,
};

const uint8_t Circle_bw_bmp[] PROGMEM = {
	14,
	13,
	0x00, 0x00,
	0x00, 0x00,
	0x78, 0x03,
	0xf0, 0x1f,
	0xe0, 0x7f,
	0x81, 0xfe,
	0x07, 0xf8,
	0x0f, 0xc0,
	0x1e, 0x00,
	0x00, 0x00,
	0x00, 0x00,
	0x00,
};

const uint8_t Set_bw_bmp[] PROGMEM = {
	14,
	13,
	0x00, 0x00,
	0x00, 0x00,
	0x01, 0x0e,
	0x04, 0x40,
	0x39, 0x06,
	0x43, 0x25,
	0x02, 0xf4,
	0x0a, 0x11,
	0xc7, 0x20,
	0x00, 0x00,
	0x00, 0x00,
	0x00,
};

const uint8_t C_bw_bmp[] PROGMEM = {
	14,
	13,
	0x00, 0x00,
	0x1e, 0x00,
	0x80, 0x04,
	0x00, 0x10,
	0x00, 0x40,
	0x01, 0x00,
	0x02, 0x00,
	0x07, 0x80,
	0x00, 0x00,
	0x00, 0x0f,
	0xf8, 0x3f,
	0xe0,
};

const uint8_t Arrow_bw_bmp[] PROGMEM = {
	14,
	13,
	0x03, 0x00, 
	0x0c, 0x00, 
	0x30, 0x00, 
	0xc0, 0x03, 
	0x00, 0x0c, 
	0x06, 0x31, 
	0x9c, 0xce, 
	0x3b, 0x70, 
	0x7f, 0x80, 
	0xfc, 0x01, 
	0xe0, 0x03, 
	0x00,
};

const uint8_t A_bw_bmp[] PROGMEM = {
	14,
	13,
	0x00, 0x00, 
	0x00, 0x00, 
	0x30, 0x01, 
	0x20, 0x08, 
	0x40, 0x21, 
	0x00, 0x84, 
	0x03, 0xf0, 
	0x08, 0x40, 
	0x21, 0x00, 
	0x84, 0x00, 
	0x00, 0x00, 
	0x00,
};

const uint8_t bars_1_bw_bmp[] PROGMEM = {
	14,
	13,
	0x00, 0x00, 
	0x00, 0x00, 
	0x00, 0x00, 
	0x00, 0x00, 
	0x00, 0x00, 
	0x00, 0x00, 
	0x00, 0x00, 
	0x00, 0x00, 
	0x00, 0x02, 
	0x00, 0x00, 
	0x00, 0x00, 
	0x00,
};

const uint8_t bars_2_bw_bmp[] PROGMEM = {
	14,
	13,
	0x00, 0x00, 
	0x00, 0x00, 
	0x00, 0x00, 
	0x00, 0x00, 
	0x00, 0x00, 
	0x00, 0x00, 
	0x00, 0x00, 
	0x08, 0x00, 
	0x20, 0x02, 
	0x80, 0x00, 
	0x00, 0x00, 
	0x00,
};

const uint8_t bars_3_bw_bmp[] PROGMEM = {
	14,
	13,
	0x00, 0x00, 
	0x00, 0x00, 
	0x00, 0x00, 
	0x00, 0x00, 
	0x00, 0x00, 
	0x00, 0x20, 
	0x00, 0x80, 
	0x0a, 0x00, 
	0x28, 0x02, 
	0xa0, 0x00, 
	0x00, 0x00, 
	0x00,
};

const uint8_t bars_4_bw_bmp[] PROGMEM = {
	14,
	13,
	0x00, 0x00, 
	0x00, 0x00, 
	0x00, 0x00, 
	0x00, 0x00, 
	0x80, 0x02, 
	0x00, 0x28, 
	0x00, 0xa0, 
	0x0a, 0x80, 
	0x2a, 0x02, 
	0xa8, 0x00, 
	0x00, 0x00, 
	0x00,
};

const uint8_t bars_5_bw_bmp[] PROGMEM = {
	14,
	13,
	0x00, 0x00, 
	0x00, 0x00, 
	0x02, 0x00, 
	0x08, 0x00, 
	0xa0, 0x02, 
	0x80, 0x2a, 
	0x00, 0xa8, 
	0x0a, 0xa0, 
	0x2a, 0x82, 
	0xaa, 0x00, 
	0x00, 0x00, 
	0x00,
};

const uint8_t Brightness_bw_bmp[] PROGMEM = {
	14,
	13,
	0x00, 0x00, 
	0x08, 0x02, 
	0x01, 0x01, 
	0xe0, 0x08, 
	0x40, 0x40, 
	0x85, 0x02, 
	0x84, 0x08, 
	0x08, 0x40, 
	0x1e, 0x02, 
	0x01, 0x00, 
	0x40, 0x00, 
	0x00,
};


#endif /* BITMAPS_H_ */
